nyquist-labs/projects/projects/applied-math/B-fourier-analysis-and-transforms/AM024-zero-padding-vs-resolution/README.md

# AM-024 · Zero-padding vs resolution: what interpolation does not add

> Show that zero-padding interpolates the spectrum (sharper-looking peaks, better frequency *estimates*) but cannot separate two tones closer than about 1/T — only a longer record can. The resolvability threshold is predicted and measured.

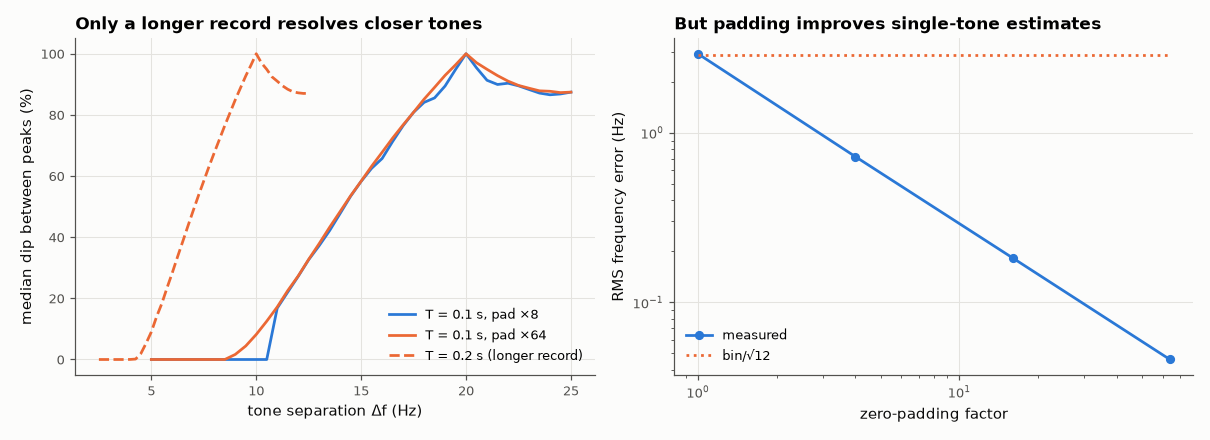
[picture p153: projects/applied-math/B-fourier-analysis-and-transforms/AM024-zero-padding-vs-resolution/figures/zeropad.png]
Zero-padding vs resolution: what interpolation does not add


*Two-tone resolvability vs separation for different padding factors and record lengths; single-tone estimation error vs padding.*

**Track:** Applied Mathematics — 218 projects in electrical engineering · **Category:** B. Fourier analysis & transforms · **Level:** Easy · **Tools:** FFT with and without zero-padding, two-tone resolution test, peak-dip criterion

**Data:** Simulated (numerical model in this repo).

## Problem

Padding an FFT with zeros makes the spectrum look smoother. Does it improve resolution?
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
