nyquist-labs/projects/projects/applied-math/B-fourier-analysis-and-transforms/AM029-time-frequency-uncertainty/README.md

# AM-029 · The time–frequency uncertainty bound, measured

> Compute the RMS duration σ_t and RMS bandwidth σ_f of many pulse shapes, show that σ_t·σ_f ≥ 1/(4π) with equality only for the Gaussian, and show that chirping or distorting a pulse moves it away from the bound.

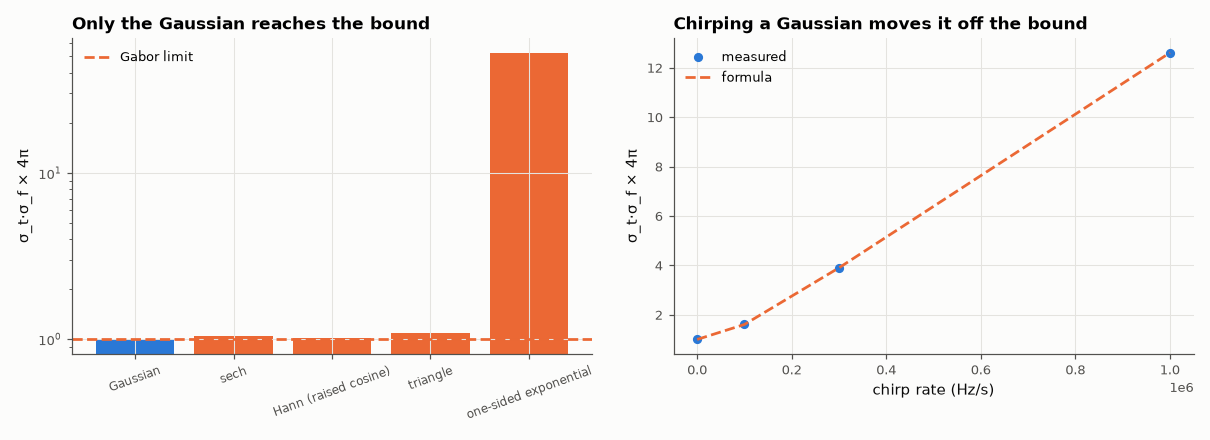
[picture p154: projects/applied-math/B-fourier-analysis-and-transforms/AM029-time-frequency-uncertainty/figures/uncertainty.png]
The time–frequency uncertainty bound, measured

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
