nyquist-labs/projects/projects/applied-math/B-fourier-analysis-and-transforms/AM037-dct-and-compression/figures/dct.png

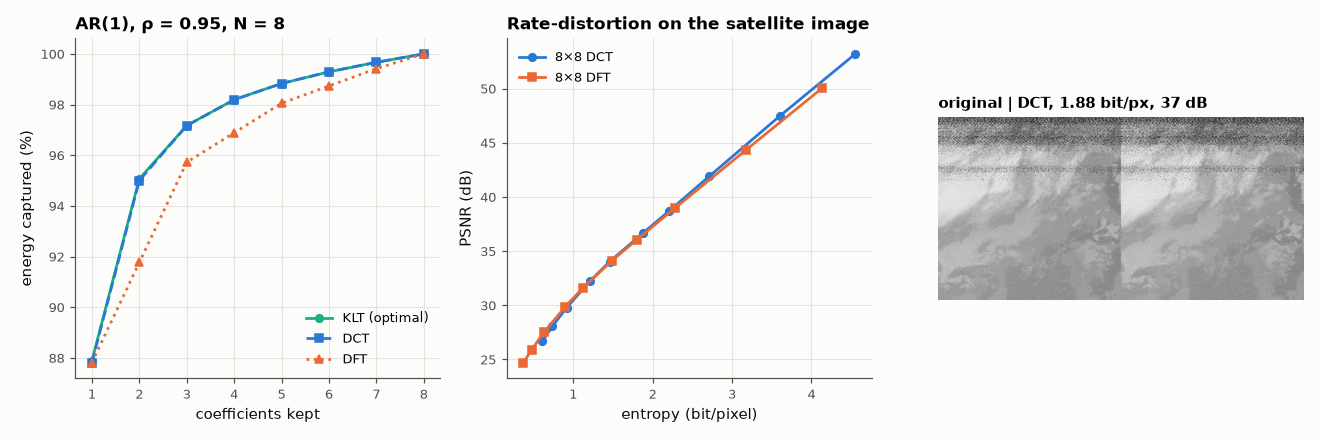
projects/applied-math/B-fourier-analysis-and-transforms/AM037-dct-and-compression/figures/dct.png
