nyquist-labs/projects/projects/applied-math/B-fourier-analysis-and-transforms/AM039-goertzel-algorithm/figures/goertzel.png

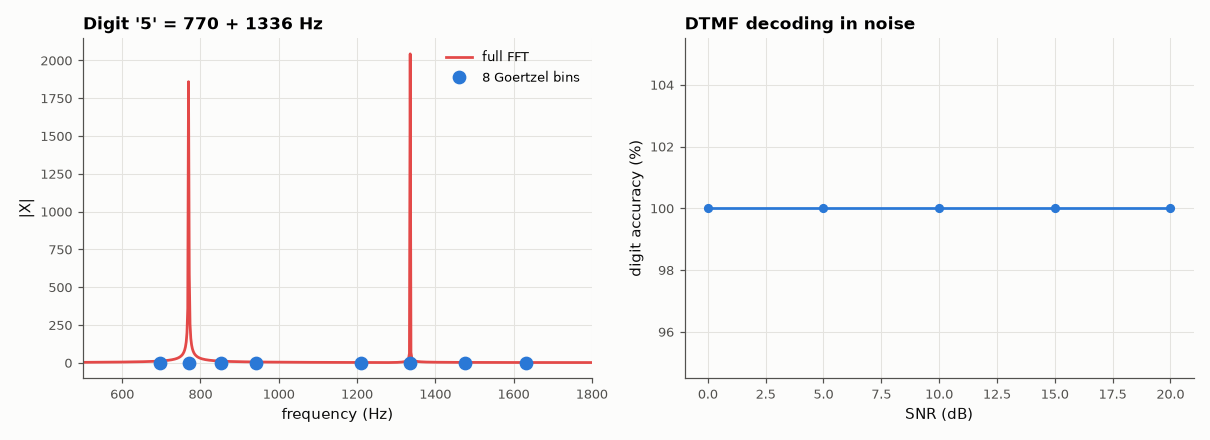
projects/applied-math/B-fourier-analysis-and-transforms/AM039-goertzel-algorithm/figures/goertzel.png
