nyquist-labs/projects/projects/applied-math/B-fourier-analysis-and-transforms/AM041-autocorrelation-and-psd/figures/wiener_khinchin.png

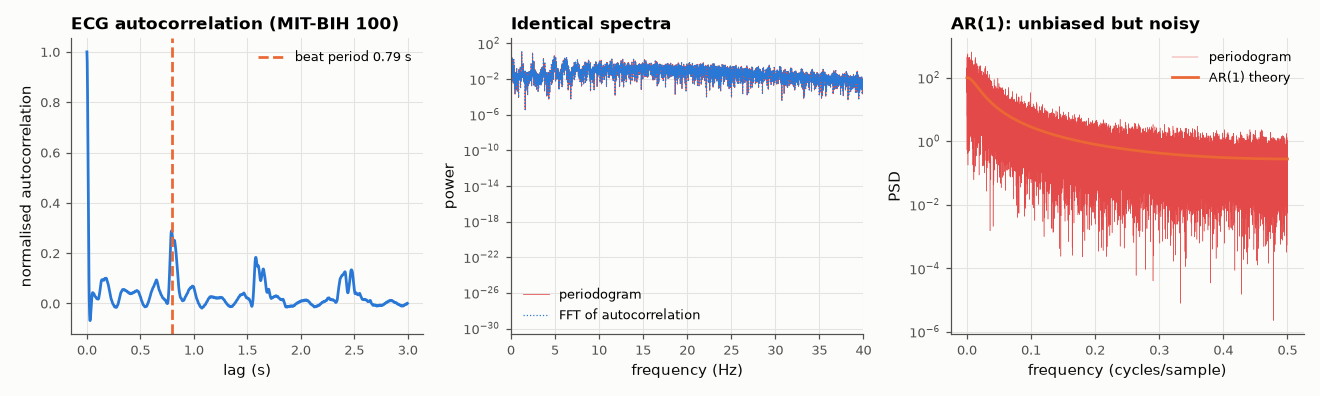
projects/applied-math/B-fourier-analysis-and-transforms/AM041-autocorrelation-and-psd/figures/wiener_khinchin.png
