nyquist-labs/projects/projects/applied-math/C-differential-equations/AM045-rlc-damping-regimes/figures/damping.png

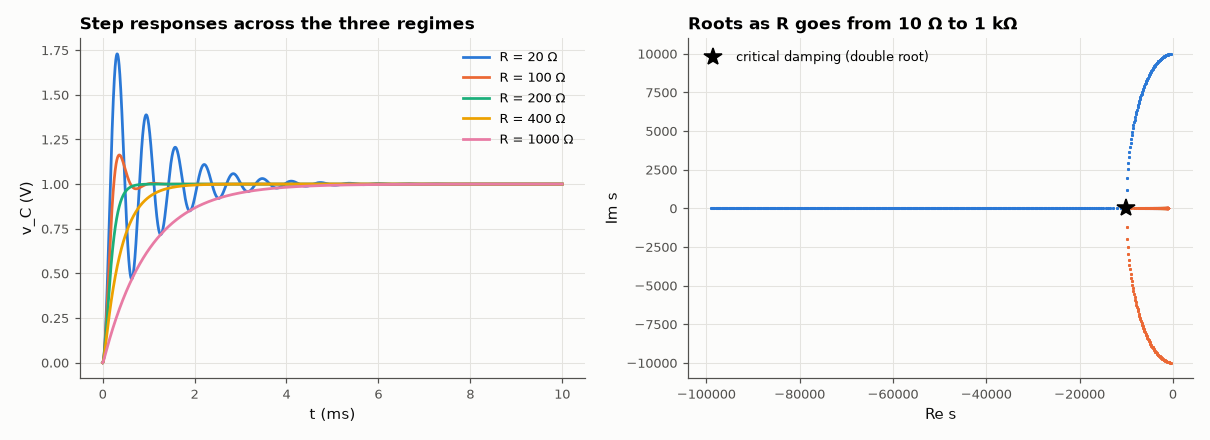
projects/applied-math/C-differential-equations/AM045-rlc-damping-regimes/figures/damping.png
