nyquist-labs/projects/projects/applied-math/C-differential-equations/AM048-stiff-odes-in-switching-circuits/figures/stiff.png

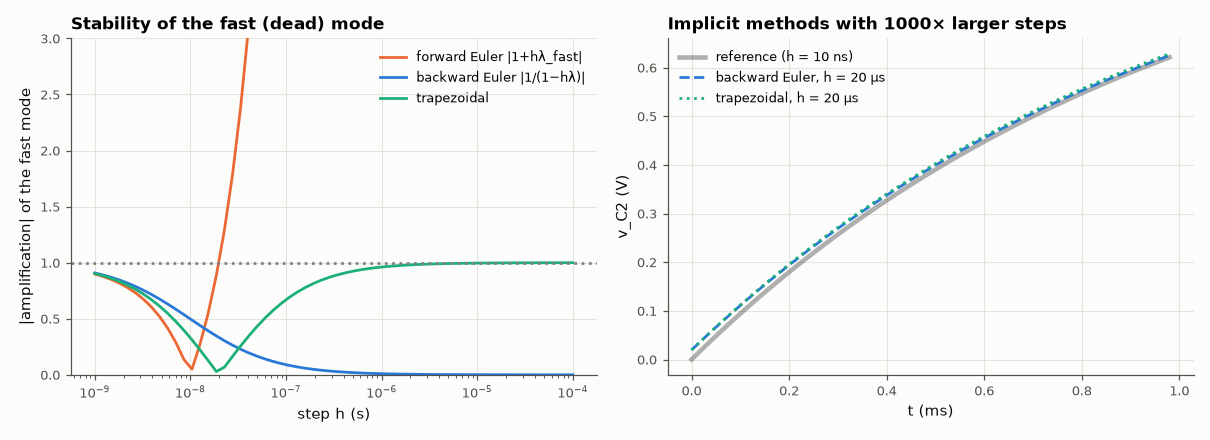
projects/applied-math/C-differential-equations/AM048-stiff-odes-in-switching-circuits/figures/stiff.png
