nyquist-labs/projects/projects/applied-math/C-differential-equations/AM051-thermal-diffusion-model/figures/heat.png

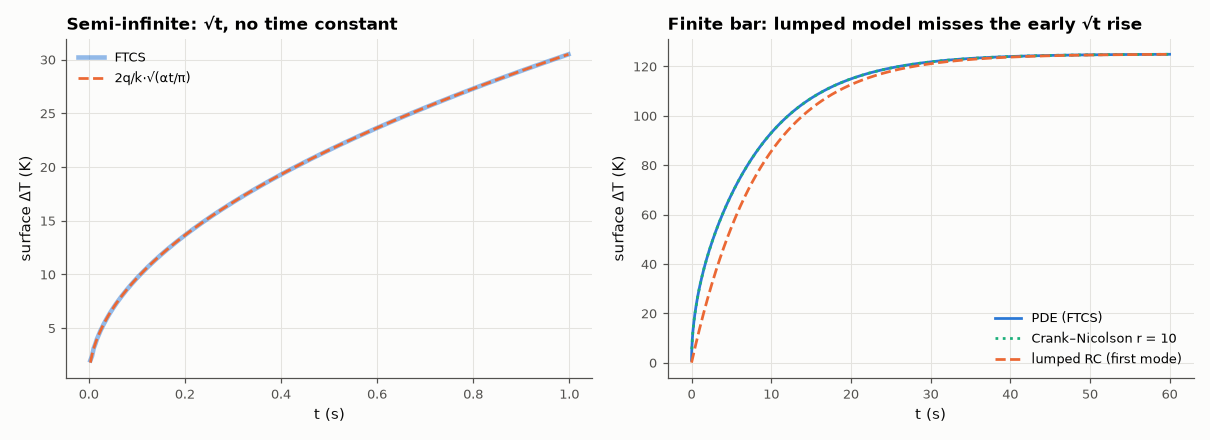
projects/applied-math/C-differential-equations/AM051-thermal-diffusion-model/figures/heat.png
