nyquist-labs/projects/projects/applied-math/C-differential-equations/AM052-1d-wave-equation/figures/wave1d.png

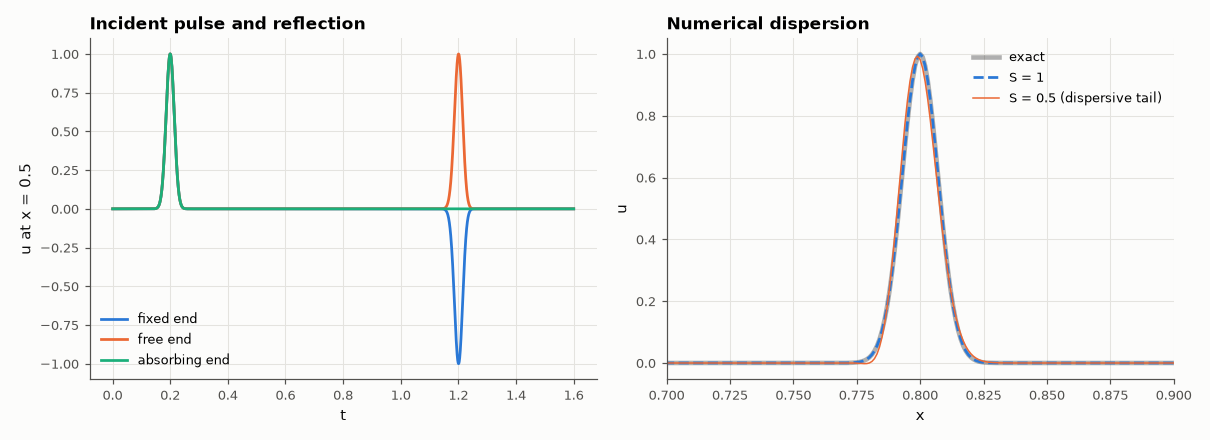
projects/applied-math/C-differential-equations/AM052-1d-wave-equation/figures/wave1d.png
