nyquist-labs/projects/projects/applied-math/C-differential-equations/AM054-van-der-pol-oscillator/figures/vanderpol.png

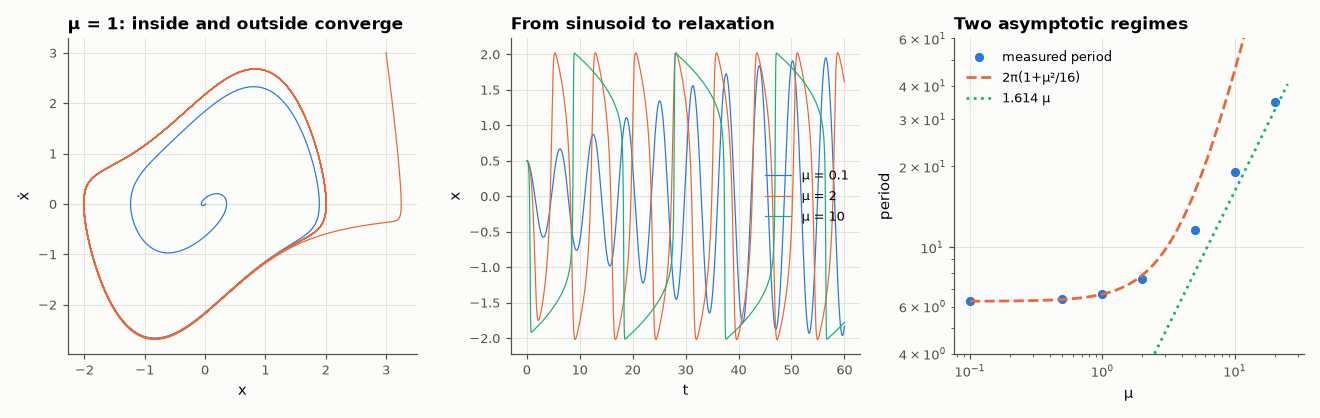
projects/applied-math/C-differential-equations/AM054-van-der-pol-oscillator/figures/vanderpol.png
