nyquist-labs/projects/projects/applied-math/C-differential-equations/AM058-limit-cycles-in-oscillators/figures/limit_cycle.png

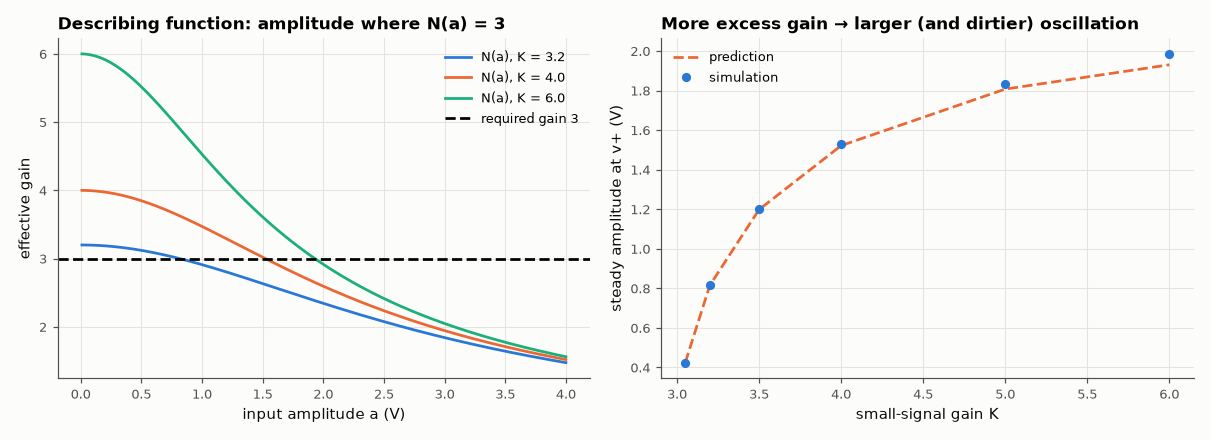
projects/applied-math/C-differential-equations/AM058-limit-cycles-in-oscillators/figures/limit_cycle.png
