nyquist-labs/projects/projects/applied-math/C-differential-equations/AM059-bifurcation-analysis/figures/bifurcation.png

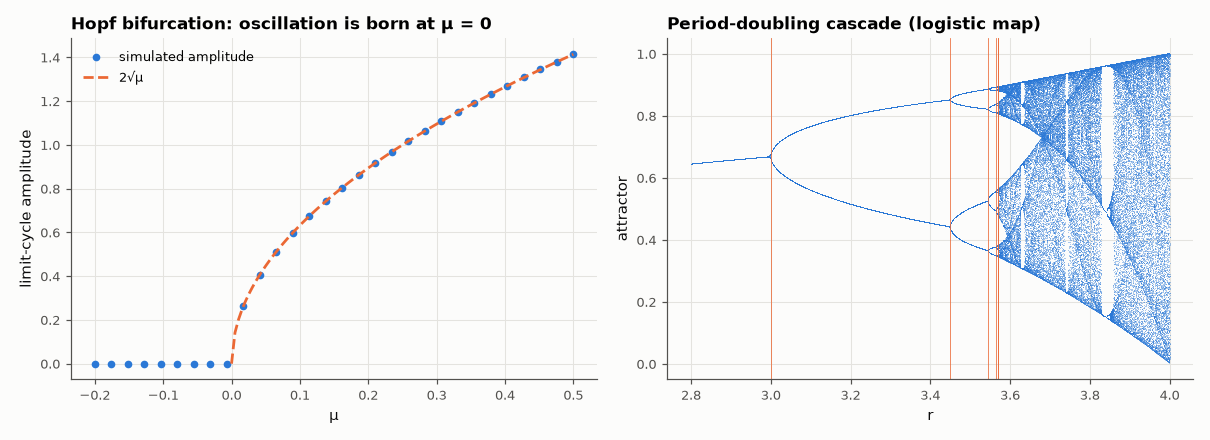
projects/applied-math/C-differential-equations/AM059-bifurcation-analysis/figures/bifurcation.png
