nyquist-labs/projects/projects/applied-math/C-differential-equations/AM060-skin-effect-diffusion/figures/skin.png

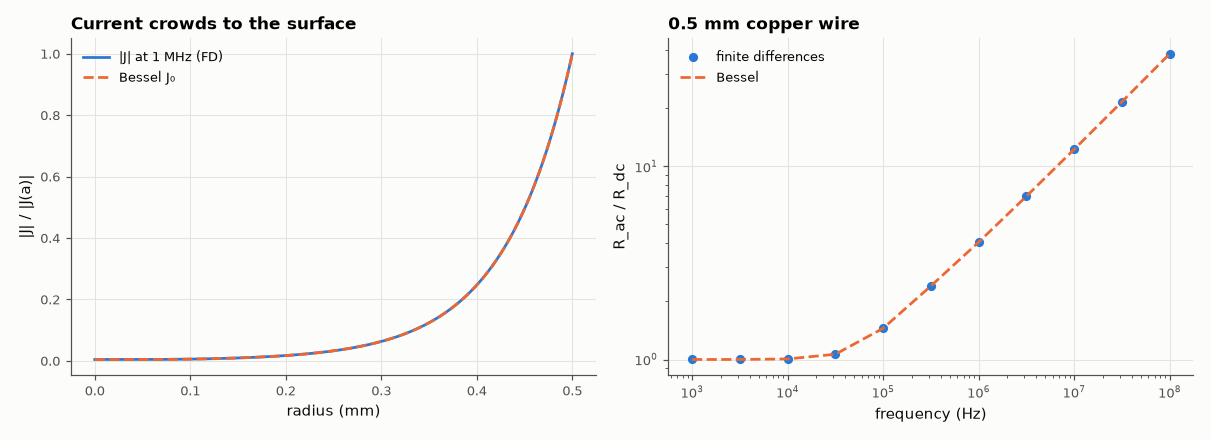
projects/applied-math/C-differential-equations/AM060-skin-effect-diffusion/figures/skin.png
