nyquist-labs/projects/projects/applied-math/D-linear-algebra/AM063-sparse-matrix-solvers/figures/sparse.png

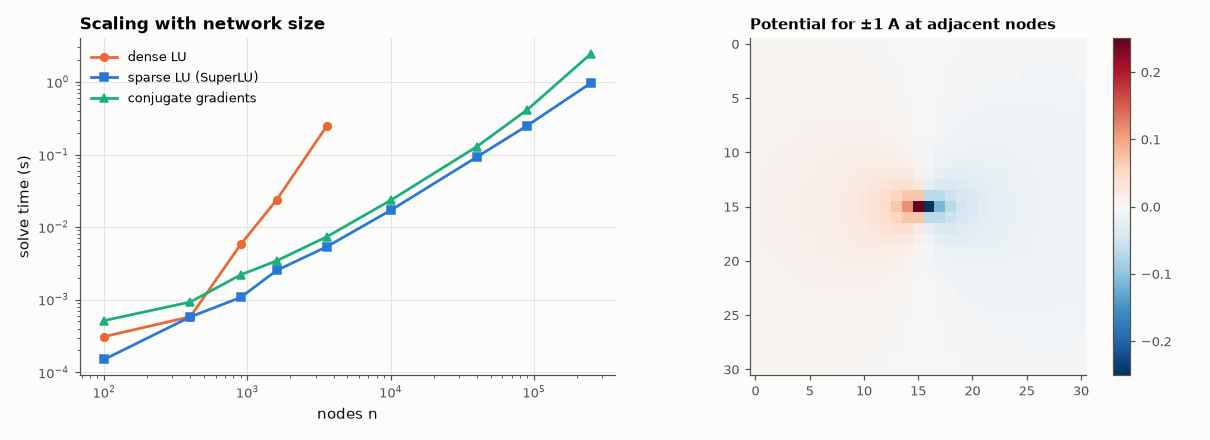
projects/applied-math/D-linear-algebra/AM063-sparse-matrix-solvers/figures/sparse.png
