nyquist-labs/projects/projects/applied-math/D-linear-algebra/AM067-controllability-and-observability/figures/controllability.png

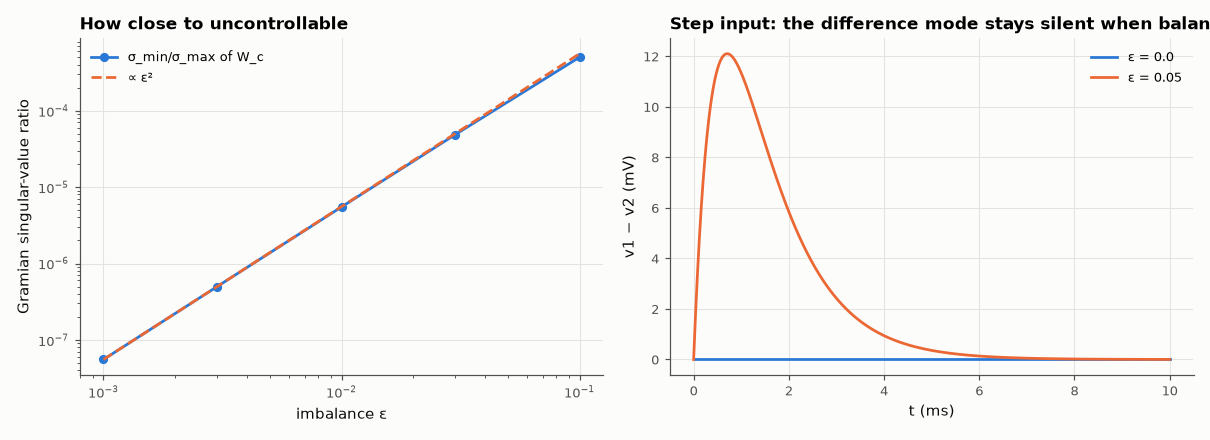
projects/applied-math/D-linear-algebra/AM067-controllability-and-observability/figures/controllability.png
