nyquist-labs/projects/projects/applied-math/D-linear-algebra/AM072-graph-laplacian-of-a-network/figures/laplacian.png

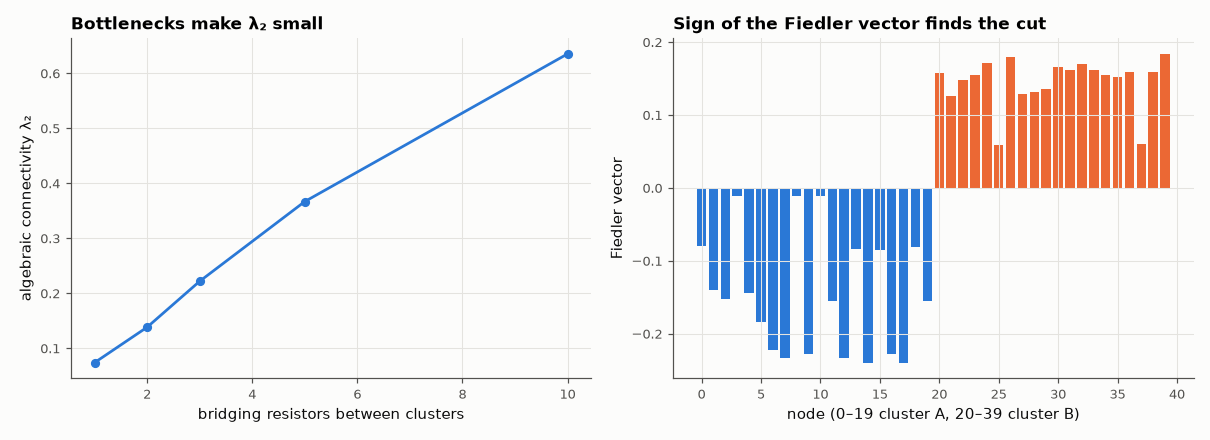
projects/applied-math/D-linear-algebra/AM072-graph-laplacian-of-a-network/figures/laplacian.png
