nyquist-labs/projects/projects/applied-math/D-linear-algebra/AM073-two-port-parameters/figures/twoport.png

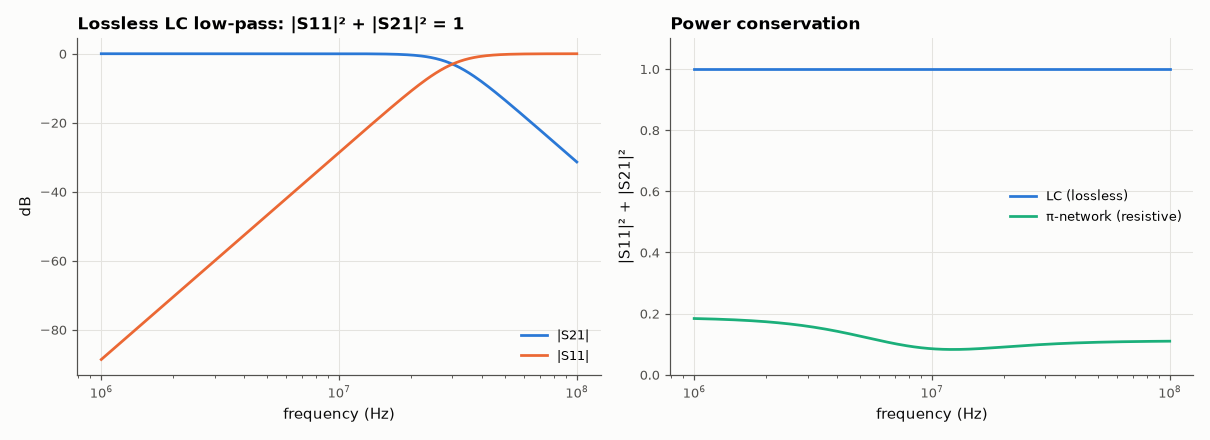
projects/applied-math/D-linear-algebra/AM073-two-port-parameters/figures/twoport.png
