nyquist-labs/projects/projects/applied-math/D-linear-algebra/AM074-cascade-abcd-matrices/figures/abcd.png

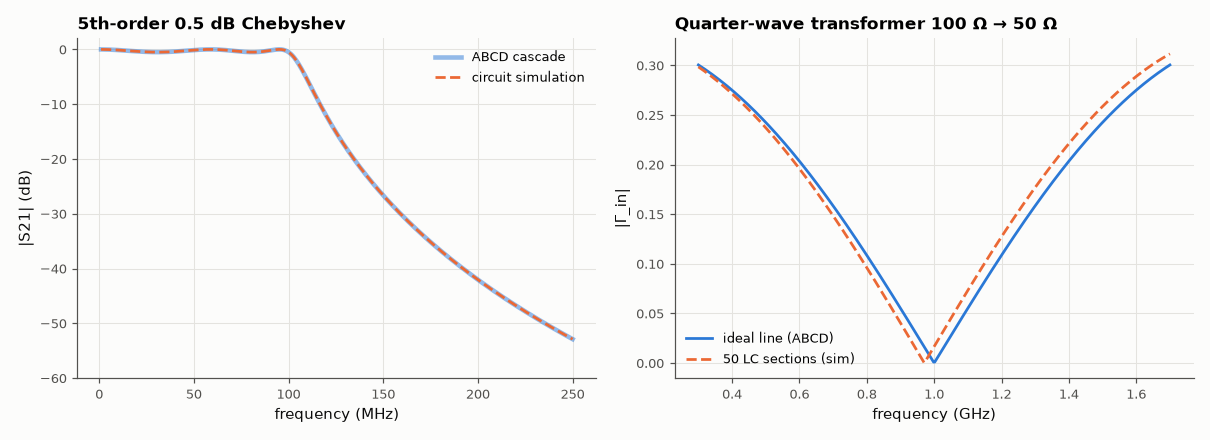
projects/applied-math/D-linear-algebra/AM074-cascade-abcd-matrices/figures/abcd.png
