nyquist-labs/projects/projects/applied-math/D-linear-algebra/AM075-mimo-channel-capacity/figures/mimo.png

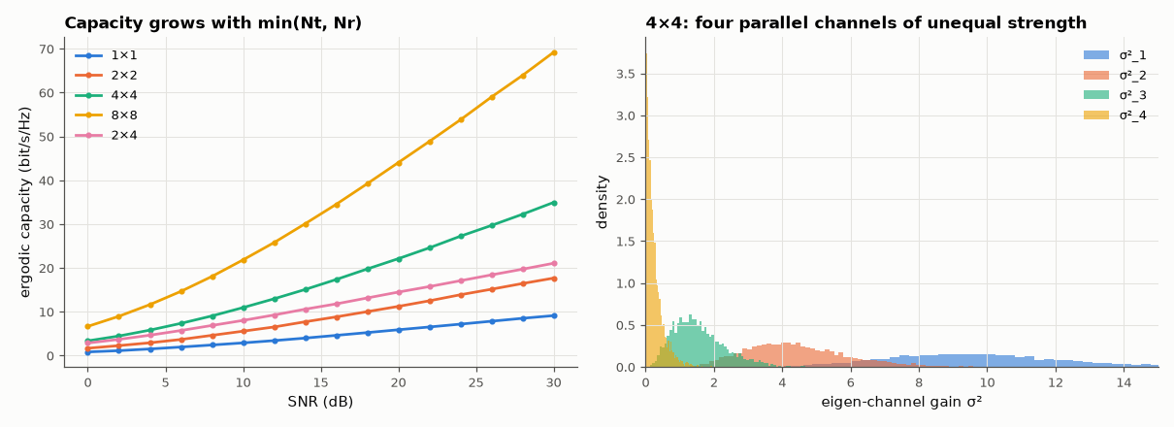
projects/applied-math/D-linear-algebra/AM075-mimo-channel-capacity/figures/mimo.png
