nyquist-labs/projects/projects/applied-math/D-linear-algebra/AM076-beamforming-as-matrix-algebra/figures/beamforming.png

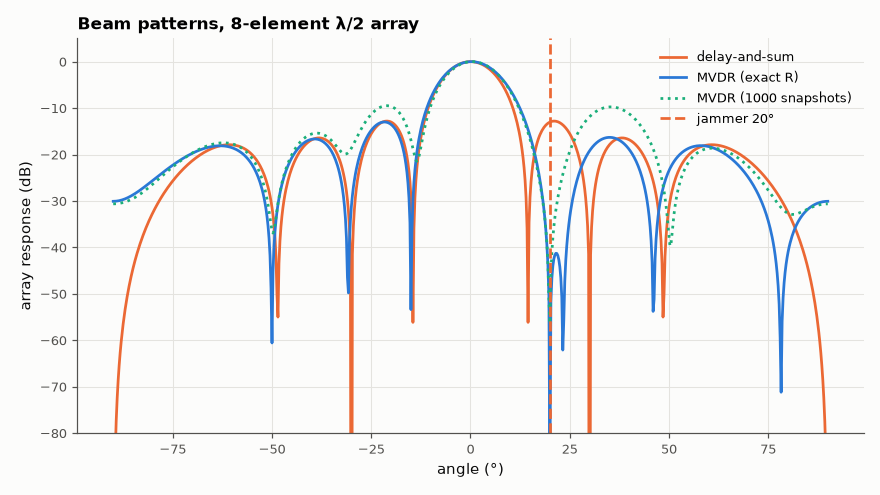
projects/applied-math/D-linear-algebra/AM076-beamforming-as-matrix-algebra/figures/beamforming.png
