nyquist-labs/projects/projects/applied-math/D-linear-algebra/AM078-condition-number-study/figures/conditioning.png

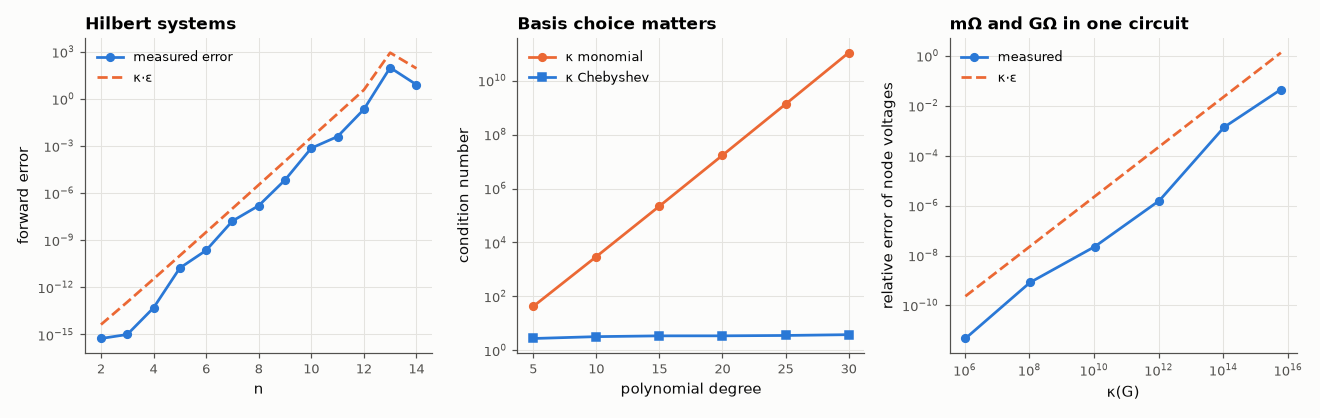
projects/applied-math/D-linear-algebra/AM078-condition-number-study/figures/conditioning.png
