nyquist-labs/projects/projects/applied-math/D-linear-algebra/AM079-krylov-model-reduction/figures/mor.png

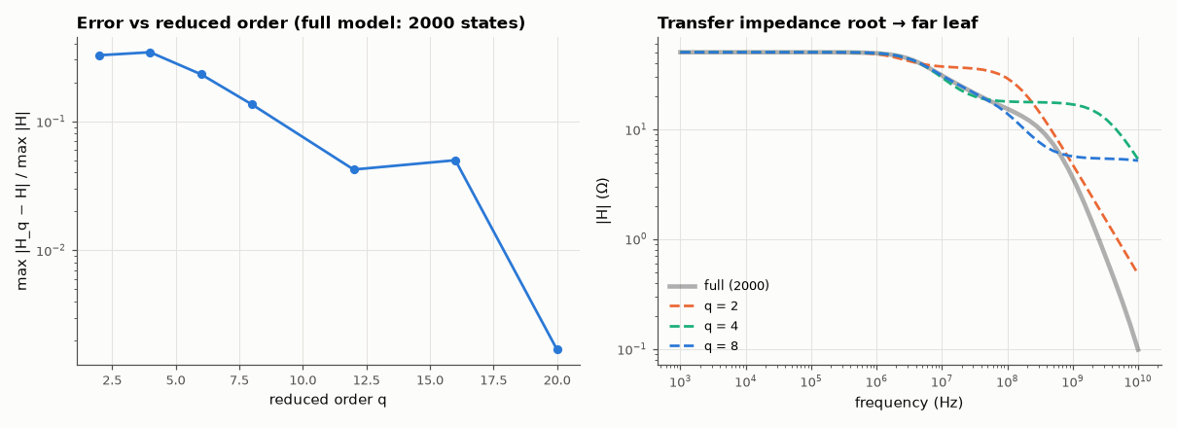
projects/applied-math/D-linear-algebra/AM079-krylov-model-reduction/figures/mor.png
