nyquist-labs/projects/projects/applied-math/E-probability-and-stochastic-processes/AM084-ber-vs-snr-simulation/figures/ber.png

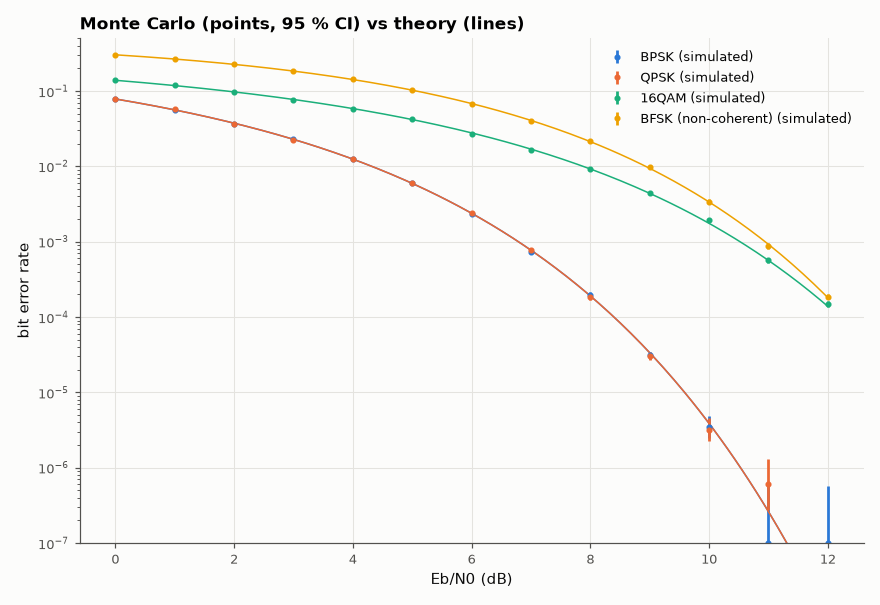
projects/applied-math/E-probability-and-stochastic-processes/AM084-ber-vs-snr-simulation/figures/ber.png
