nyquist-labs/projects/projects/applied-math/E-probability-and-stochastic-processes/AM085-q-function-derivation/figures/qfunction.png

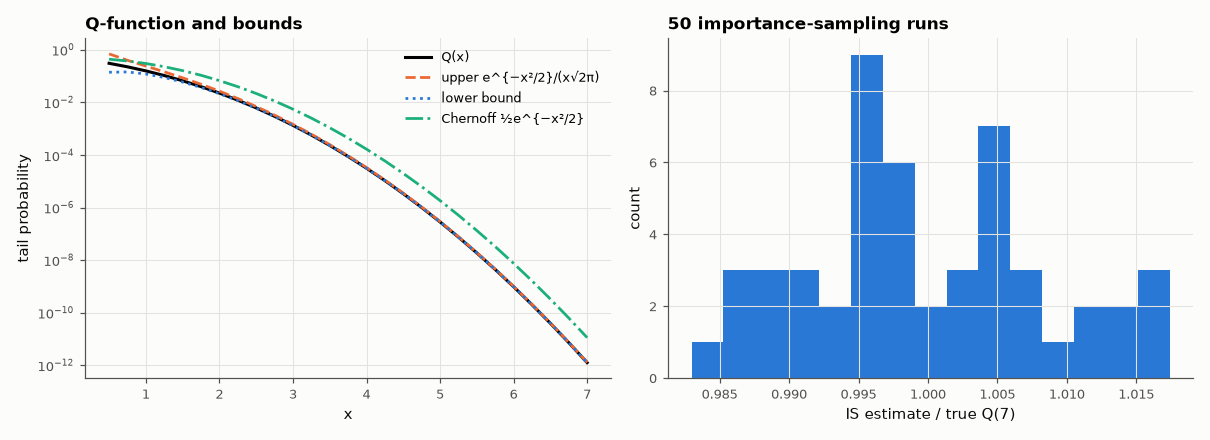
projects/applied-math/E-probability-and-stochastic-processes/AM085-q-function-derivation/figures/qfunction.png
