nyquist-labs/projects/projects/applied-math/E-probability-and-stochastic-processes/AM088-markov-chain-channel-model/figures/gilbert_elliott.png

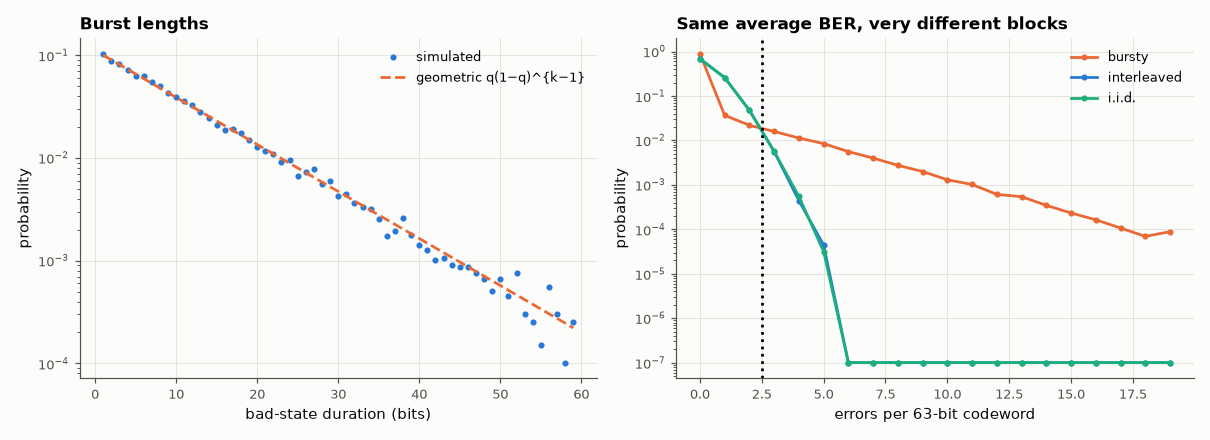
projects/applied-math/E-probability-and-stochastic-processes/AM088-markov-chain-channel-model/figures/gilbert_elliott.png
