nyquist-labs/projects/projects/applied-math/E-probability-and-stochastic-processes/AM092-map-estimation/figures/map.png

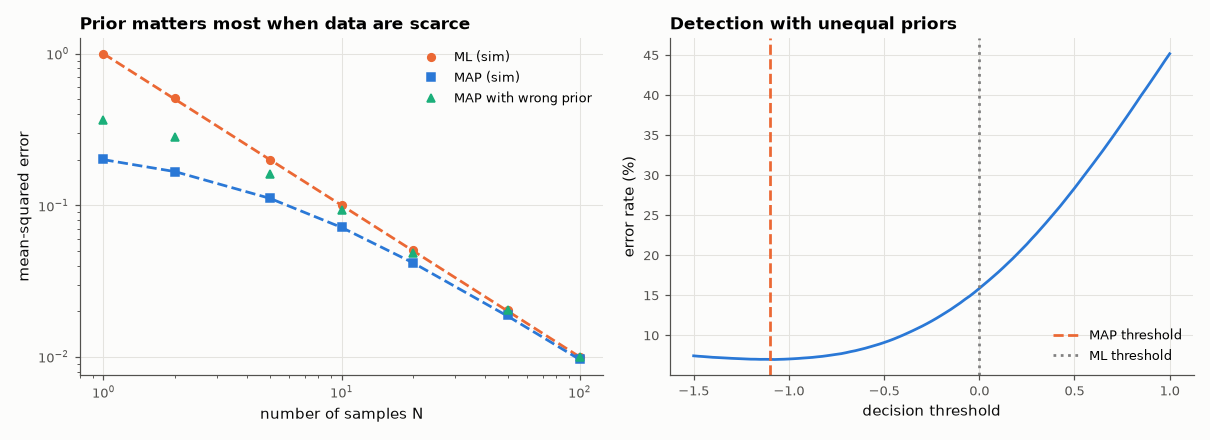
projects/applied-math/E-probability-and-stochastic-processes/AM092-map-estimation/figures/map.png
