nyquist-labs/projects/projects/applied-math/E-probability-and-stochastic-processes/AM096-wiener-filter/figures/wiener.png

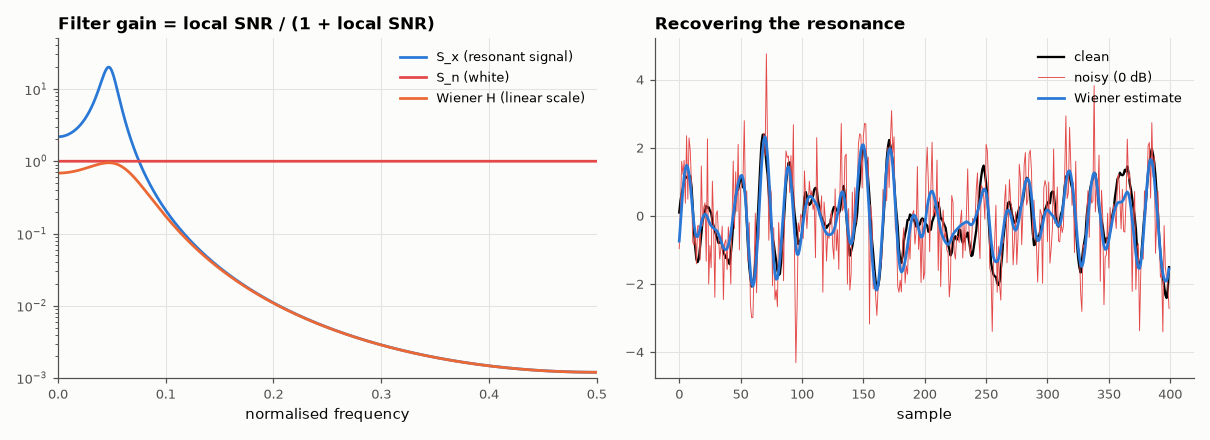
projects/applied-math/E-probability-and-stochastic-processes/AM096-wiener-filter/figures/wiener.png
