nyquist-labs/projects/projects/applied-math/E-probability-and-stochastic-processes/AM097-lms-convergence-analysis/figures/lms.png

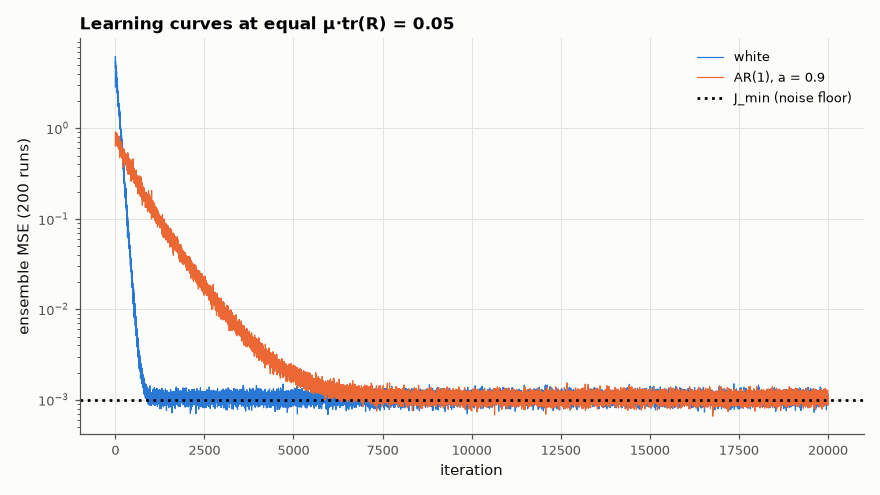
projects/applied-math/E-probability-and-stochastic-processes/AM097-lms-convergence-analysis/figures/lms.png
