nyquist-labs/projects/projects/applied-math/E-probability-and-stochastic-processes/AM098-random-walk-in-circuits/figures/random_walk.png

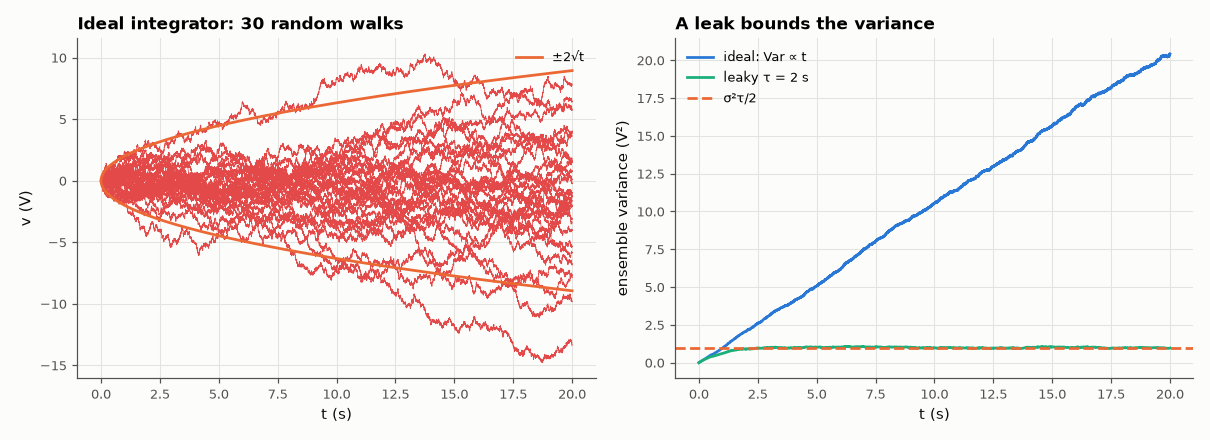
projects/applied-math/E-probability-and-stochastic-processes/AM098-random-walk-in-circuits/figures/random_walk.png
