nyquist-labs/projects/projects/applied-math/F-optimisation/AM101-impedance-matching-optimisation/figures/matching.png

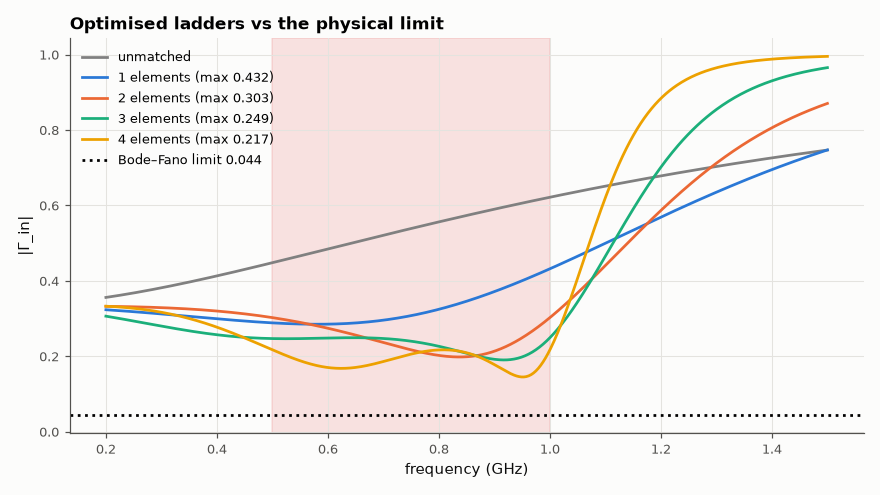
projects/applied-math/F-optimisation/AM101-impedance-matching-optimisation/figures/matching.png
