nyquist-labs/projects/projects/applied-math/F-optimisation/AM103-gradient-descent-parameter-fitting/figures/diode_fit.png

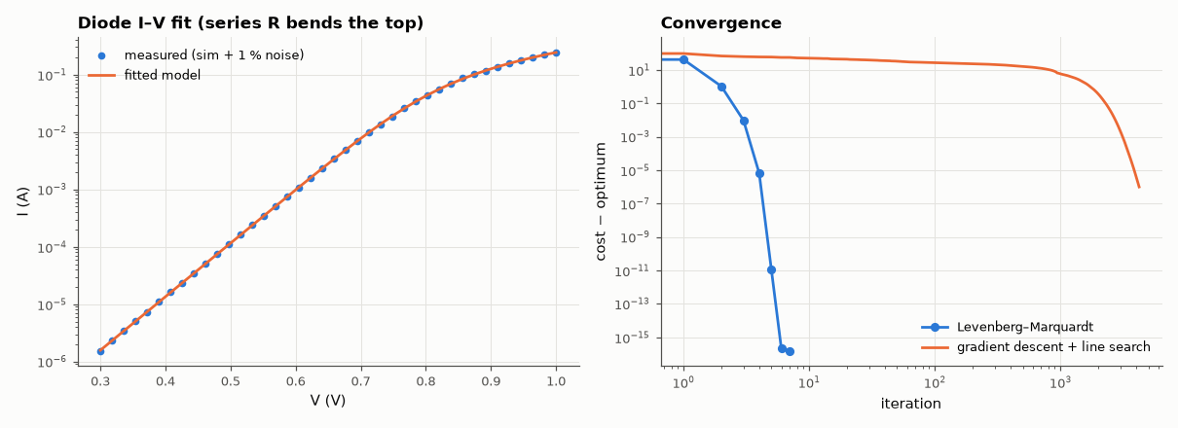
projects/applied-math/F-optimisation/AM103-gradient-descent-parameter-fitting/figures/diode_fit.png
