nyquist-labs/projects/projects/applied-math/F-optimisation/AM109-mppt-as-hill-climbing/figures/mppt.png

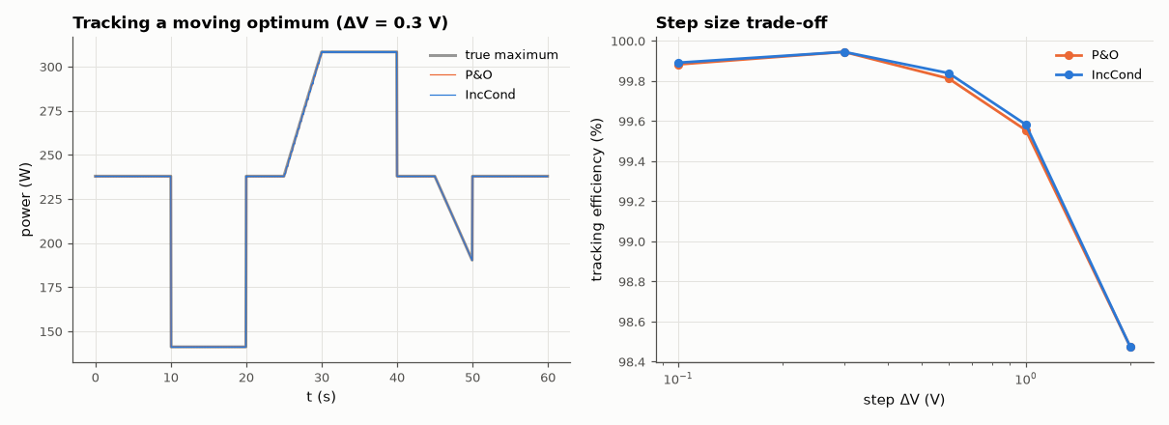
projects/applied-math/F-optimisation/AM109-mppt-as-hill-climbing/figures/mppt.png
