nyquist-labs/projects/projects/applied-math/F-optimisation/AM110-minimax-approximation/figures/minimax.png

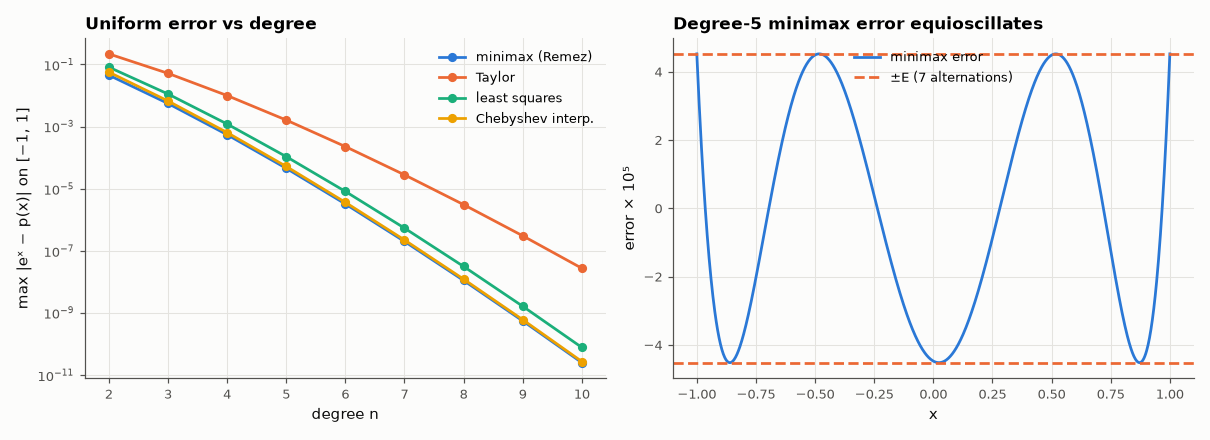
projects/applied-math/F-optimisation/AM110-minimax-approximation/figures/minimax.png
