nyquist-labs/projects/projects/applied-math/F-optimisation/AM111-least-squares-curve-fitting/figures/battery_fit.png

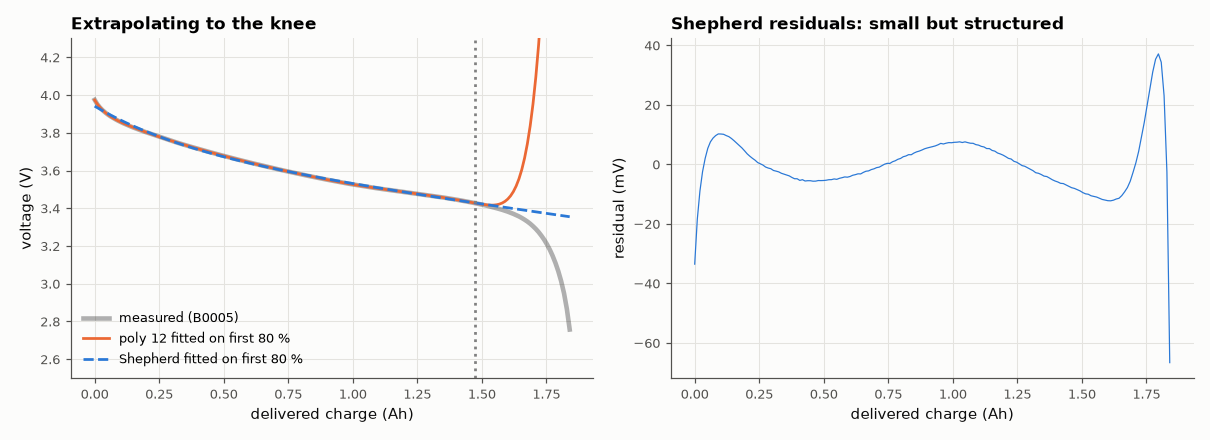
projects/applied-math/F-optimisation/AM111-least-squares-curve-fitting/figures/battery_fit.png
