nyquist-labs/projects/projects/applied-math/F-optimisation/AM114-multi-objective-trade-study/figures/pareto.png

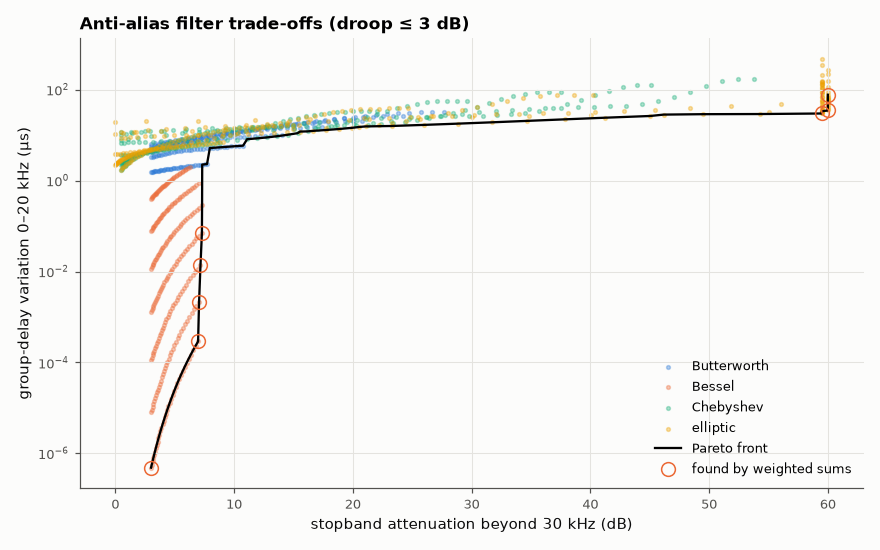
projects/applied-math/F-optimisation/AM114-multi-objective-trade-study/figures/pareto.png
