nyquist-labs/projects/projects/applied-math/G-numerical-methods/AM116-transient-integration-methods/figures/trap_vs_be.png

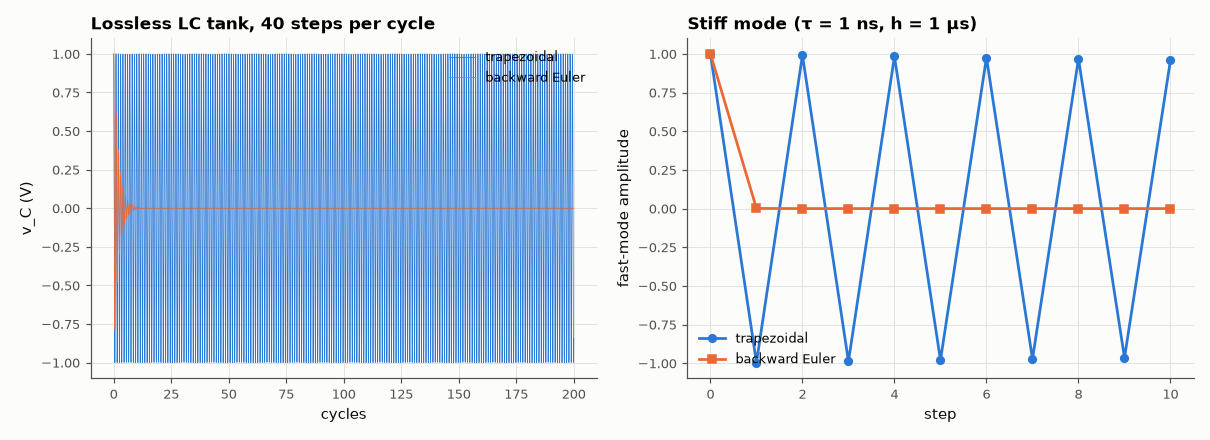
projects/applied-math/G-numerical-methods/AM116-transient-integration-methods/figures/trap_vs_be.png
