nyquist-labs/projects/projects/applied-math/G-numerical-methods/AM119-finite-element-basics/figures/fem_coax.png

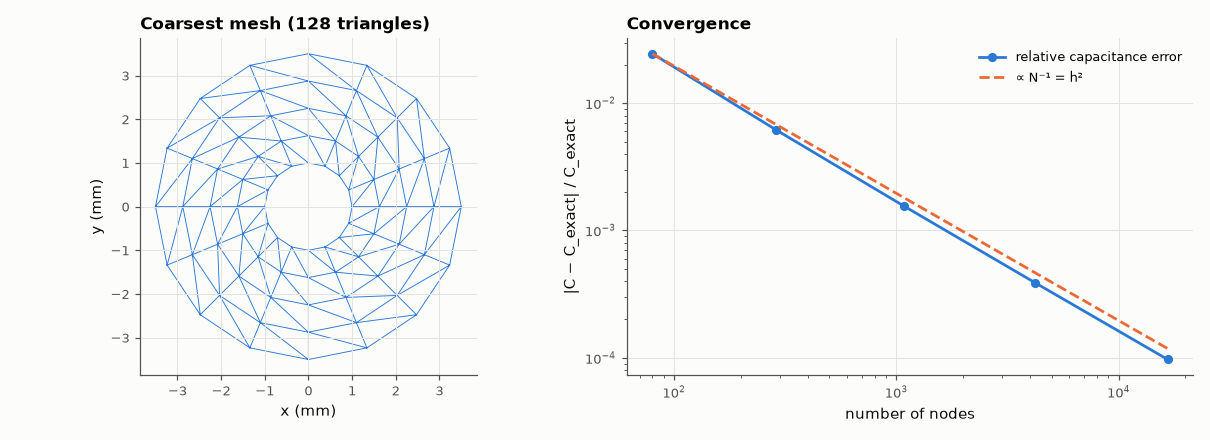
projects/applied-math/G-numerical-methods/AM119-finite-element-basics/figures/fem_coax.png
