nyquist-labs/projects/projects/applied-math/G-numerical-methods/AM120-method-of-moments/figures/mom.png

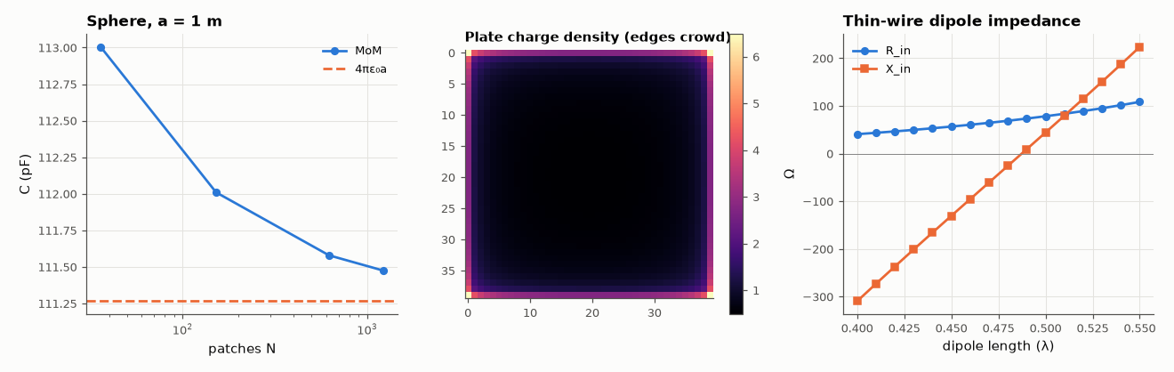
projects/applied-math/G-numerical-methods/AM120-method-of-moments/figures/mom.png
