nyquist-labs/projects/projects/applied-math/G-numerical-methods/AM121-numerical-fourier-coefficients/figures/fourier_quadrature.png

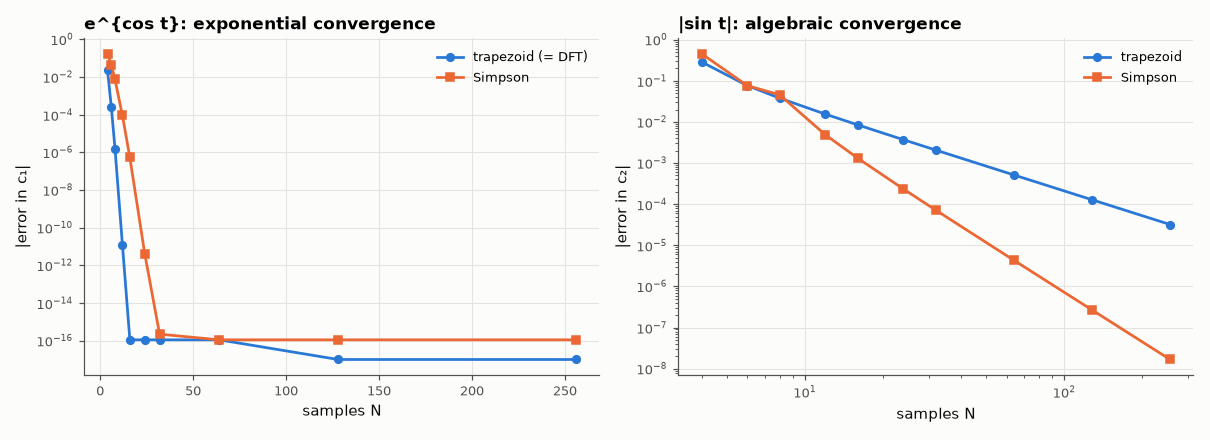
projects/applied-math/G-numerical-methods/AM121-numerical-fourier-coefficients/figures/fourier_quadrature.png
