nyquist-labs/projects/projects/applied-math/G-numerical-methods/AM124-fixed-vs-floating-point/figures/fixed_point.png

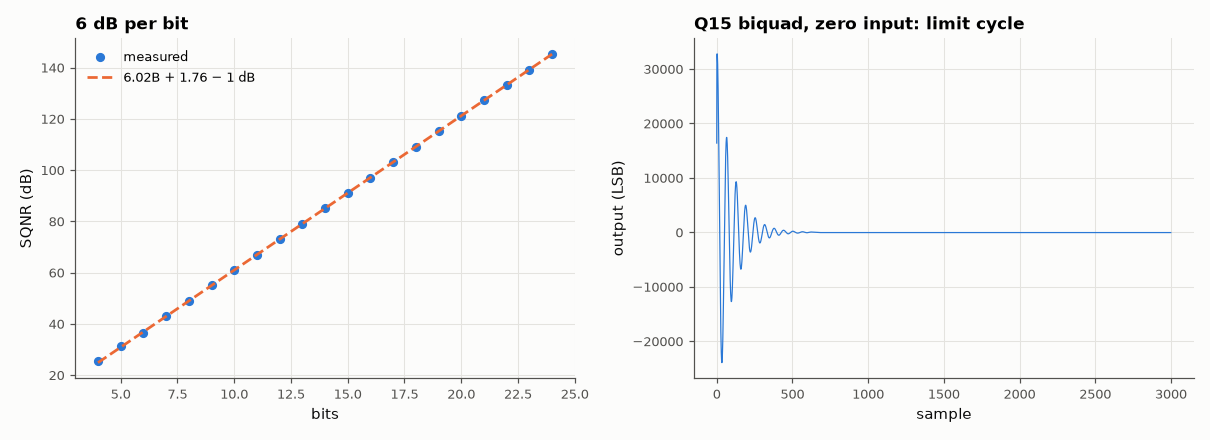
projects/applied-math/G-numerical-methods/AM124-fixed-vs-floating-point/figures/fixed_point.png
