nyquist-labs/projects/projects/applied-math/G-numerical-methods/AM125-quantisation-error-propagation/figures/cascade_noise.png

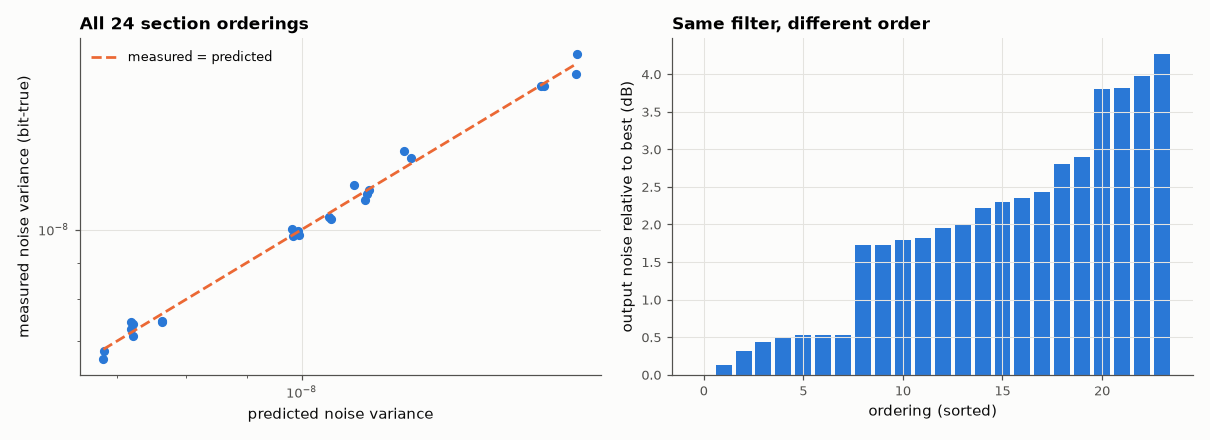
projects/applied-math/G-numerical-methods/AM125-quantisation-error-propagation/figures/cascade_noise.png
