nyquist-labs/projects/projects/applied-math/G-numerical-methods/AM126-conditioning-in-dsp/figures/conditioning_dsp.png

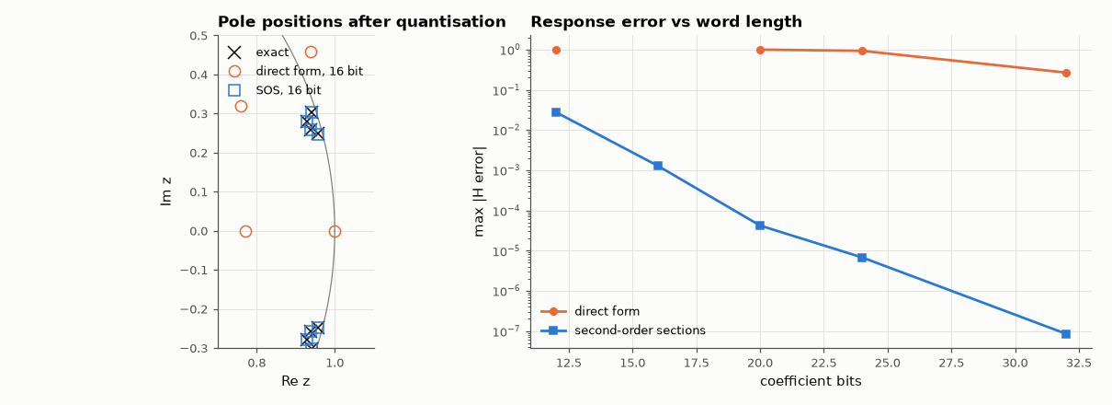
projects/applied-math/G-numerical-methods/AM126-conditioning-in-dsp/figures/conditioning_dsp.png
