nyquist-labs/projects/projects/applied-math/G-numerical-methods/AM128-numerical-differentiation/figures/numdiff.png

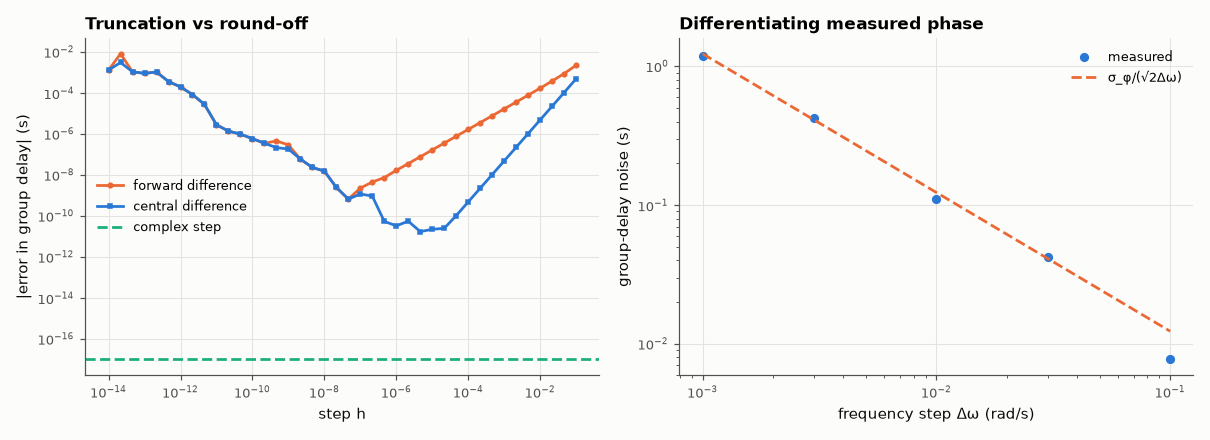
projects/applied-math/G-numerical-methods/AM128-numerical-differentiation/figures/numdiff.png
