nyquist-labs/projects/projects/applied-math/H-discrete-math-finite-fields-and-coding/AM134-quine-mccluskey-minimiser/figures/qm.png

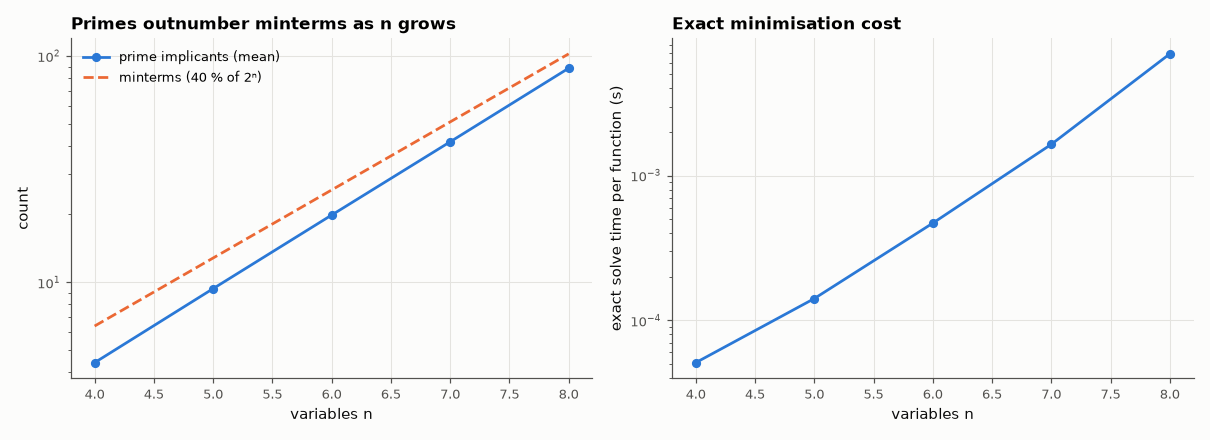
projects/applied-math/H-discrete-math-finite-fields-and-coding/AM134-quine-mccluskey-minimiser/figures/qm.png
