nyquist-labs/projects/projects/applied-math/H-discrete-math-finite-fields-and-coding/AM135-boolean-identity-checker/figures/consensus.png

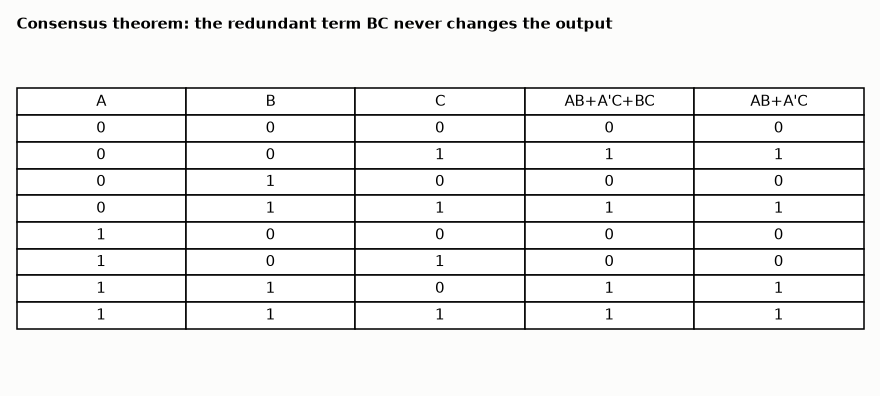
projects/applied-math/H-discrete-math-finite-fields-and-coding/AM135-boolean-identity-checker/figures/consensus.png
