nyquist-labs/projects/projects/applied-math/H-discrete-math-finite-fields-and-coding/AM136-binary-decision-diagrams/figures/bdd.png

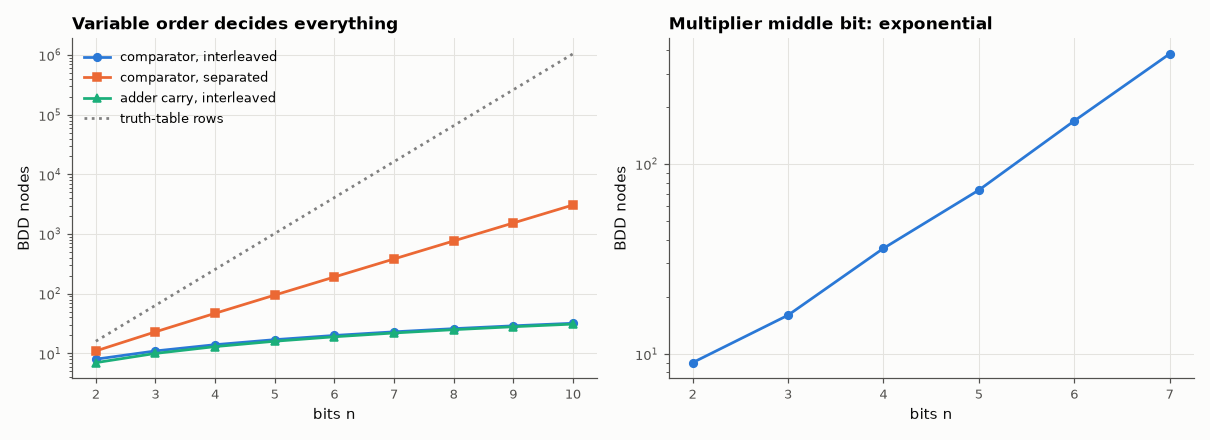
projects/applied-math/H-discrete-math-finite-fields-and-coding/AM136-binary-decision-diagrams/figures/bdd.png
