nyquist-labs/projects/projects/applied-math/H-discrete-math-finite-fields-and-coding/AM138-carry-lookahead-derivation/figures/cla.png

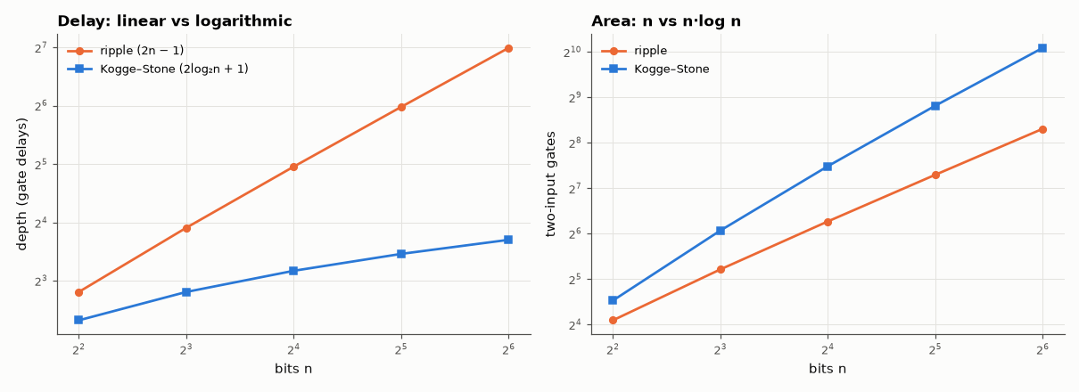
projects/applied-math/H-discrete-math-finite-fields-and-coding/AM138-carry-lookahead-derivation/figures/cla.png
