nyquist-labs/projects/projects/applied-math/H-discrete-math-finite-fields-and-coding/AM140-state-encoding-optimisation/figures/encodings.png

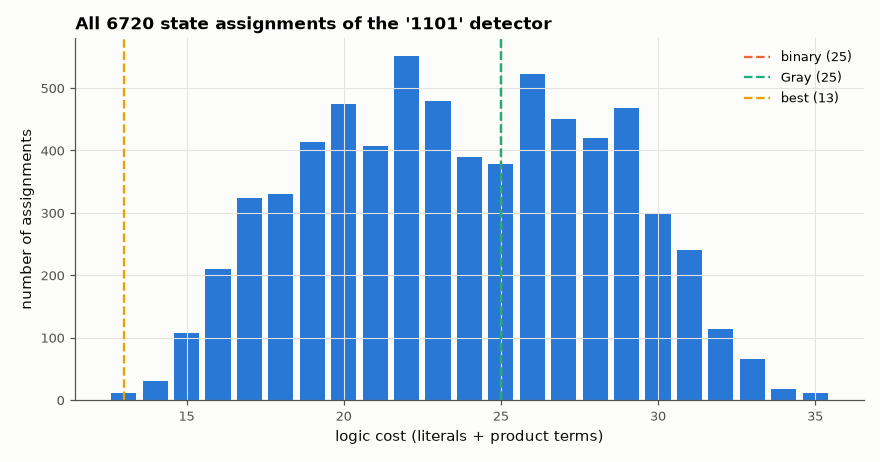
projects/applied-math/H-discrete-math-finite-fields-and-coding/AM140-state-encoding-optimisation/figures/encodings.png
