nyquist-labs/projects/projects/applied-math/H-discrete-math-finite-fields-and-coding/AM141-gray-code-generator/figures/gray.png

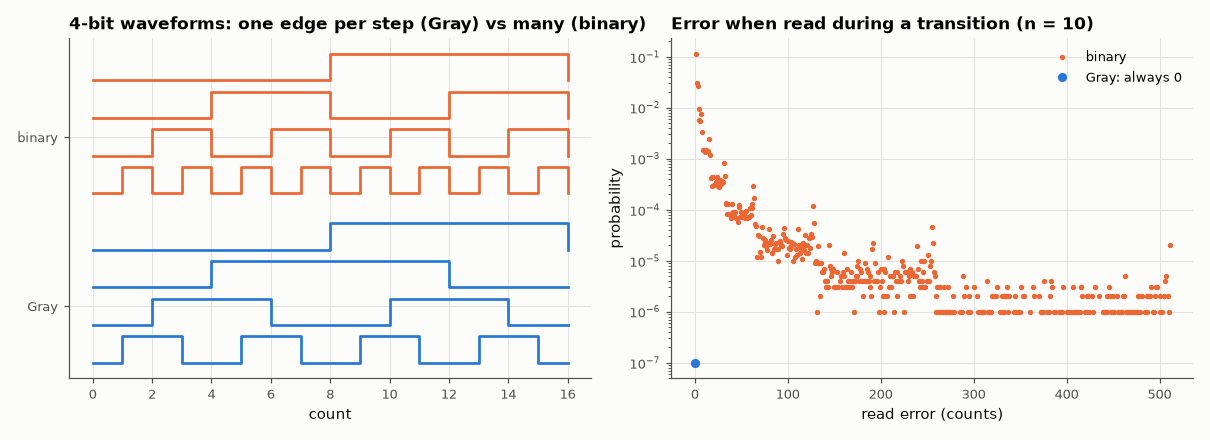
projects/applied-math/H-discrete-math-finite-fields-and-coding/AM141-gray-code-generator/figures/gray.png
