nyquist-labs/projects/projects/applied-math/H-discrete-math-finite-fields-and-coding/AM144-crc-as-polynomial-division/figures/crc.png

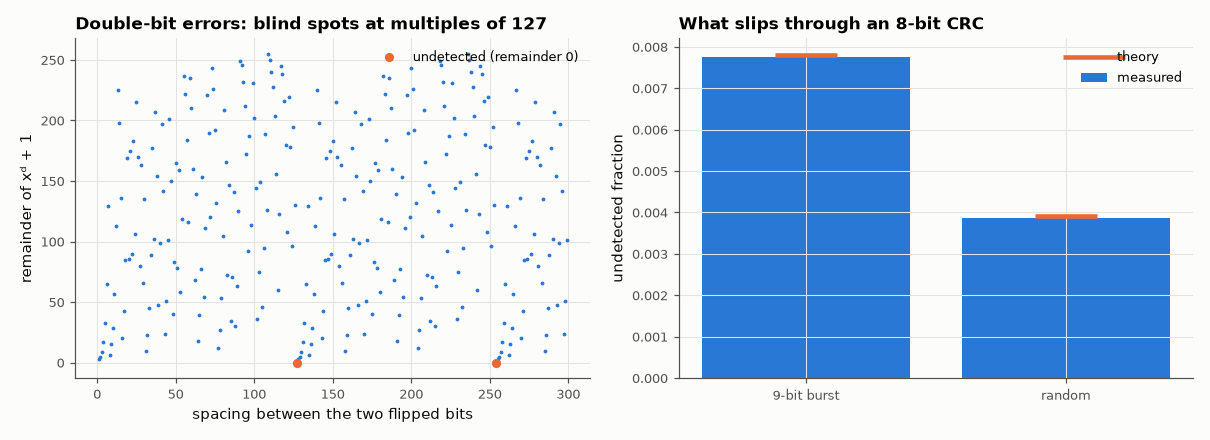
projects/applied-math/H-discrete-math-finite-fields-and-coding/AM144-crc-as-polynomial-division/figures/crc.png
