nyquist-labs/projects/projects/applied-math/H-discrete-math-finite-fields-and-coding/AM151-huffman-coding/figures/huffman.png

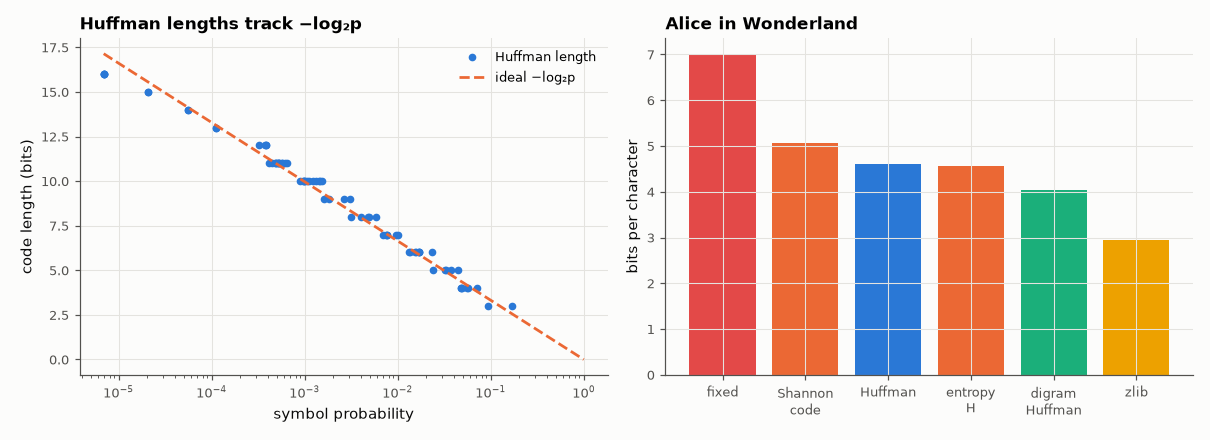
projects/applied-math/H-discrete-math-finite-fields-and-coding/AM151-huffman-coding/figures/huffman.png
