nyquist-labs/projects/projects/applied-math/J-statistics-and-learning-on-real-signals/AM174-lda-from-scratch/figures/lda.png

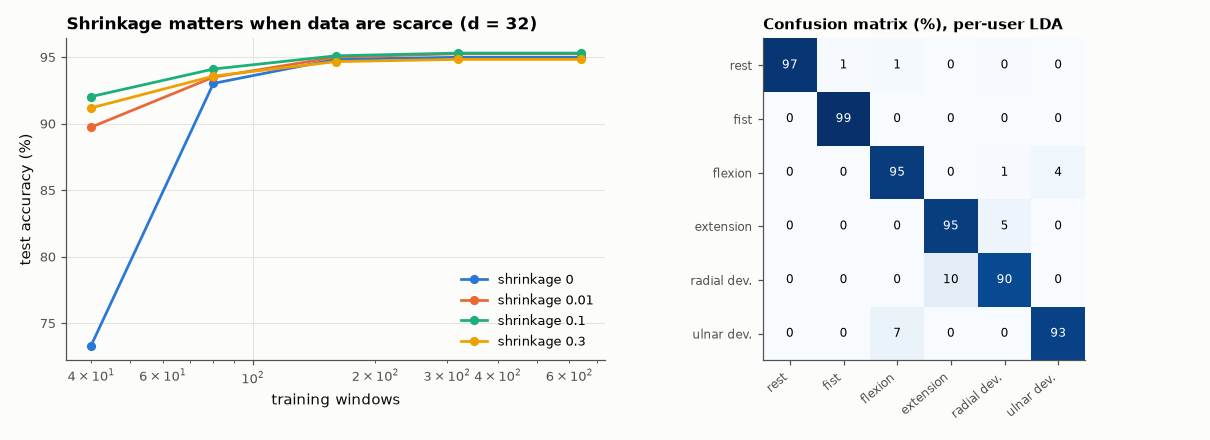
projects/applied-math/J-statistics-and-learning-on-real-signals/AM174-lda-from-scratch/figures/lda.png
