nyquist-labs/projects/projects/applied-math/J-statistics-and-learning-on-real-signals/AM180-confusion-matrices-and-class-imbalance/figures/imbalance.png

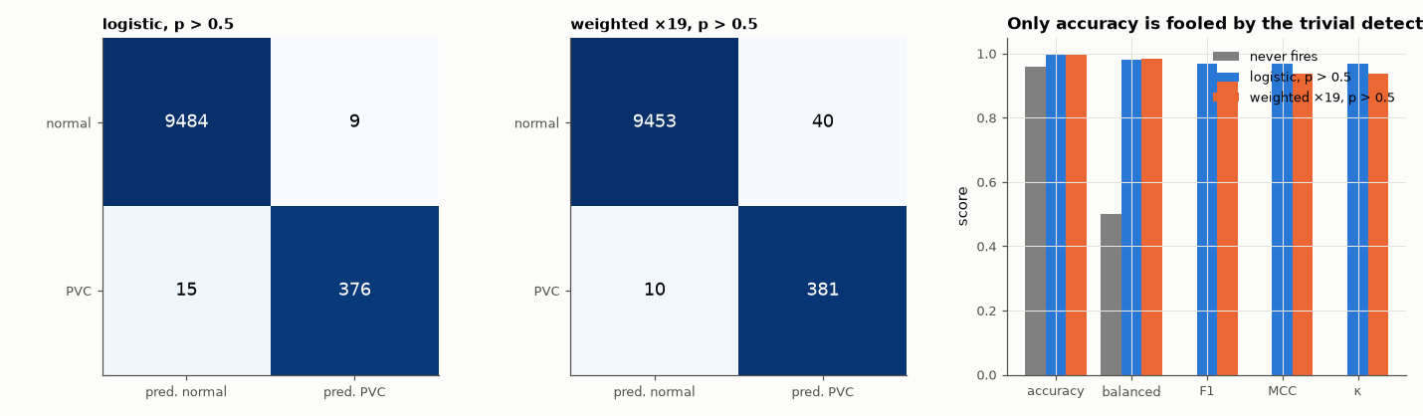
projects/applied-math/J-statistics-and-learning-on-real-signals/AM180-confusion-matrices-and-class-imbalance/figures/imbalance.png
