nyquist-labs/projects/projects/applied-math/J-statistics-and-learning-on-real-signals/AM182-clustering-real-signals/figures/clustering.png

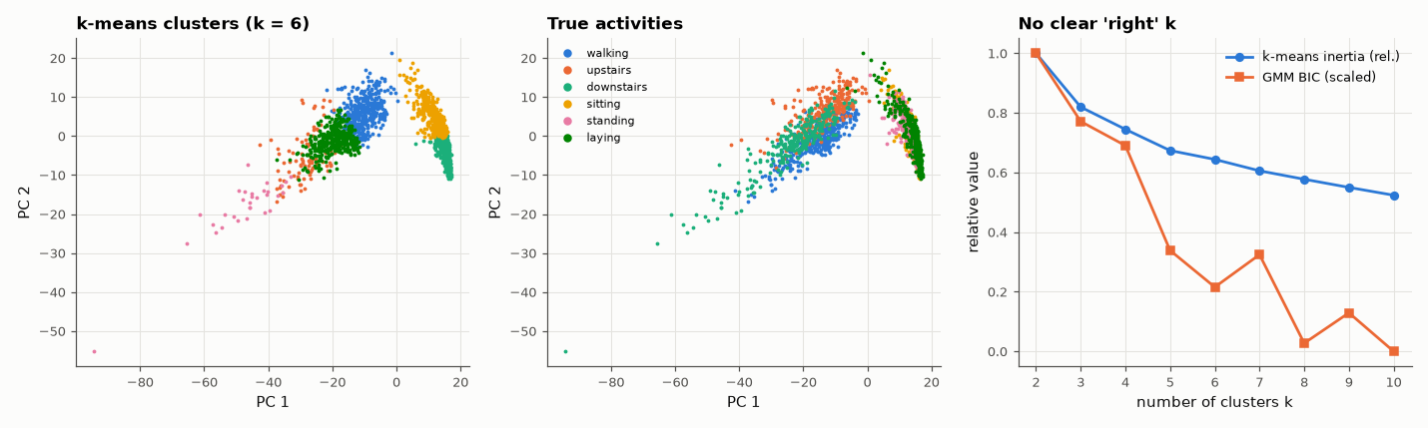
projects/applied-math/J-statistics-and-learning-on-real-signals/AM182-clustering-real-signals/figures/clustering.png
