nyquist-labs/projects/projects/applied-math/J-statistics-and-learning-on-real-signals/AM187-bootstrap-confidence-intervals/figures/bootstrap.png

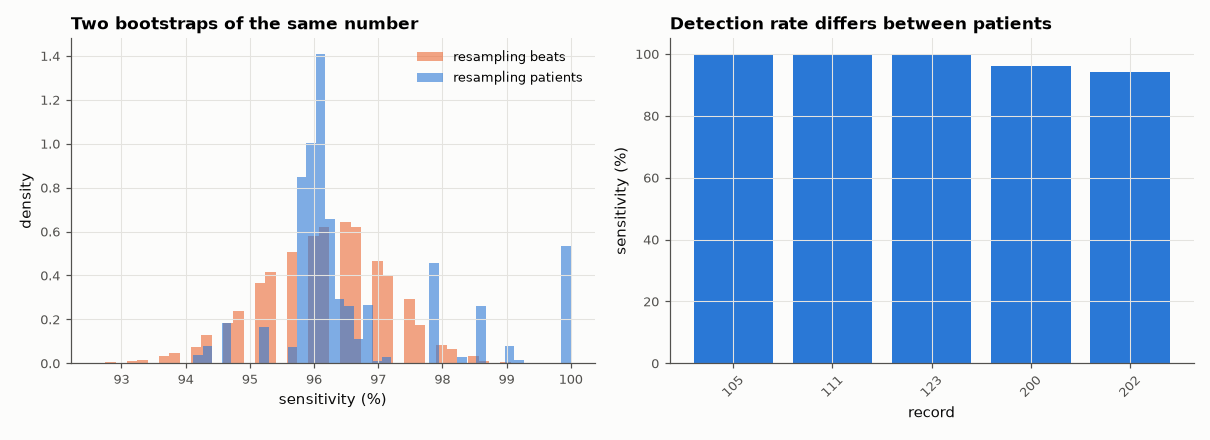
projects/applied-math/J-statistics-and-learning-on-real-signals/AM187-bootstrap-confidence-intervals/figures/bootstrap.png
