nyquist-labs/projects/projects/applied-math/J-statistics-and-learning-on-real-signals/AM188-simulated-emg-cursor-control/figures/cursor.png

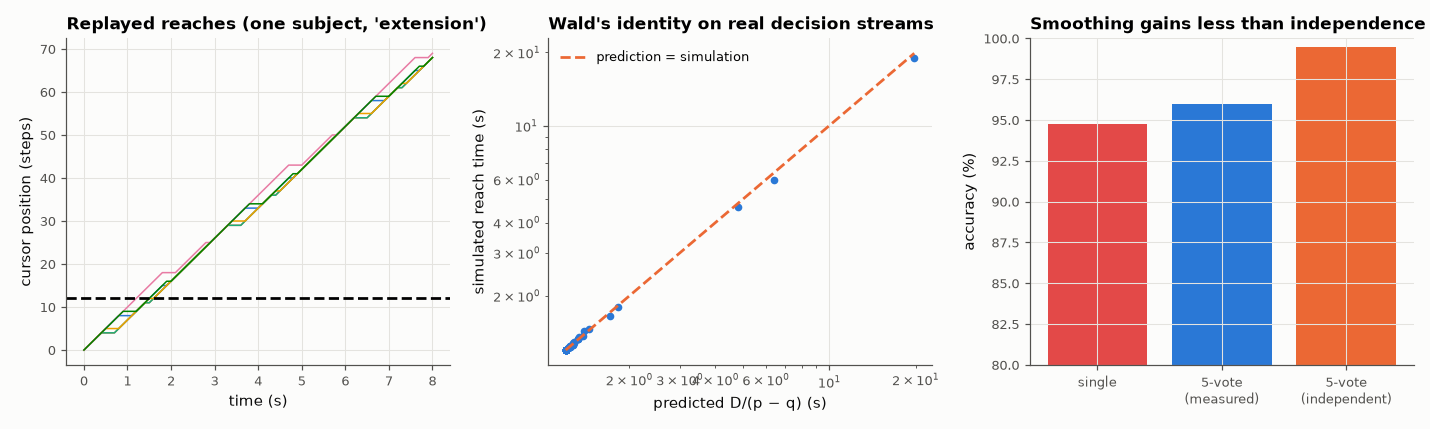
projects/applied-math/J-statistics-and-learning-on-real-signals/AM188-simulated-emg-cursor-control/figures/cursor.png
