nyquist-labs/projects/projects/applied-math/K-fields-vector-calculus-and-geometry/AM189-numerical-field-solver-gauss-law/figures/gauss.png

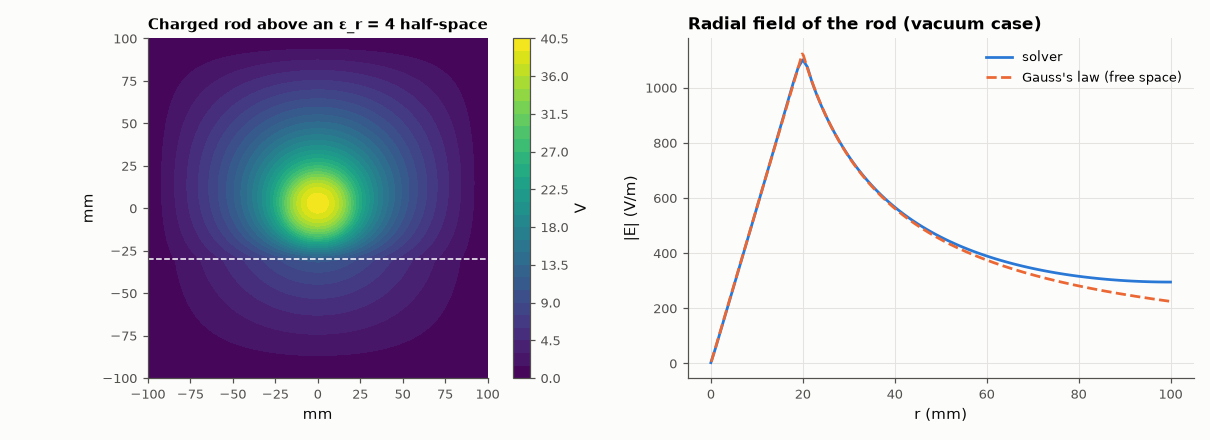
projects/applied-math/K-fields-vector-calculus-and-geometry/AM189-numerical-field-solver-gauss-law/figures/gauss.png
