nyquist-labs/projects/projects/applied-math/K-fields-vector-calculus-and-geometry/AM190-laplace-relaxation-methods/figures/relaxation.png

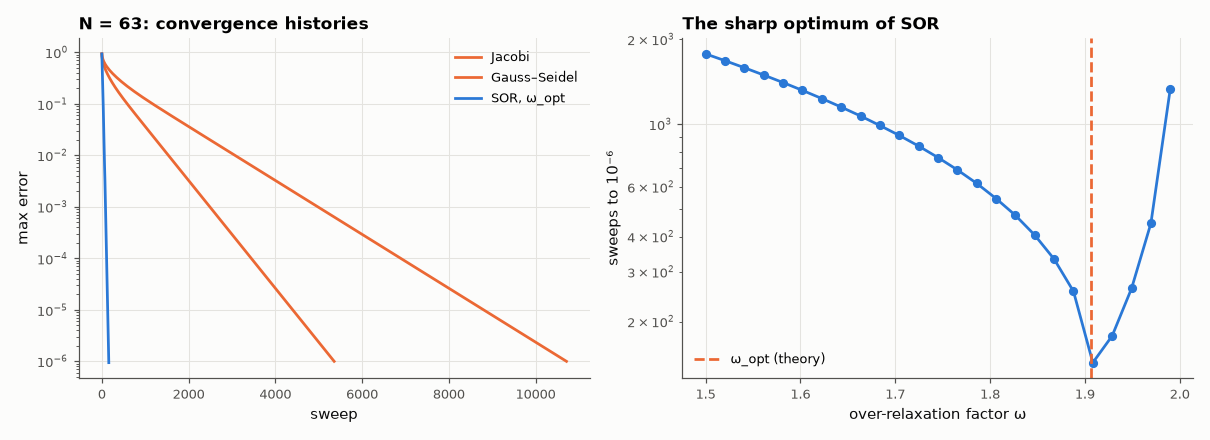
projects/applied-math/K-fields-vector-calculus-and-geometry/AM190-laplace-relaxation-methods/figures/relaxation.png
