nyquist-labs/projects/projects/applied-math/K-fields-vector-calculus-and-geometry/AM191-biot-savart-integration/figures/biot_savart.png

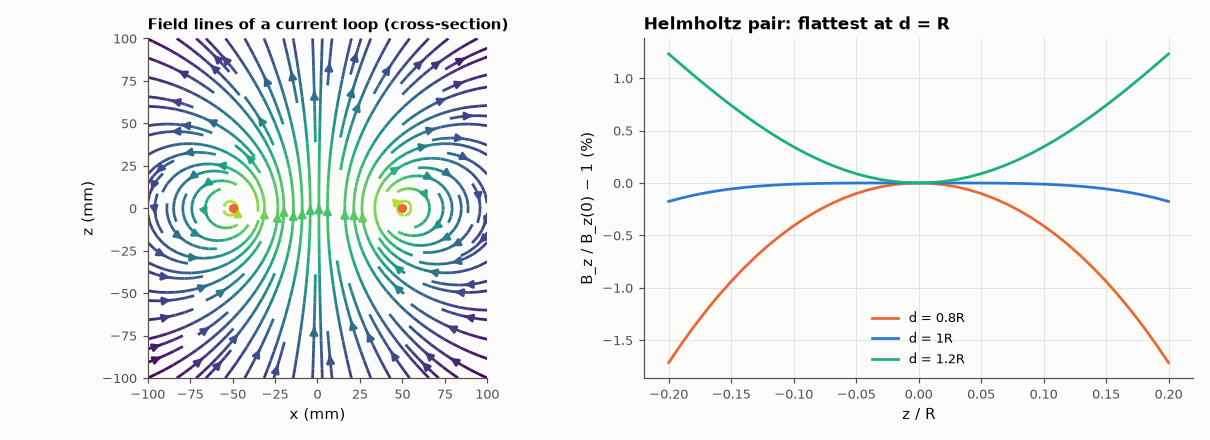
projects/applied-math/K-fields-vector-calculus-and-geometry/AM191-biot-savart-integration/figures/biot_savart.png
