nyquist-labs/projects/projects/applied-math/K-fields-vector-calculus-and-geometry/AM192-vector-calculus-visualiser/figures/vector_fields.png

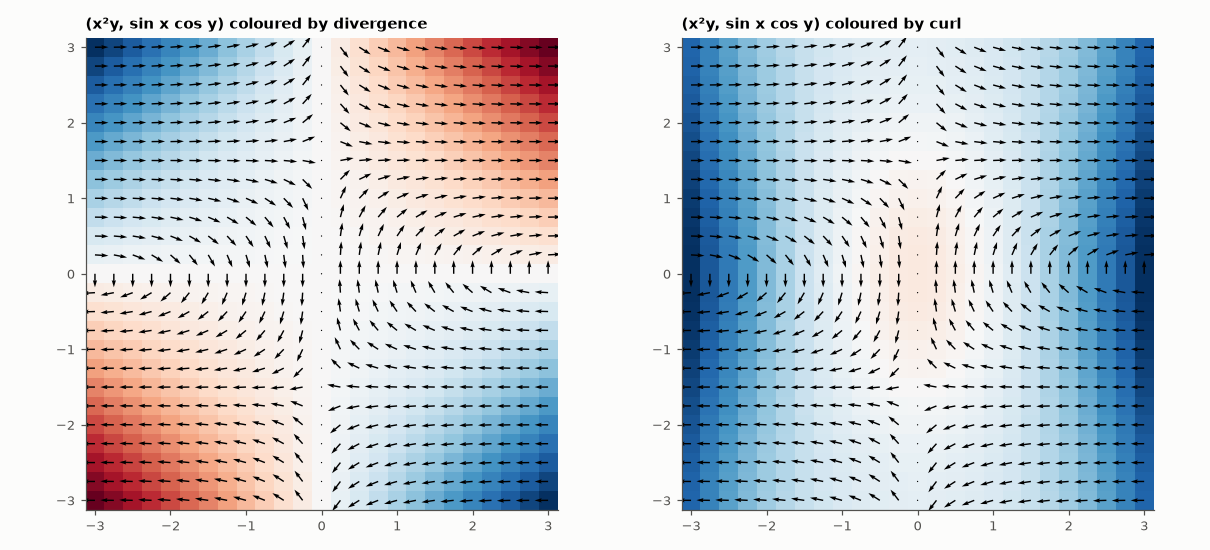
projects/applied-math/K-fields-vector-calculus-and-geometry/AM192-vector-calculus-visualiser/figures/vector_fields.png
