nyquist-labs/projects/projects/applied-math/K-fields-vector-calculus-and-geometry/AM193-maxwell-equations-demo/figures/maxwell2d.png

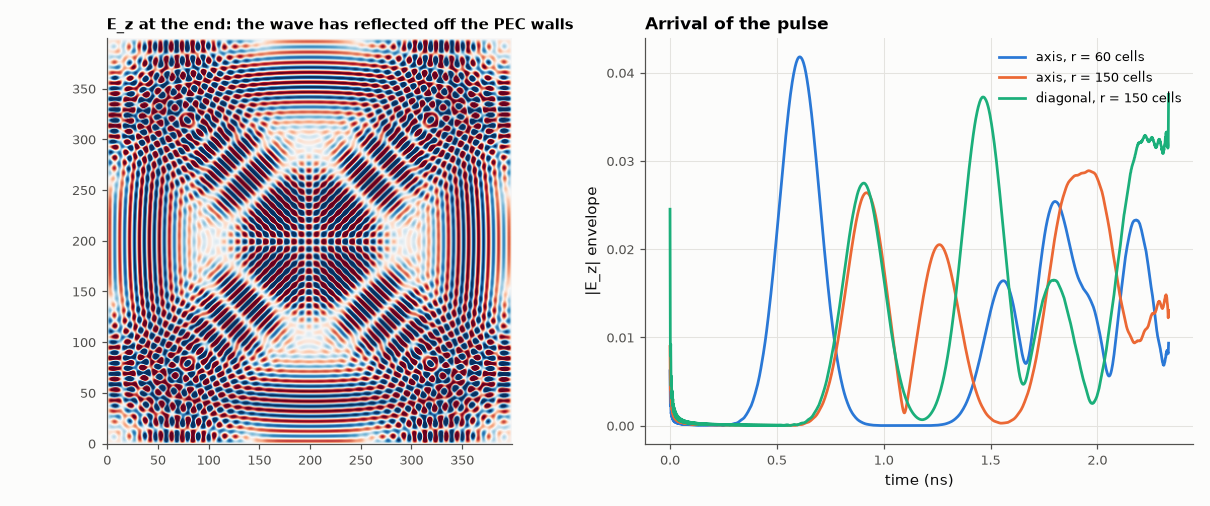
projects/applied-math/K-fields-vector-calculus-and-geometry/AM193-maxwell-equations-demo/figures/maxwell2d.png
