nyquist-labs/projects/projects/applied-math/K-fields-vector-calculus-and-geometry/AM194-poynting-vector-energy-flow/figures/poynting.png

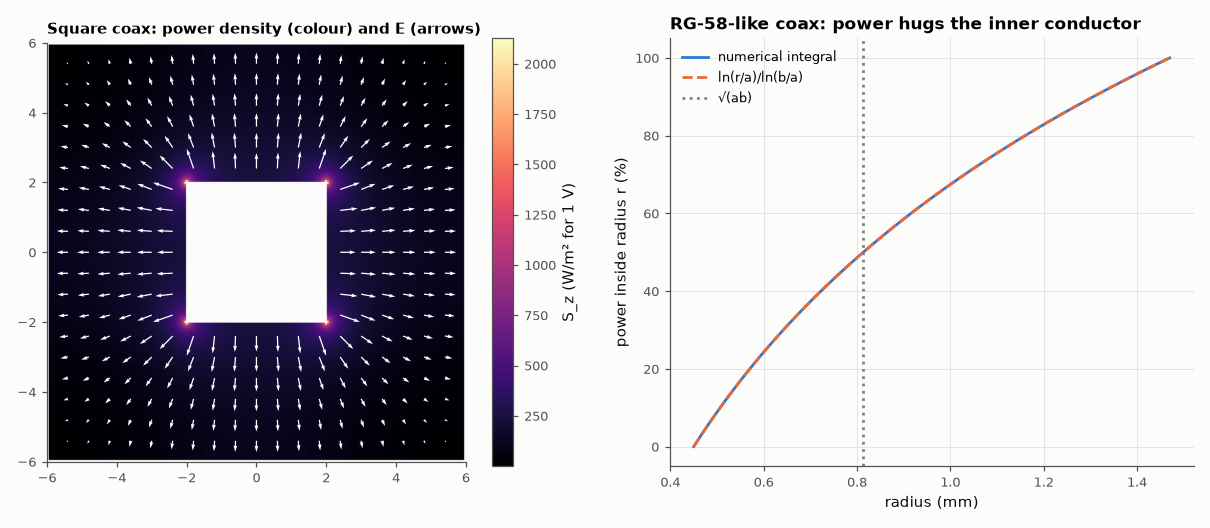
projects/applied-math/K-fields-vector-calculus-and-geometry/AM194-poynting-vector-energy-flow/figures/poynting.png
