nyquist-labs/projects/projects/applied-math/K-fields-vector-calculus-and-geometry/AM197-array-factor-and-pattern-multiplication/figures/arrays.png

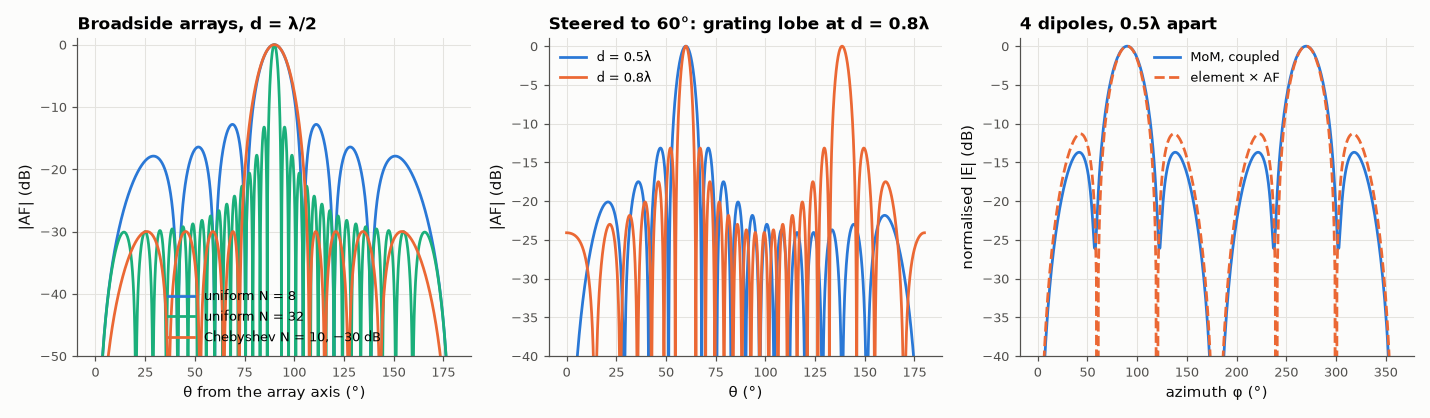
projects/applied-math/K-fields-vector-calculus-and-geometry/AM197-array-factor-and-pattern-multiplication/figures/arrays.png
