nyquist-labs/projects/projects/applied-math/K-fields-vector-calculus-and-geometry/AM199-greens-functions/figures/greens.png

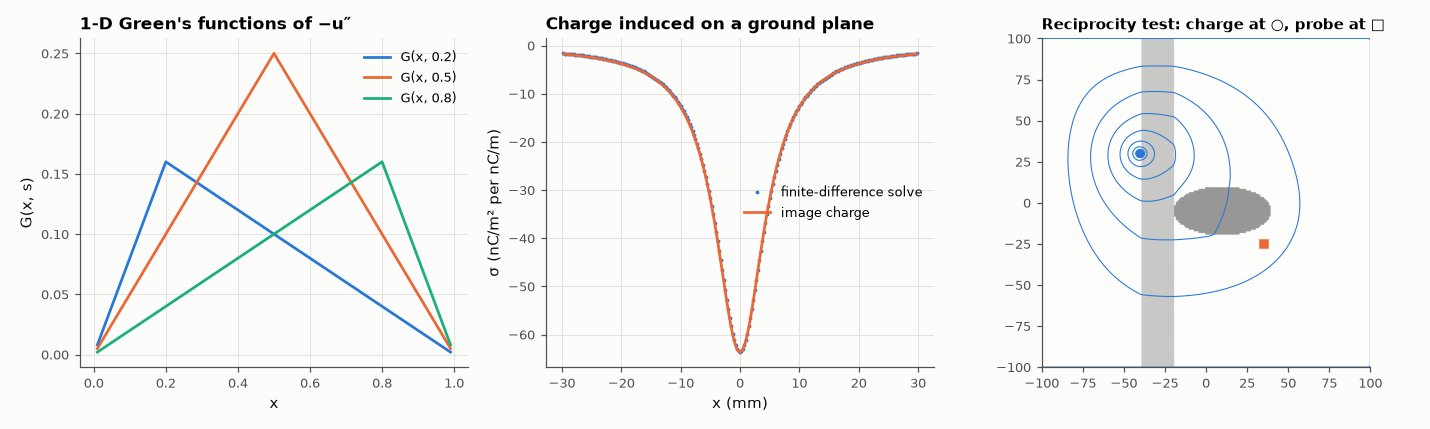
projects/applied-math/K-fields-vector-calculus-and-geometry/AM199-greens-functions/figures/greens.png
