nyquist-labs/projects/projects/applied-math/K-fields-vector-calculus-and-geometry/AM201-skin-depth-derivation/figures/skin_depth.png

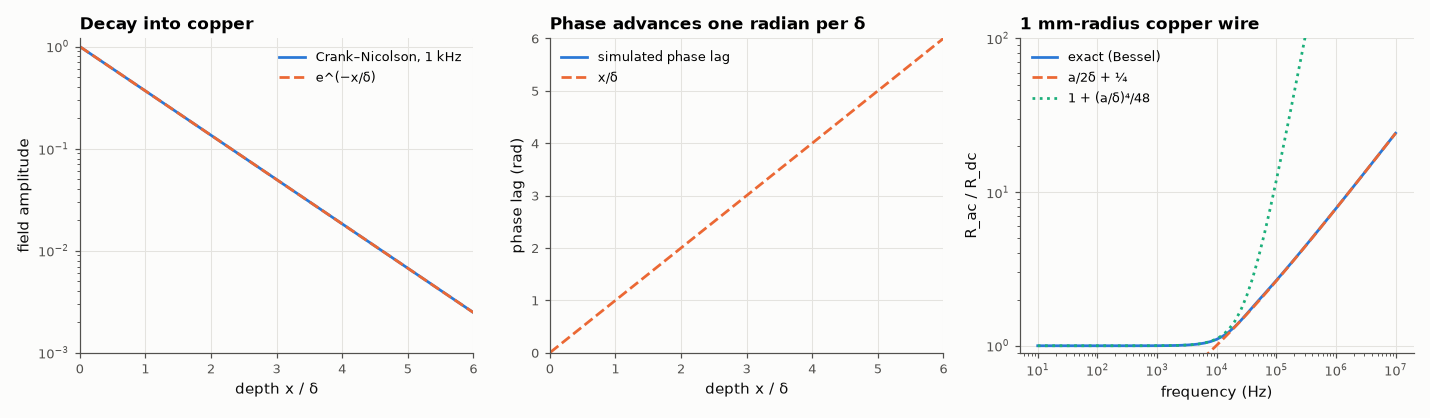
projects/applied-math/K-fields-vector-calculus-and-geometry/AM201-skin-depth-derivation/figures/skin_depth.png
