nyquist-labs/projects/projects/applied-math/K-fields-vector-calculus-and-geometry/AM202-distributed-vs-lumped-models/figures/lumped.png

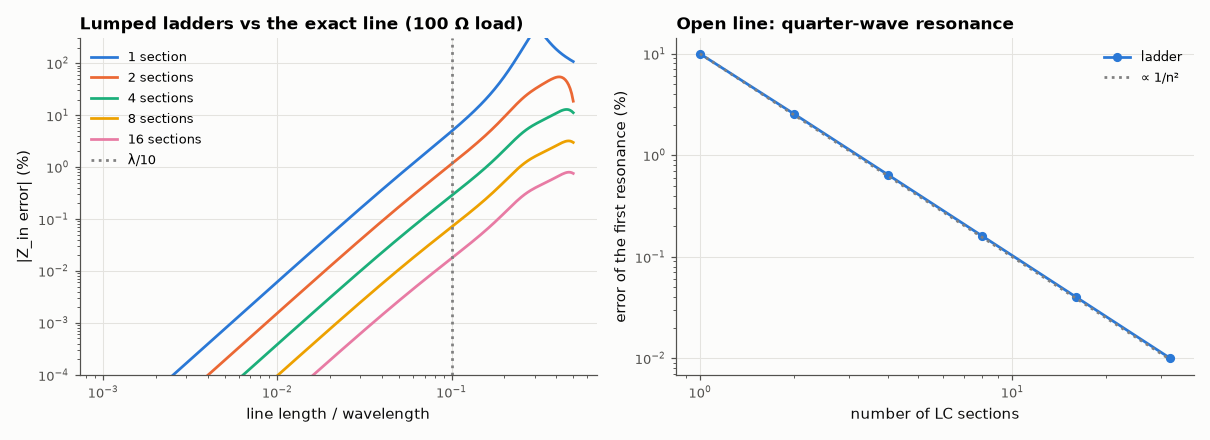
projects/applied-math/K-fields-vector-calculus-and-geometry/AM202-distributed-vs-lumped-models/figures/lumped.png
