nyquist-labs/projects/projects/applied-math/K-fields-vector-calculus-and-geometry/AM203-coordinate-transformations/figures/coordinates.png

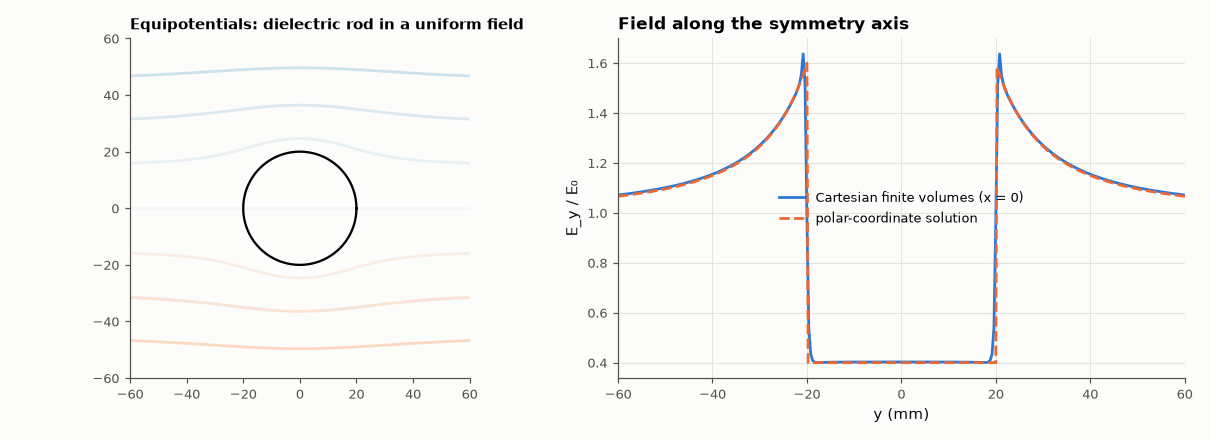
projects/applied-math/K-fields-vector-calculus-and-geometry/AM203-coordinate-transformations/figures/coordinates.png
