nyquist-labs/projects/projects/signal-lab/C-digital-logic-and-hdl/SL038-full-adder/figures/timing.png

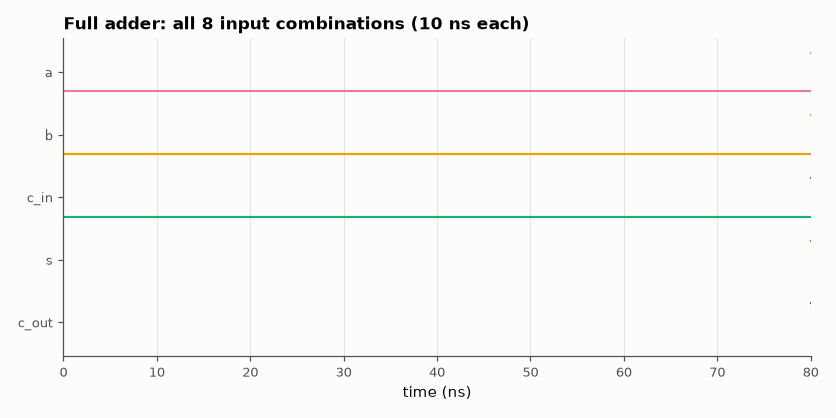
projects/signal-lab/C-digital-logic-and-hdl/SL038-full-adder/figures/timing.png
