nyquist-labs/projects/projects/signal-lab/C-digital-logic-and-hdl/SL041-8bit-alu/figures/synthesis.png

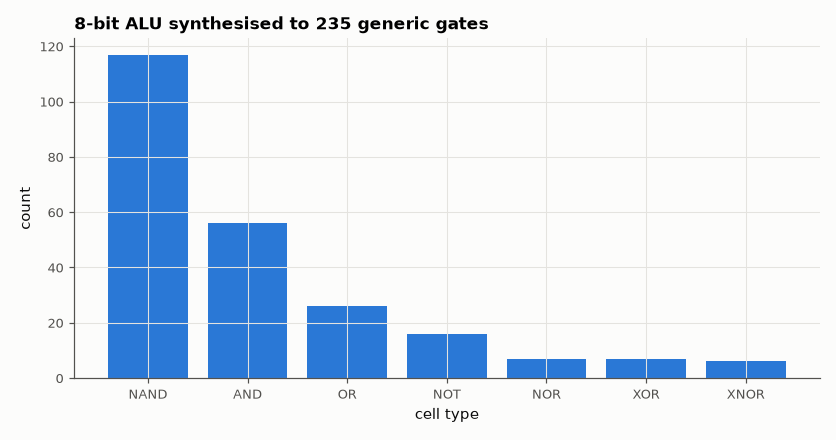
projects/signal-lab/C-digital-logic-and-hdl/SL041-8bit-alu/figures/synthesis.png
