nyquist-labs/projects/projects/signal-lab/C-digital-logic-and-hdl/SL043-traffic-light-fsm/figures/timing.png

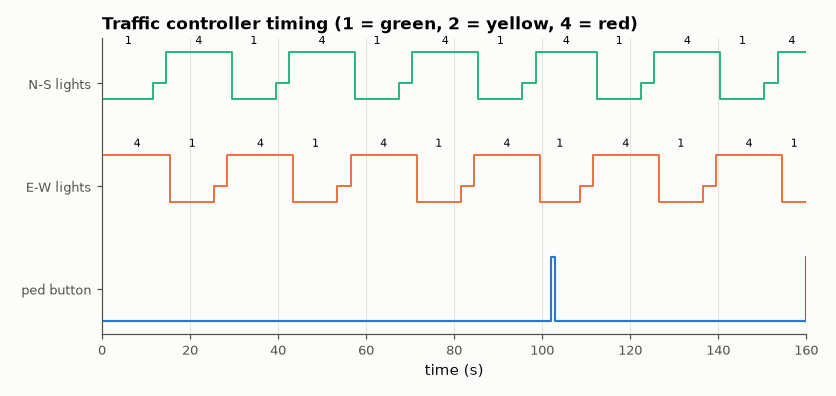
projects/signal-lab/C-digital-logic-and-hdl/SL043-traffic-light-fsm/figures/timing.png
