nyquist-labs/projects/projects/signal-lab/C-digital-logic-and-hdl/SL045-uart-transmitter/figures/frames.png

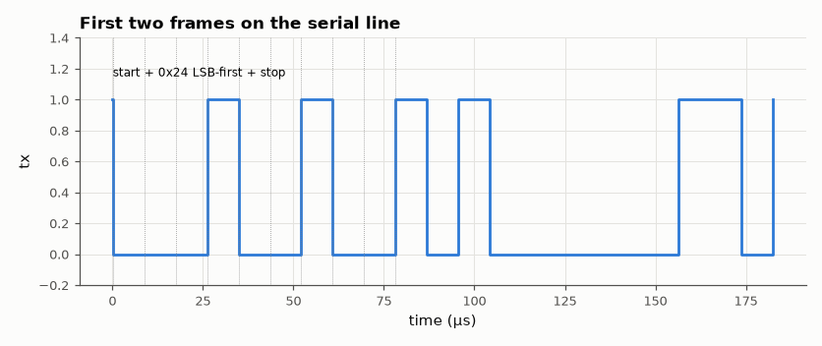
projects/signal-lab/C-digital-logic-and-hdl/SL045-uart-transmitter/figures/frames.png
