nyquist-labs/projects/projects/signal-lab/C-digital-logic-and-hdl/SL046-uart-receiver/figures/tolerance.png

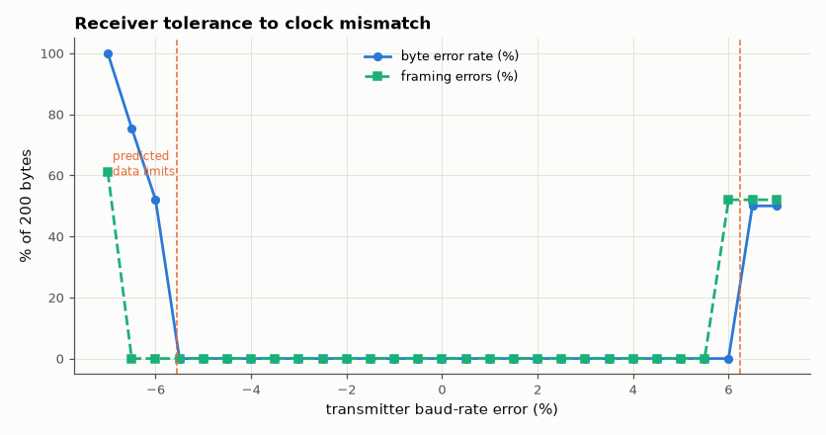
projects/signal-lab/C-digital-logic-and-hdl/SL046-uart-receiver/figures/tolerance.png
