nyquist-labs/projects/projects/signal-lab/C-digital-logic-and-hdl/SL047-spi-master/figures/timing.png

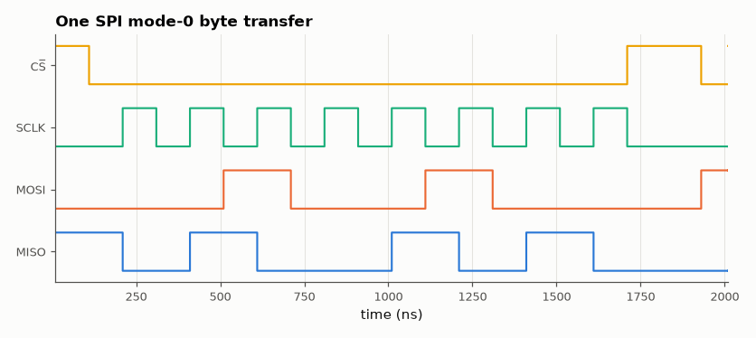
projects/signal-lab/C-digital-logic-and-hdl/SL047-spi-master/figures/timing.png
