nyquist-labs/projects/projects/signal-lab/C-digital-logic-and-hdl/SL050-switch-debouncer/figures/timing.png

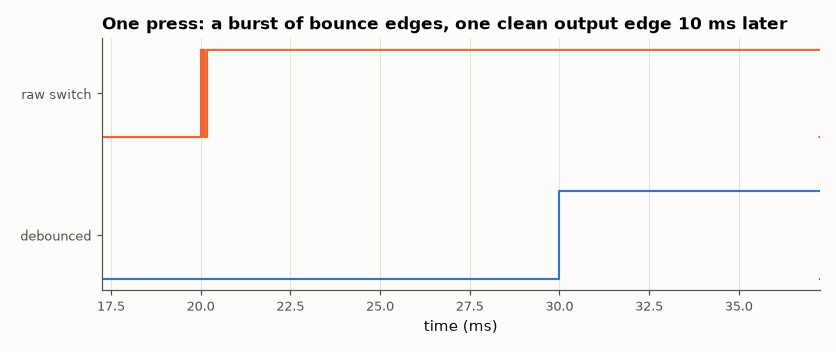
projects/signal-lab/C-digital-logic-and-hdl/SL050-switch-debouncer/figures/timing.png
