nyquist-labs/projects/projects/signal-lab/C-digital-logic-and-hdl/SL051-seven-segment-driver/figures/decoder.png

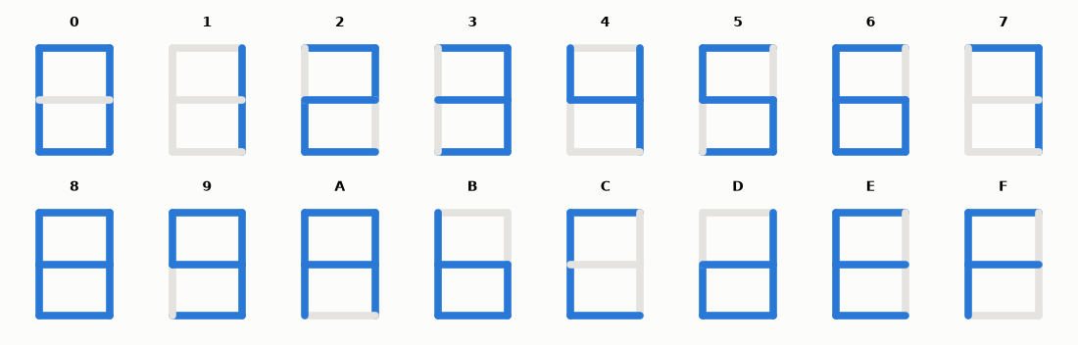
projects/signal-lab/C-digital-logic-and-hdl/SL051-seven-segment-driver/figures/decoder.png
