nyquist-labs/projects/projects/signal-lab/C-digital-logic-and-hdl/SL054-async-fifo-cdc/figures/gray_vs_binary.png

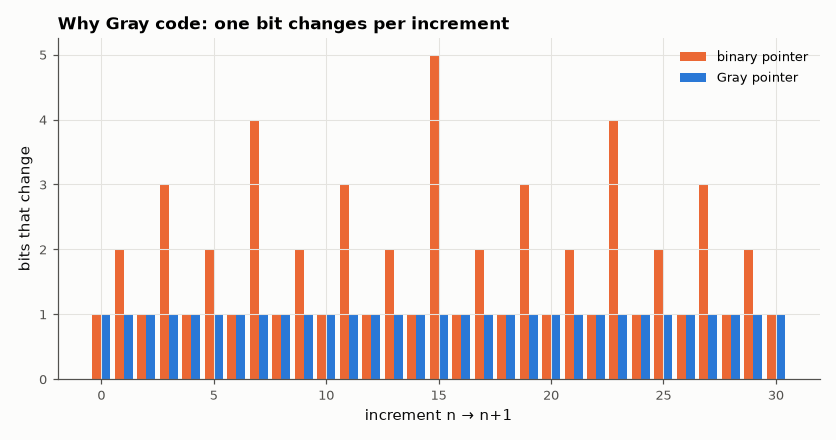
projects/signal-lab/C-digital-logic-and-hdl/SL054-async-fifo-cdc/figures/gray_vs_binary.png
