nyquist-labs/projects/projects/signal-lab/C-digital-logic-and-hdl/SL055-single-cycle-risc-cpu/figures/cycles.png

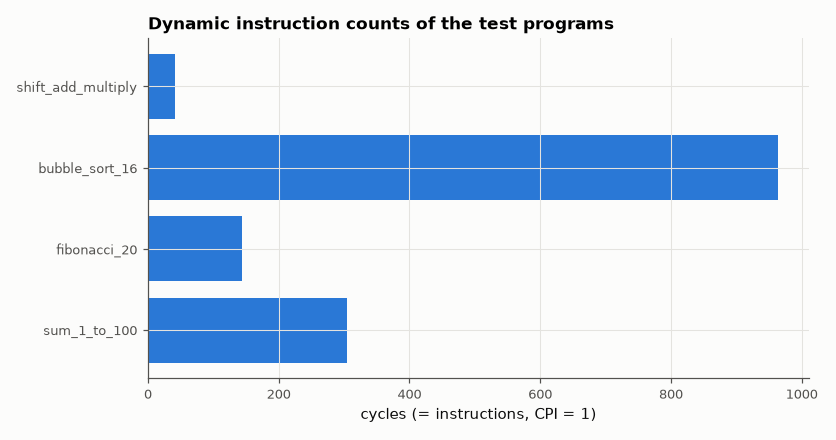
projects/signal-lab/C-digital-logic-and-hdl/SL055-single-cycle-risc-cpu/figures/cycles.png
