nyquist-labs/projects/projects/signal-lab/D-digital-signal-processing/SL061-window-function-comparison/figures/weak_tone.png

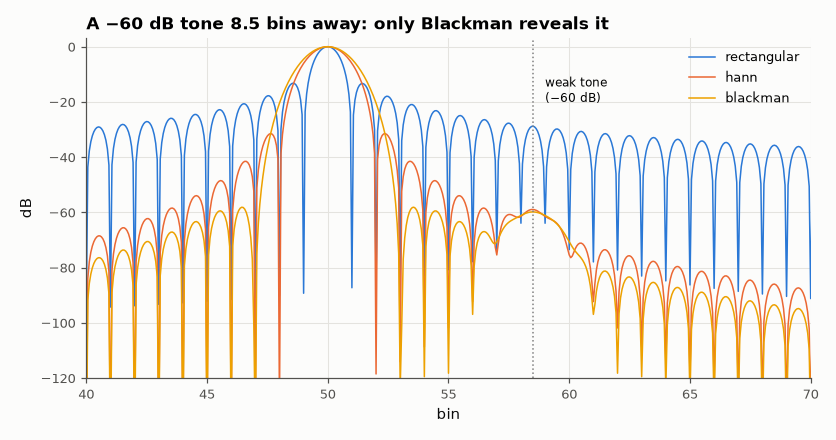
projects/signal-lab/D-digital-signal-processing/SL061-window-function-comparison/figures/weak_tone.png
