nyquist-labs/projects/projects/signal-lab/D-digital-signal-processing/SL065-audio-equaliser/figures/eq_response.png

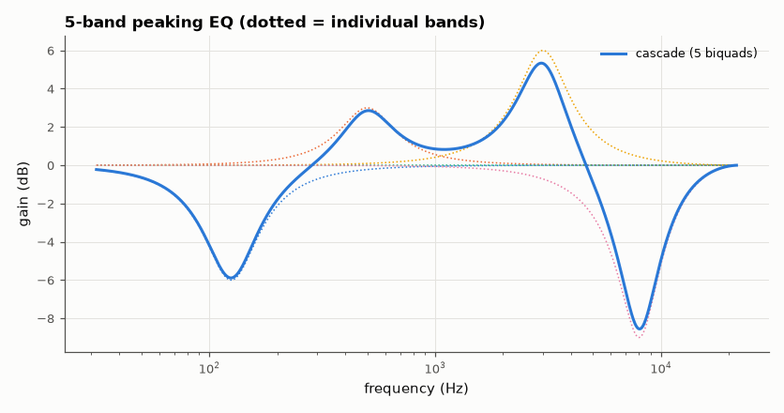
projects/signal-lab/D-digital-signal-processing/SL065-audio-equaliser/figures/eq_response.png
