nyquist-labs/projects/projects/signal-lab/D-digital-signal-processing/SL065-audio-equaliser/figures/speech_spectra.png

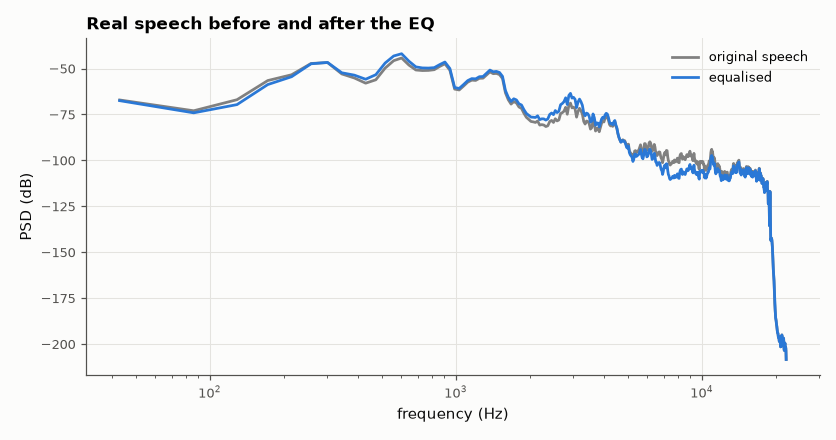
projects/signal-lab/D-digital-signal-processing/SL065-audio-equaliser/figures/speech_spectra.png
