nyquist-labs/projects/projects/signal-lab/D-digital-signal-processing/SL066-audio-noise-removal/figures/snr_gain.png

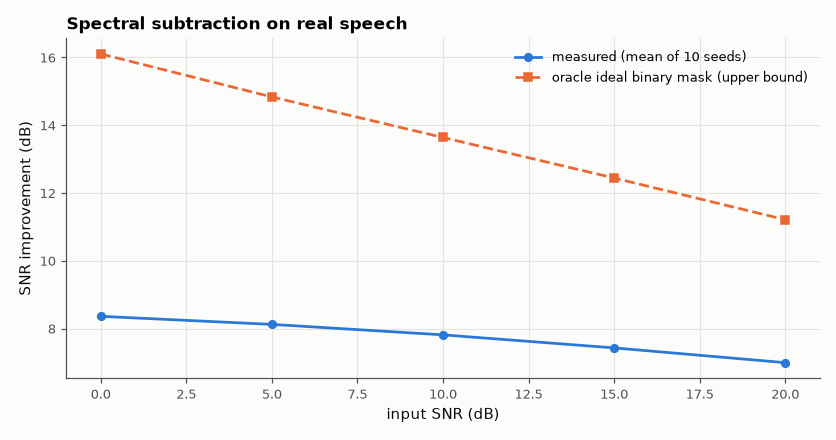
projects/signal-lab/D-digital-signal-processing/SL066-audio-noise-removal/figures/snr_gain.png
