nyquist-labs/projects/projects/signal-lab/D-digital-signal-processing/SL068-pitch-detection/figures/pitch.png

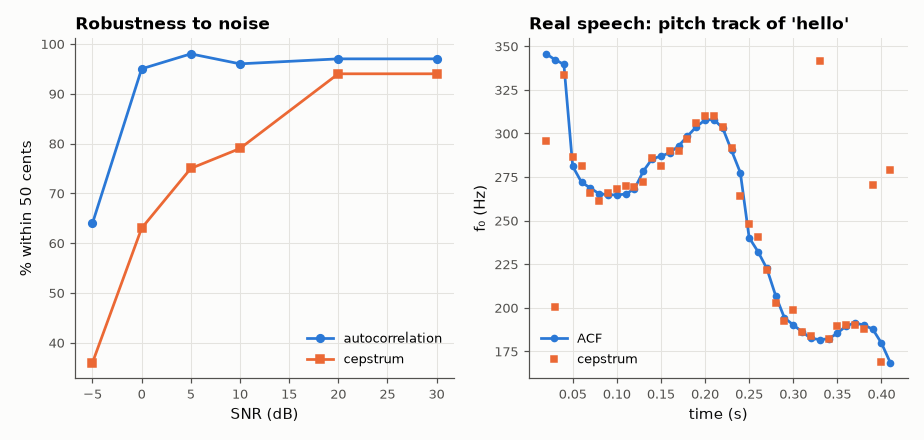
projects/signal-lab/D-digital-signal-processing/SL068-pitch-detection/figures/pitch.png
