nyquist-labs/projects/projects/signal-lab/D-digital-signal-processing/SL069-guitar-tuner/figures/accuracy.png

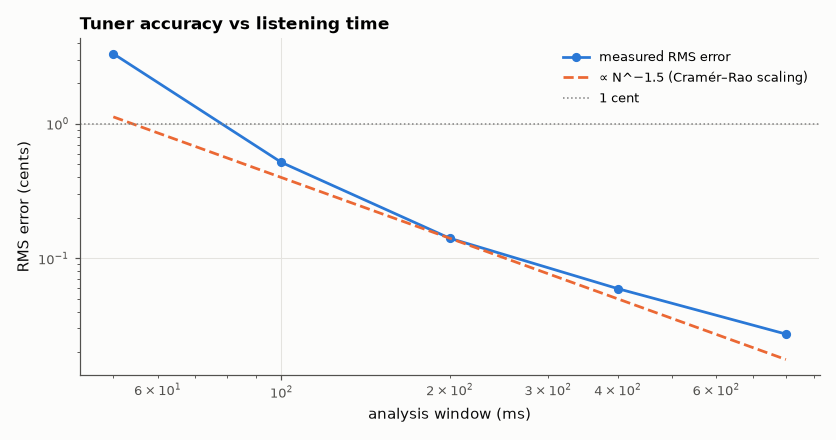
projects/signal-lab/D-digital-signal-processing/SL069-guitar-tuner/figures/accuracy.png
