nyquist-labs/projects/projects/signal-lab/D-digital-signal-processing/SL070-dtmf-decoder/figures/error_rate.png

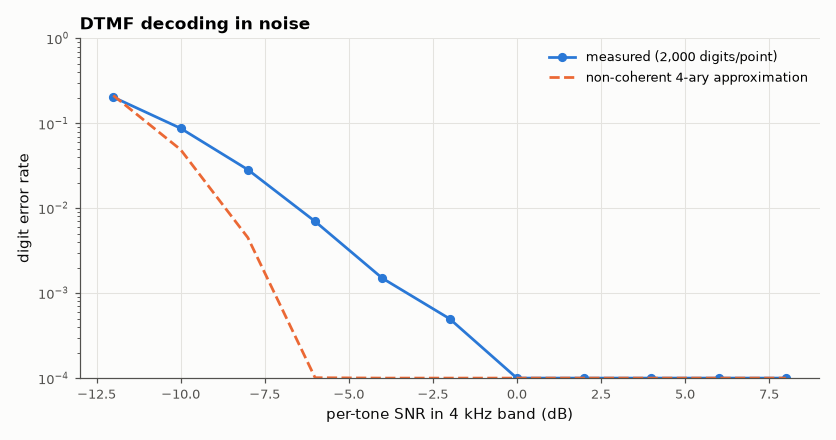
projects/signal-lab/D-digital-signal-processing/SL070-dtmf-decoder/figures/error_rate.png
