nyquist-labs/projects/projects/signal-lab/D-digital-signal-processing/SL071-morse-code-decoder/figures/cer_vs_snr.png

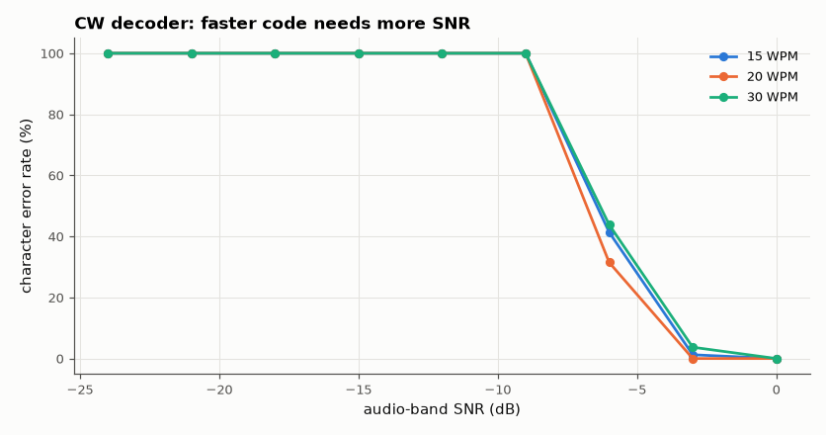
projects/signal-lab/D-digital-signal-processing/SL071-morse-code-decoder/figures/cer_vs_snr.png
