nyquist-labs/projects/projects/signal-lab/D-digital-signal-processing/SL072-echo-and-reverb/figures/speech_reverb.png

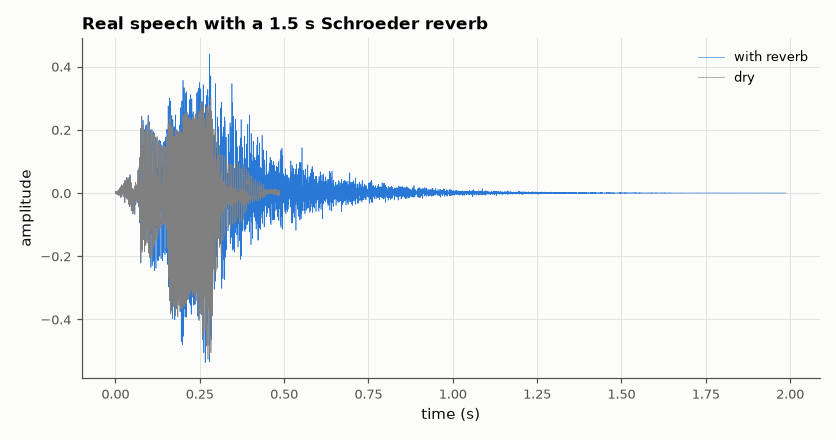
projects/signal-lab/D-digital-signal-processing/SL072-echo-and-reverb/figures/speech_reverb.png
