nyquist-labs/projects/projects/signal-lab/D-digital-signal-processing/SL074-aliasing-demonstrator/figures/aliasing.png

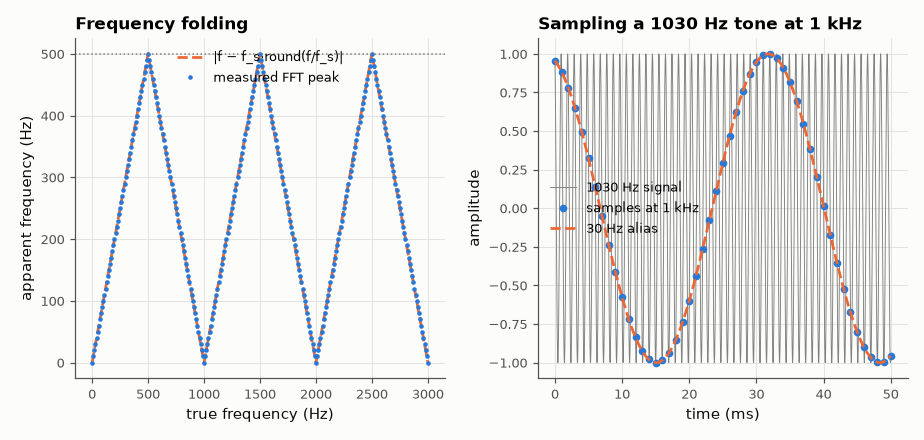
projects/signal-lab/D-digital-signal-processing/SL074-aliasing-demonstrator/figures/aliasing.png
