nyquist-labs/projects/projects/signal-lab/D-digital-signal-processing/SL075-quantisation-noise-study/figures/error_spectrum.png

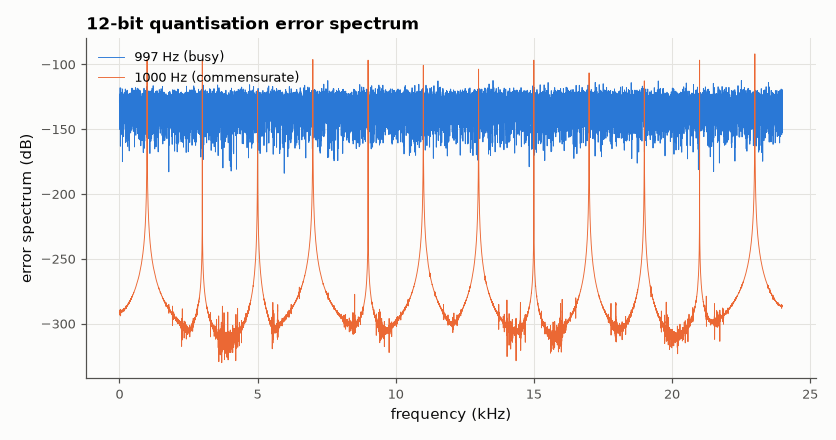
projects/signal-lab/D-digital-signal-processing/SL075-quantisation-noise-study/figures/error_spectrum.png
