nyquist-labs/projects/projects/signal-lab/D-digital-signal-processing/SL075-quantisation-noise-study/figures/snr_bits.png

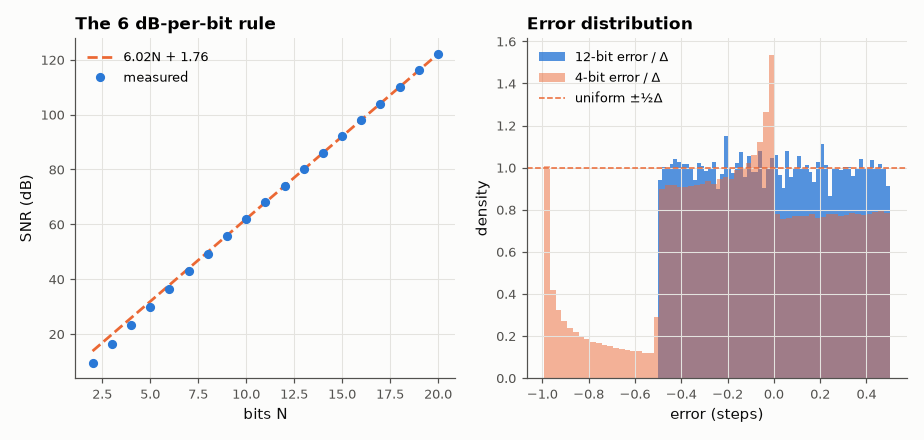
projects/signal-lab/D-digital-signal-processing/SL075-quantisation-noise-study/figures/snr_bits.png
