nyquist-labs/projects/projects/signal-lab/D-digital-signal-processing/SL076-dithering-demo/figures/spectra.png

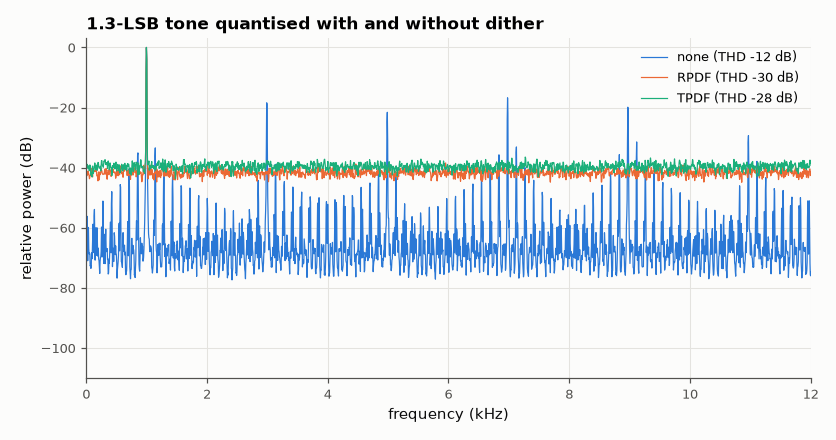
projects/signal-lab/D-digital-signal-processing/SL076-dithering-demo/figures/spectra.png
