nyquist-labs/projects/projects/signal-lab/D-digital-signal-processing/SL076-dithering-demo/figures/time_domain.png

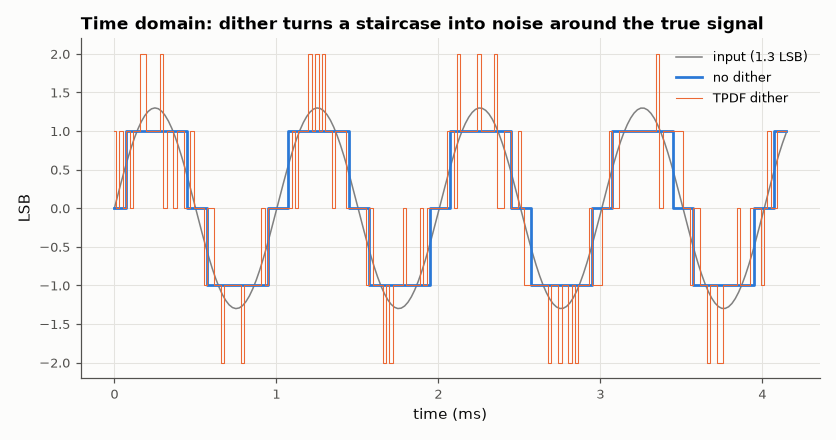
projects/signal-lab/D-digital-signal-processing/SL076-dithering-demo/figures/time_domain.png
