nyquist-labs/projects/projects/signal-lab/D-digital-signal-processing/SL081-beamforming-simulation/figures/patterns.png

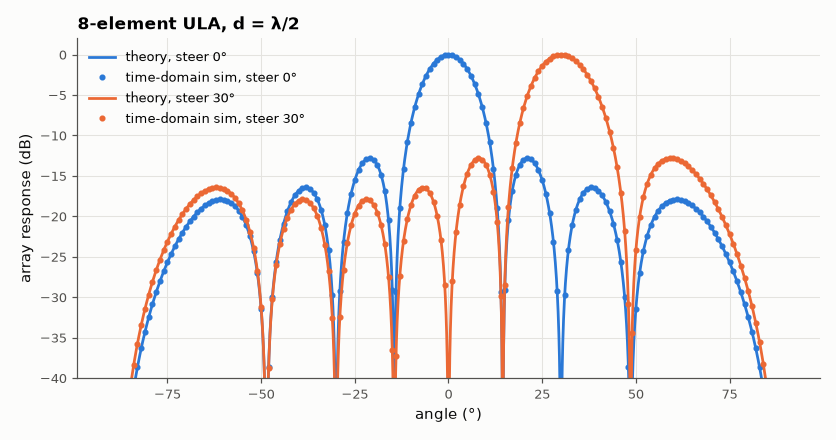
projects/signal-lab/D-digital-signal-processing/SL081-beamforming-simulation/figures/patterns.png
