nyquist-labs/projects/projects/signal-lab/D-digital-signal-processing/SL082-compressive-sensing/figures/compressive_sensing.png

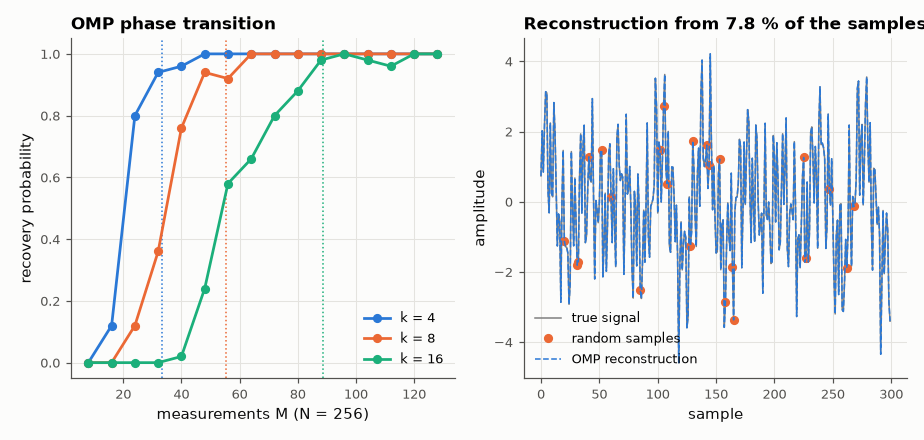
projects/signal-lab/D-digital-signal-processing/SL082-compressive-sensing/figures/compressive_sensing.png
