nyquist-labs/projects/projects/signal-lab/E-rf-radio-and-satellites/SL086-noaa-apt-image-decode/figures/sync_and_wedges.png

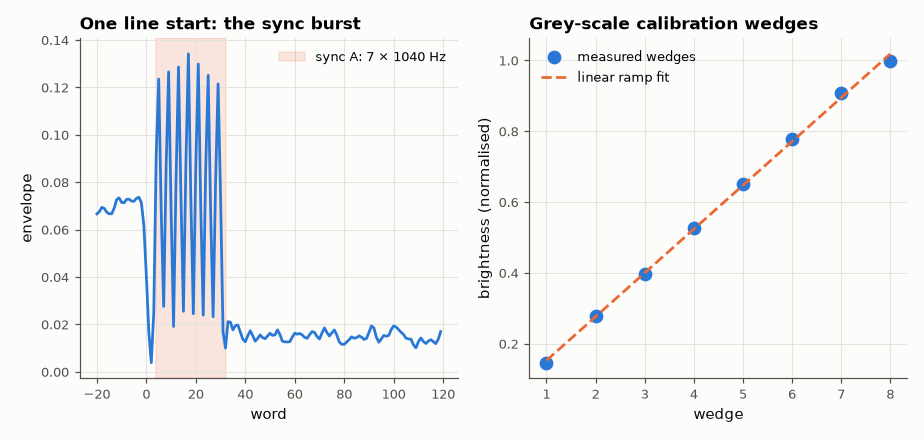
projects/signal-lab/E-rf-radio-and-satellites/SL086-noaa-apt-image-decode/figures/sync_and_wedges.png
