nyquist-labs/projects/projects/signal-lab/E-rf-radio-and-satellites/SL088-adsb-decode-from-iq/figures/messages.png

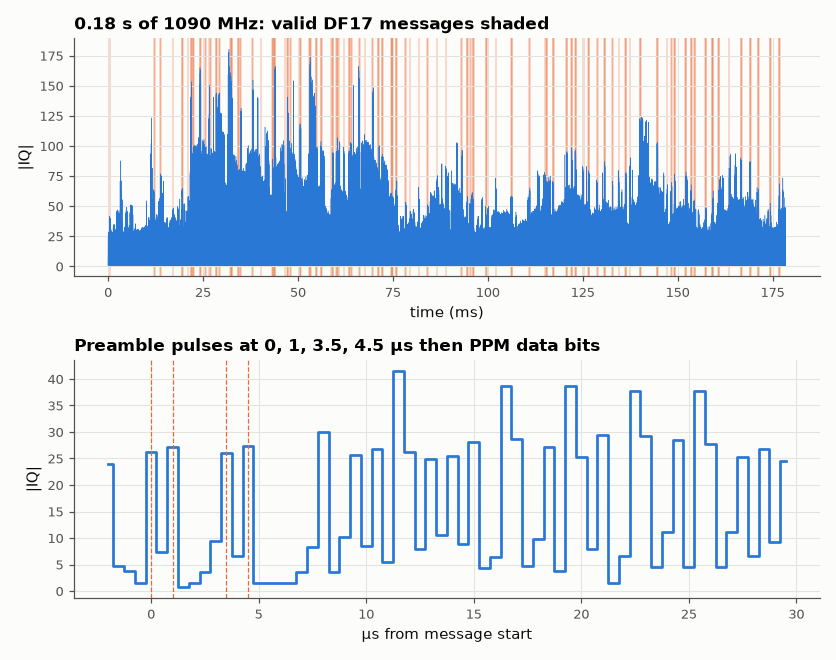
projects/signal-lab/E-rf-radio-and-satellites/SL088-adsb-decode-from-iq/figures/messages.png
