nyquist-labs/projects/projects/signal-lab/E-rf-radio-and-satellites/SL089-webSDR-propagation-study/figures/propagation.png

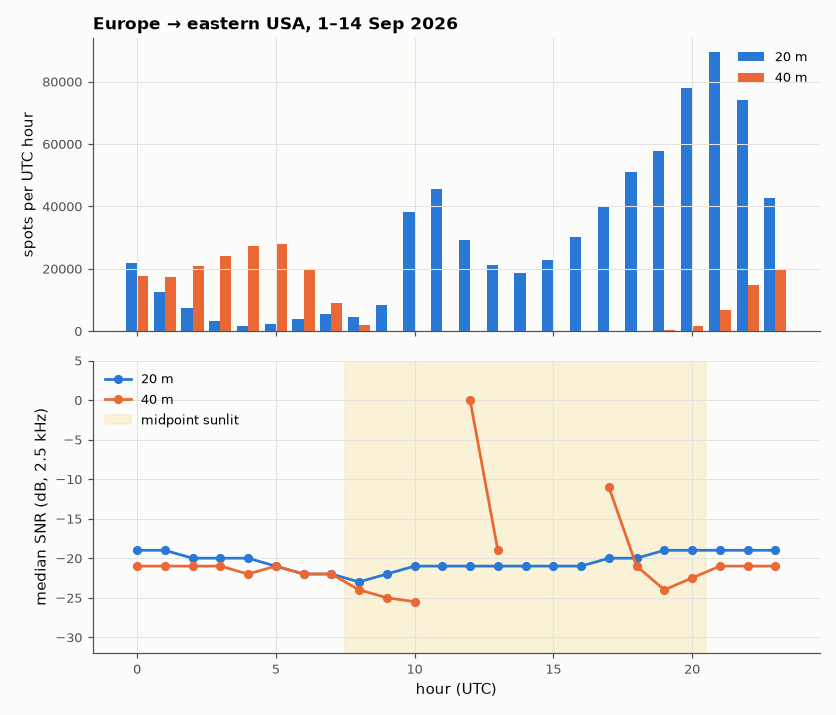
projects/signal-lab/E-rf-radio-and-satellites/SL089-webSDR-propagation-study/figures/propagation.png
