nyquist-labs/projects/projects/signal-lab/E-rf-radio-and-satellites/SL091-fm-demodulation-from-iq/figures/fm_snr.png

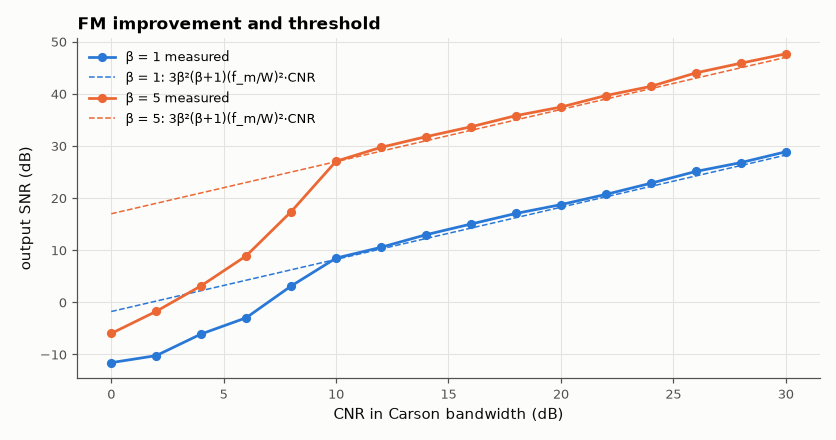
projects/signal-lab/E-rf-radio-and-satellites/SL091-fm-demodulation-from-iq/figures/fm_snr.png
