nyquist-labs/projects/projects/signal-lab/E-rf-radio-and-satellites/SL092-ssb-demodulation/figures/ssb.png

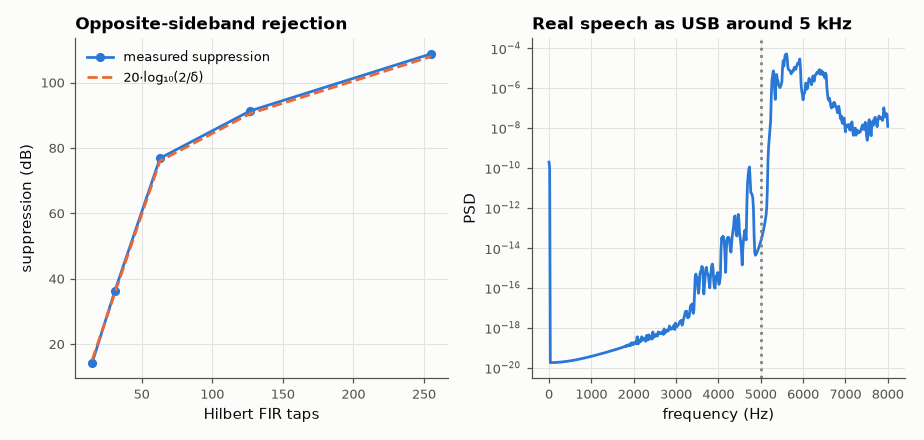
projects/signal-lab/E-rf-radio-and-satellites/SL092-ssb-demodulation/figures/ssb.png
