nyquist-labs/projects/projects/signal-lab/E-rf-radio-and-satellites/SL093-rtty-fsk-decoder/figures/ber.png

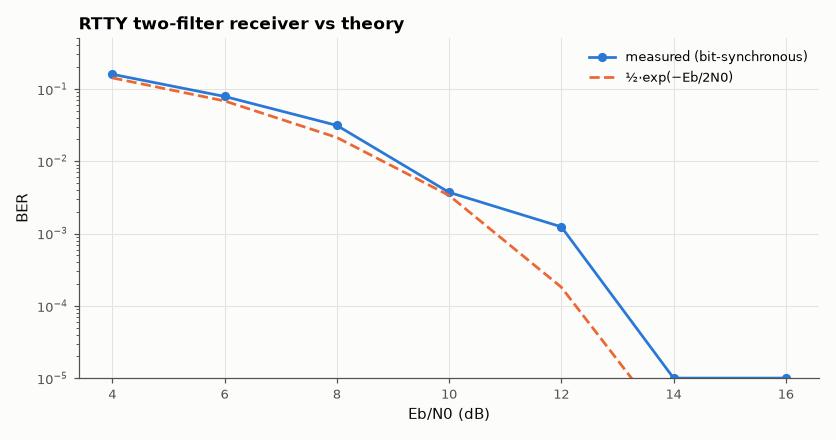
projects/signal-lab/E-rf-radio-and-satellites/SL093-rtty-fsk-decoder/figures/ber.png
