nyquist-labs/projects/projects/signal-lab/E-rf-radio-and-satellites/SL094-wspr-spot-analysis/figures/distance_by_band.png

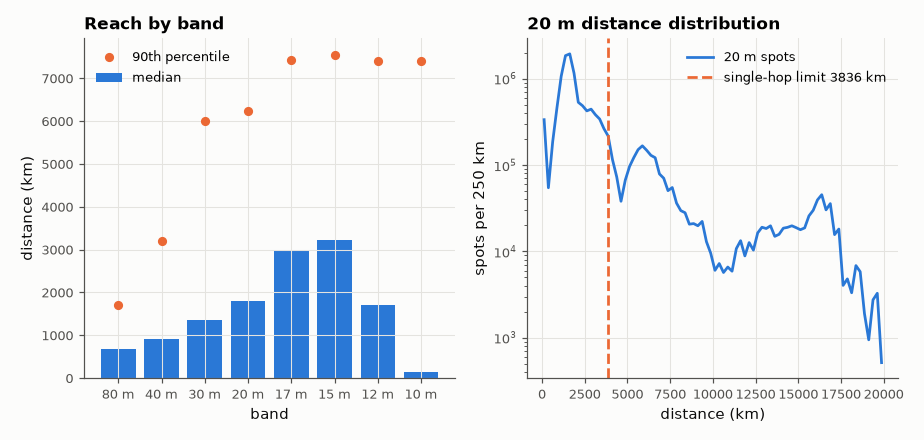
projects/signal-lab/E-rf-radio-and-satellites/SL094-wspr-spot-analysis/figures/distance_by_band.png
