nyquist-labs/projects/projects/signal-lab/E-rf-radio-and-satellites/SL098-link-budget-calculator/figures/budget_vs_pass.png

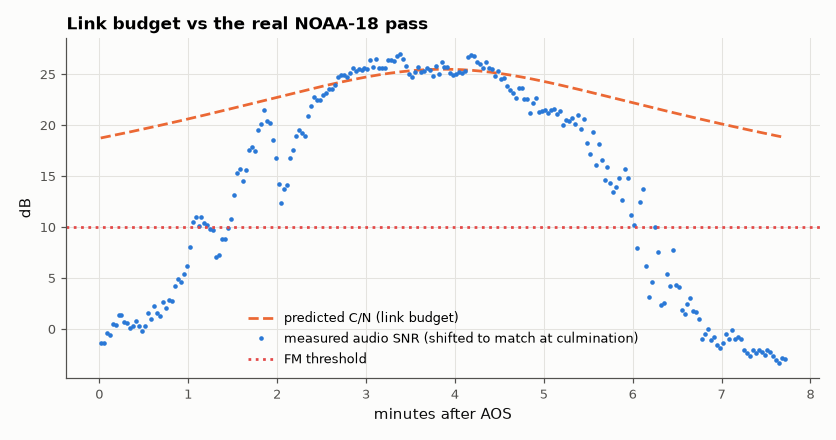
projects/signal-lab/E-rf-radio-and-satellites/SL098-link-budget-calculator/figures/budget_vs_pass.png
