nyquist-labs/projects/projects/signal-lab/E-rf-radio-and-satellites/SL099-antenna-pattern-simulator/figures/dipole.png

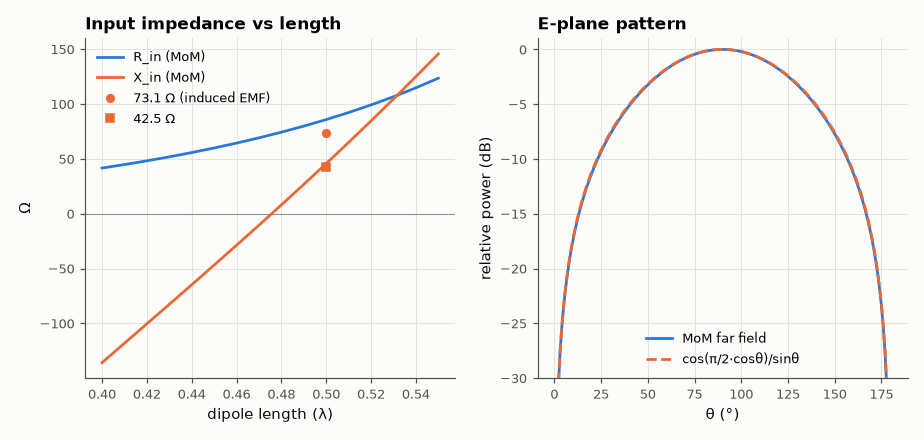
projects/signal-lab/E-rf-radio-and-satellites/SL099-antenna-pattern-simulator/figures/dipole.png
