nyquist-labs/projects/projects/signal-lab/E-rf-radio-and-satellites/SL104-noise-figure-cascade/figures/cascade.png

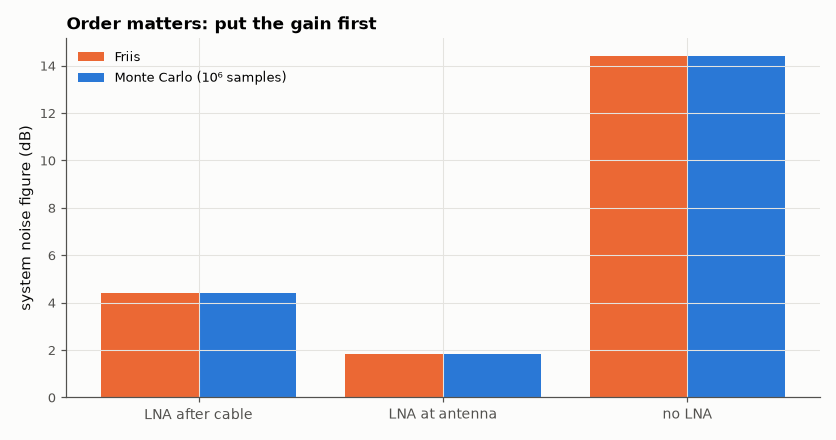
projects/signal-lab/E-rf-radio-and-satellites/SL104-noise-figure-cascade/figures/cascade.png
