nyquist-labs/projects/projects/signal-lab/F-communication-systems/SL108-bpsk-ber-curve/figures/ber.png

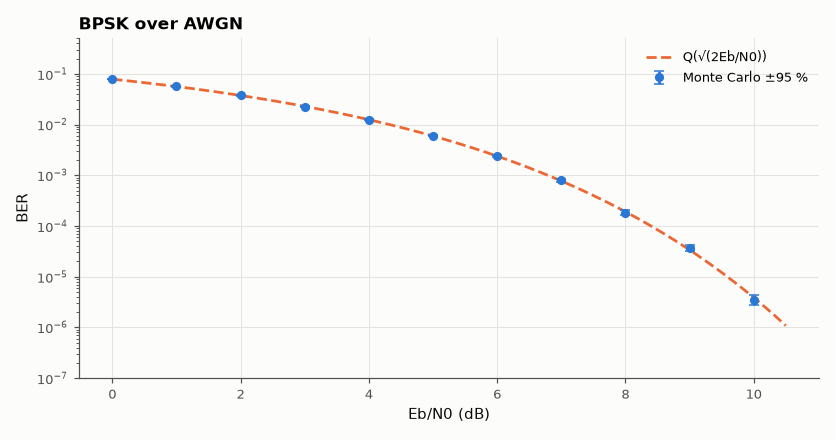
projects/signal-lab/F-communication-systems/SL108-bpsk-ber-curve/figures/ber.png
