nyquist-labs/projects/projects/signal-lab/F-communication-systems/SL109-qpsk-system/figures/qpsk.png

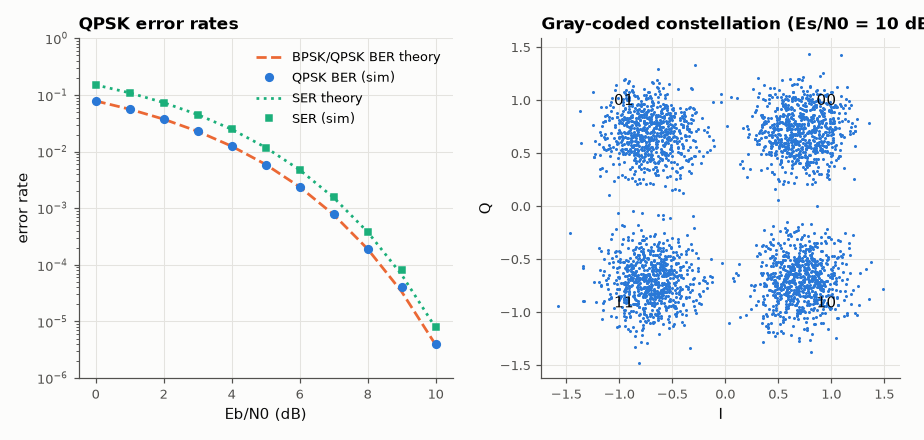
projects/signal-lab/F-communication-systems/SL109-qpsk-system/figures/qpsk.png
