nyquist-labs/projects/projects/signal-lab/F-communication-systems/SL114-reed-solomon-codes/figures/rs.png

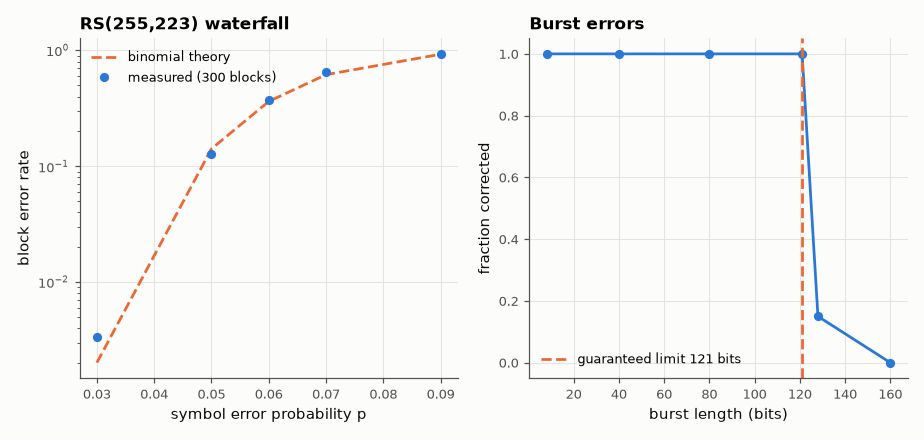
projects/signal-lab/F-communication-systems/SL114-reed-solomon-codes/figures/rs.png
