nyquist-labs/projects/projects/signal-lab/F-communication-systems/SL117-channel-models/figures/fading.png

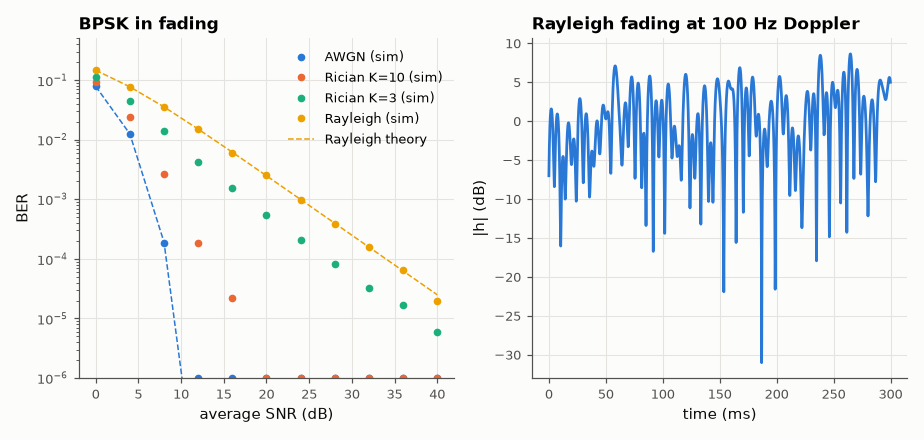
projects/signal-lab/F-communication-systems/SL117-channel-models/figures/fading.png
