nyquist-labs/projects/projects/signal-lab/F-communication-systems/SL121-synchronisation-recovery/figures/costas.png

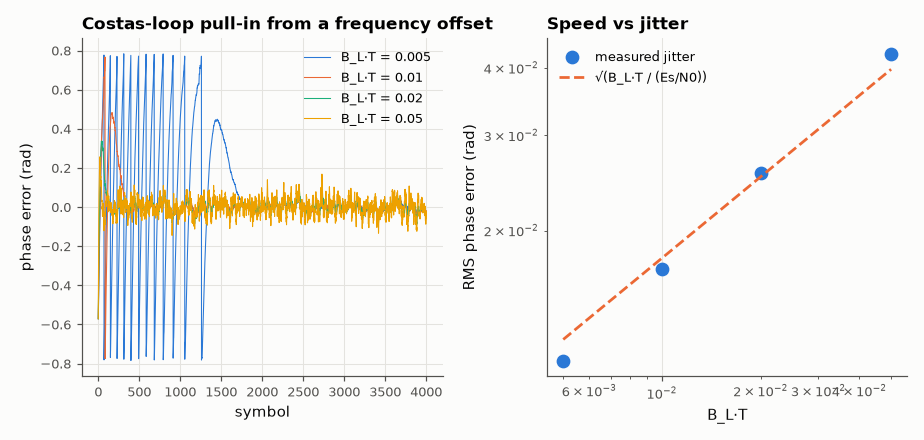
projects/signal-lab/F-communication-systems/SL121-synchronisation-recovery/figures/costas.png
