nyquist-labs/projects/projects/signal-lab/G-electromagnetics-and-device-physics/SL123-2d-fdtd-scattering/figures/slit.png

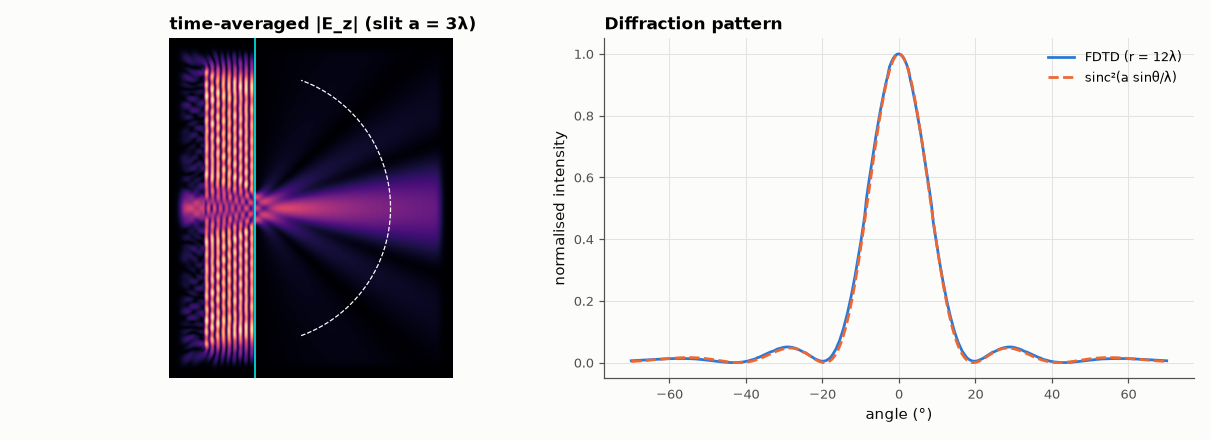
projects/signal-lab/G-electromagnetics-and-device-physics/SL123-2d-fdtd-scattering/figures/slit.png
