nyquist-labs/projects/projects/signal-lab/G-electromagnetics-and-device-physics/SL126-coaxial-cable-field-plot/figures/coax.png

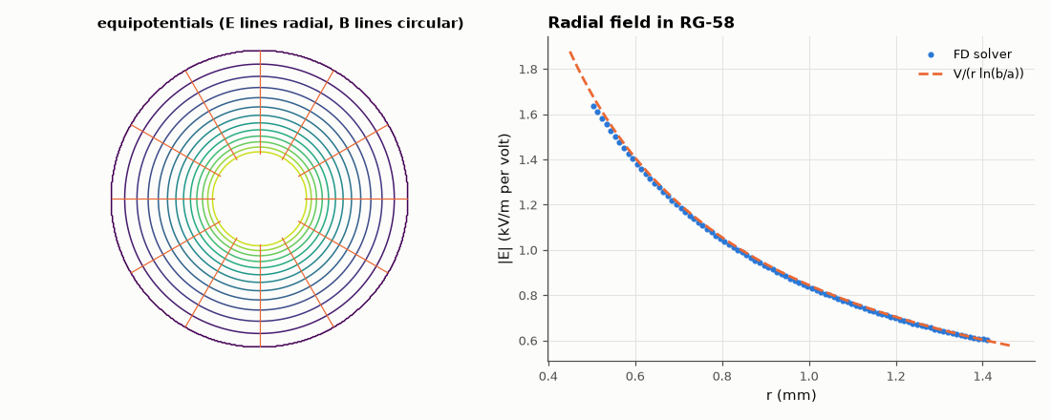
projects/signal-lab/G-electromagnetics-and-device-physics/SL126-coaxial-cable-field-plot/figures/coax.png
