nyquist-labs/projects/projects/signal-lab/G-electromagnetics-and-device-physics/SL128-biot-savart-coil-fields/figures/helmholtz.png

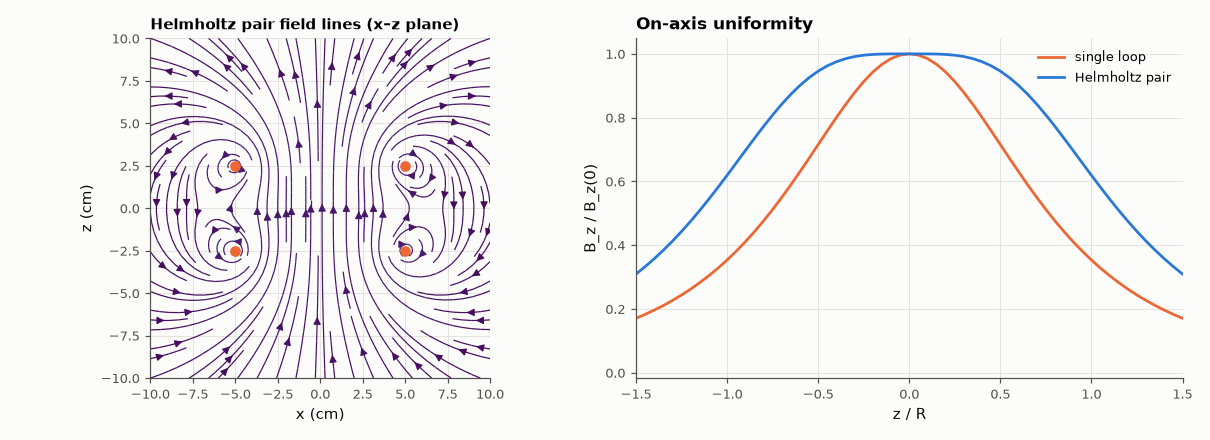
projects/signal-lab/G-electromagnetics-and-device-physics/SL128-biot-savart-coil-fields/figures/helmholtz.png
