nyquist-labs/projects/projects/signal-lab/G-electromagnetics-and-device-physics/SL131-transformer-coupling-model/figures/coupling.png

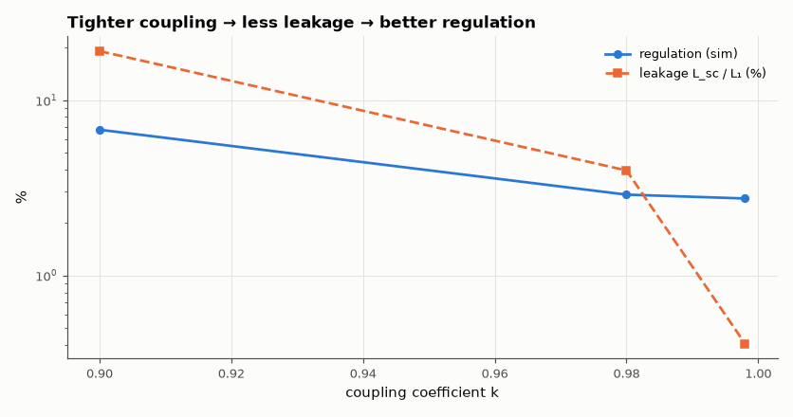
projects/signal-lab/G-electromagnetics-and-device-physics/SL131-transformer-coupling-model/figures/coupling.png
