nyquist-labs/projects/projects/signal-lab/H-embedded-systems/SL137-pwm-led-fade/figures/breathing.png

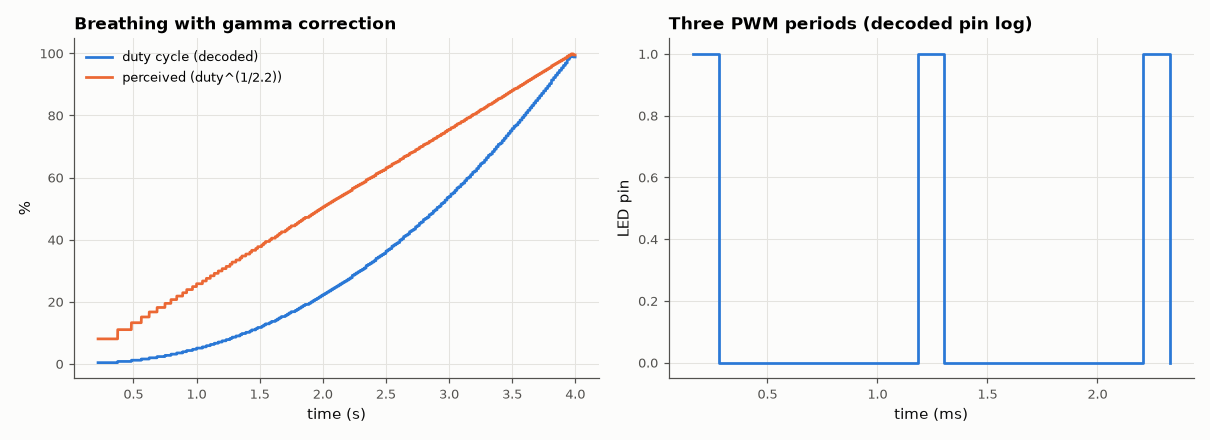
projects/signal-lab/H-embedded-systems/SL137-pwm-led-fade/figures/breathing.png
