nyquist-labs/projects/projects/signal-lab/H-embedded-systems/SL138-i2c-sensor-reader/figures/i2c.png

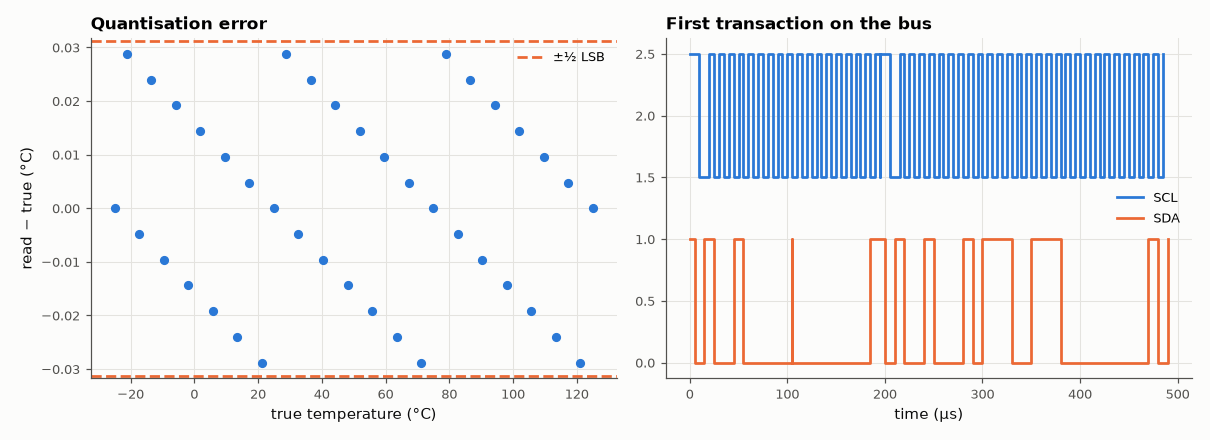
projects/signal-lab/H-embedded-systems/SL138-i2c-sensor-reader/figures/i2c.png
