nyquist-labs/projects/projects/signal-lab/H-embedded-systems/SL142-rotary-encoder-decoder/figures/encoder.png

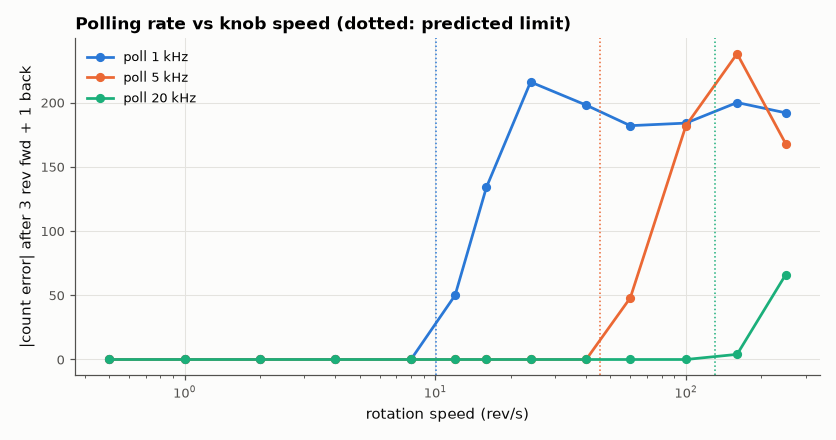
projects/signal-lab/H-embedded-systems/SL142-rotary-encoder-decoder/figures/encoder.png
