nyquist-labs/projects/projects/signal-lab/H-embedded-systems/SL143-matrix-keypad-scanner/figures/keypad.png

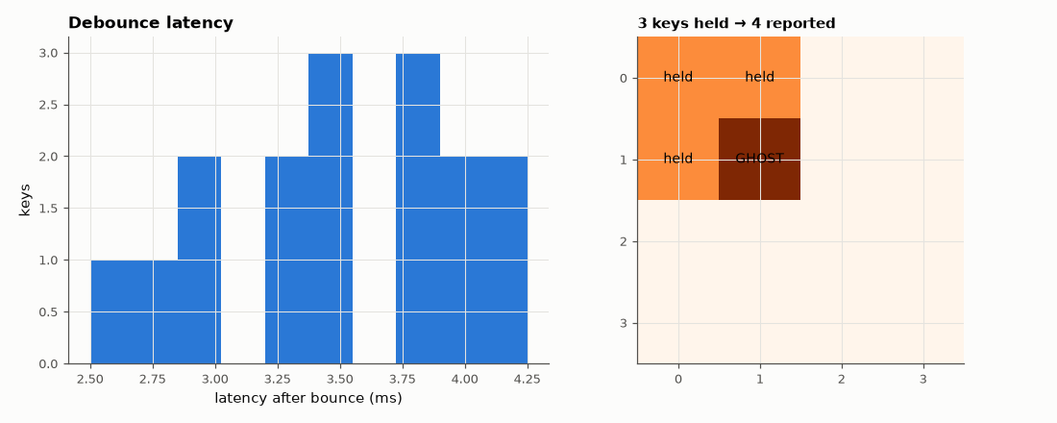
projects/signal-lab/H-embedded-systems/SL143-matrix-keypad-scanner/figures/keypad.png
