nyquist-labs/projects/projects/signal-lab/H-embedded-systems/SL144-data-logger/figures/lifetime.png

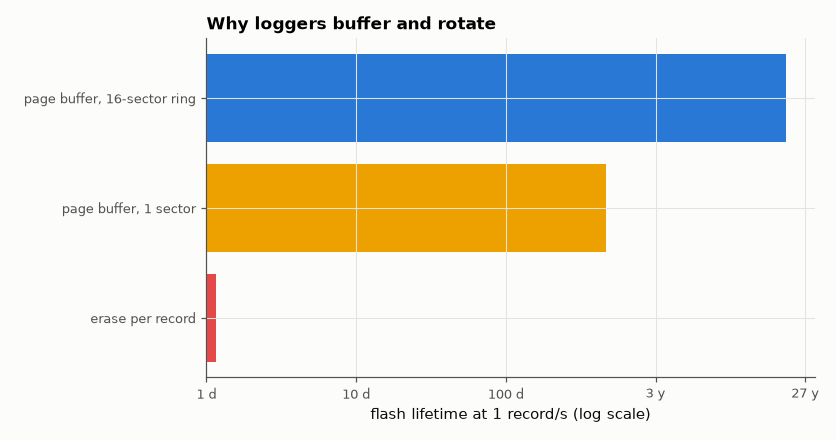
projects/signal-lab/H-embedded-systems/SL144-data-logger/figures/lifetime.png
