nyquist-labs/projects/projects/signal-lab/H-embedded-systems/SL146-bit-banged-spi/figures/softspi.png

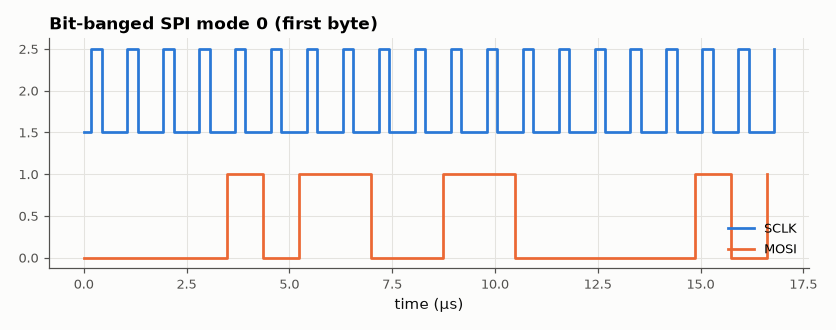
projects/signal-lab/H-embedded-systems/SL146-bit-banged-spi/figures/softspi.png
