nyquist-labs/projects/projects/signal-lab/H-embedded-systems/SL148-dac-waveform-generator/figures/dds.png

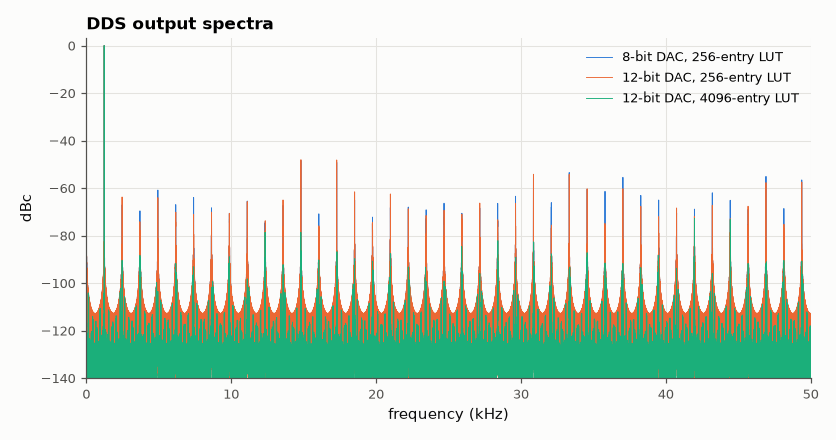
projects/signal-lab/H-embedded-systems/SL148-dac-waveform-generator/figures/dds.png
