nyquist-labs/projects/projects/signal-lab/H-embedded-systems/SL150-mqtt-publisher/figures/mqtt.png

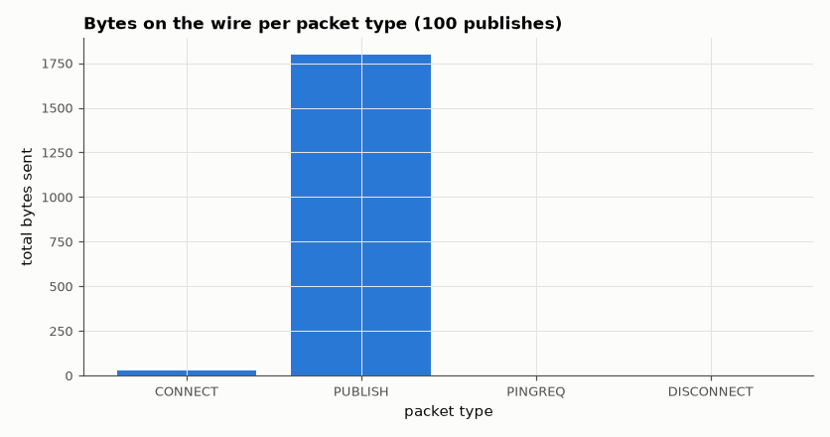
projects/signal-lab/H-embedded-systems/SL150-mqtt-publisher/figures/mqtt.png
