nyquist-labs/projects/projects/signal-lab/H-embedded-systems/SL151-esp32-web-server/figures/latency.png

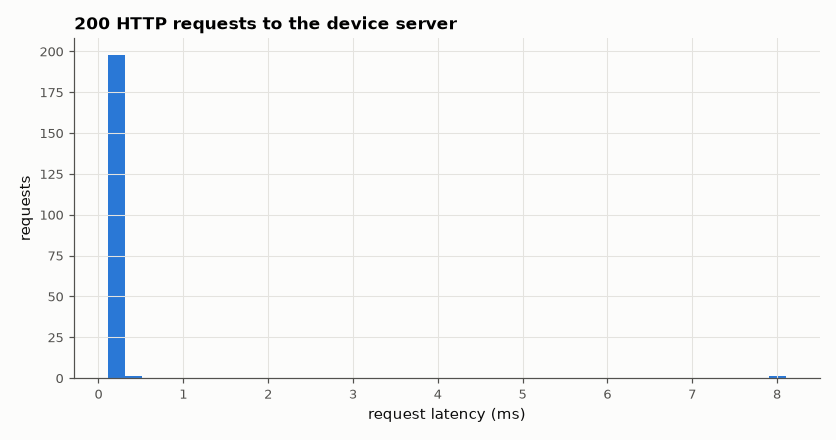
projects/signal-lab/H-embedded-systems/SL151-esp32-web-server/figures/latency.png
