nyquist-labs/projects/projects/signal-lab/H-embedded-systems/SL153-can-bus-simulation/figures/can.png

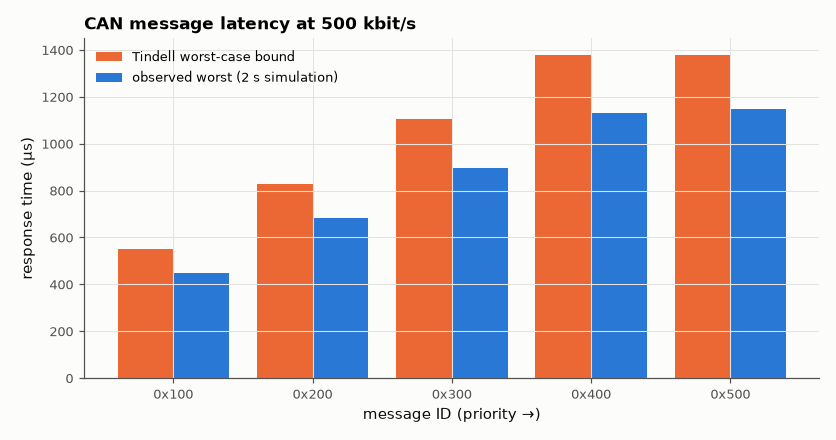
projects/signal-lab/H-embedded-systems/SL153-can-bus-simulation/figures/can.png
