nyquist-labs/projects/projects/signal-lab/H-embedded-systems/SL154-low-power-state-machine/figures/budget.png

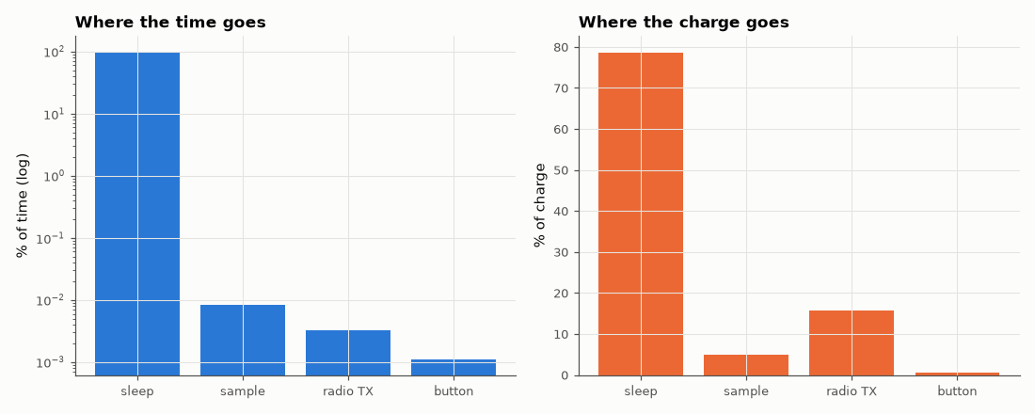
projects/signal-lab/H-embedded-systems/SL154-low-power-state-machine/figures/budget.png
