nyquist-labs/projects/projects/signal-lab/H-embedded-systems/SL155-custom-wokwi-chip/figures/dac.png

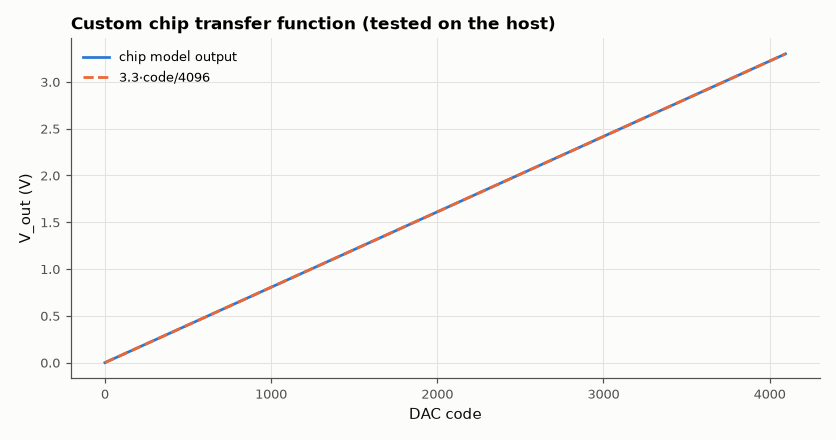
projects/signal-lab/H-embedded-systems/SL155-custom-wokwi-chip/figures/dac.png
