nyquist-labs/projects/projects/signal-lab/I-control-systems/SL163-bode-nyquist-analysis-tool/figures/margins.png

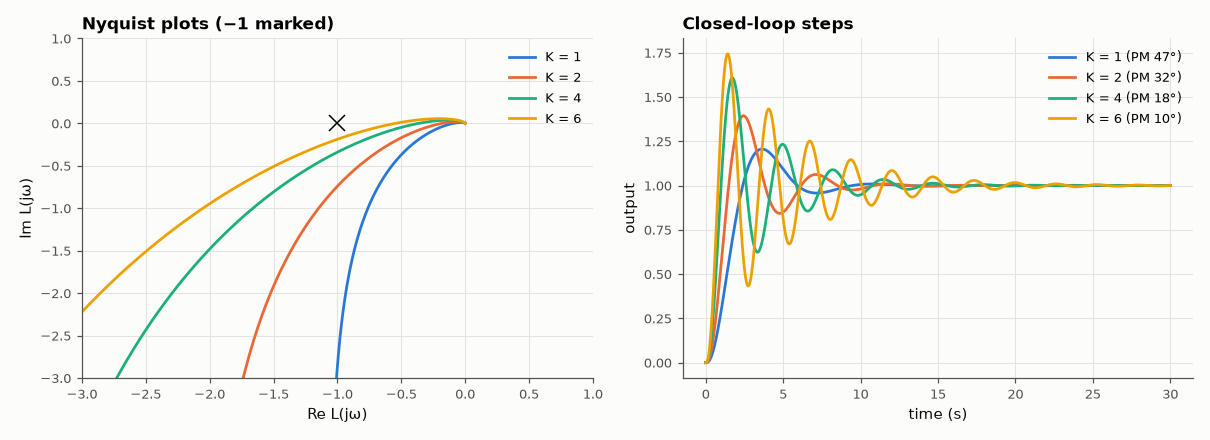
projects/signal-lab/I-control-systems/SL163-bode-nyquist-analysis-tool/figures/margins.png
