nyquist-labs/projects/projects/signal-lab/I-control-systems/SL165-state-space-controller/figures/two_mass.png

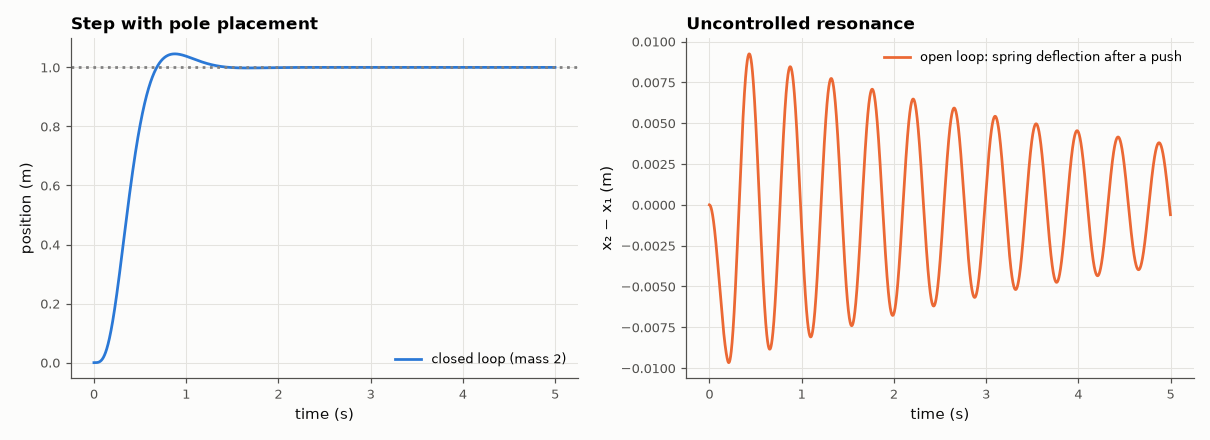
projects/signal-lab/I-control-systems/SL165-state-space-controller/figures/two_mass.png
