nyquist-labs/projects/projects/signal-lab/J-biosignals-and-hci/SL173-heart-rate-variability/figures/hrv.png

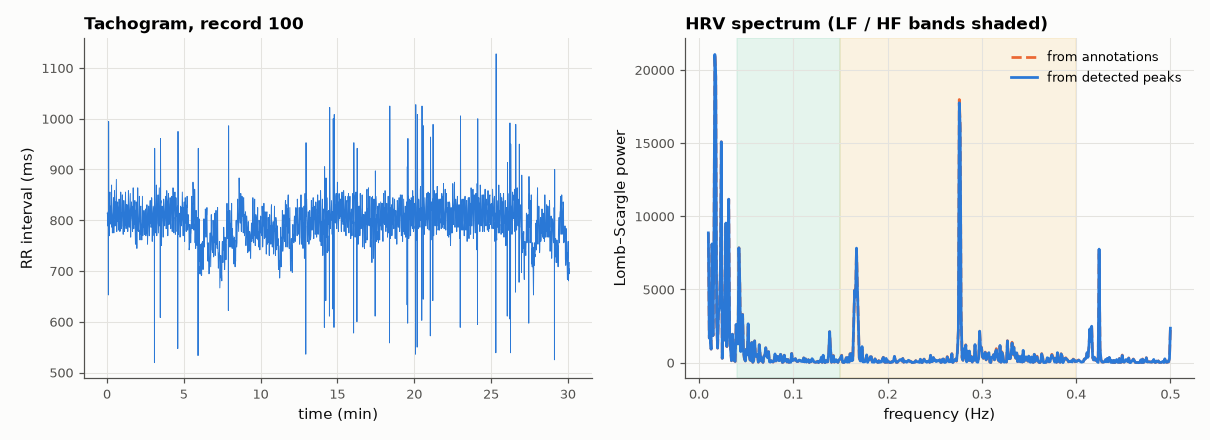
projects/signal-lab/J-biosignals-and-hci/SL173-heart-rate-variability/figures/hrv.png
