nyquist-labs/projects/projects/signal-lab/J-biosignals-and-hci/SL175-ecg-denoising/figures/denoise.png

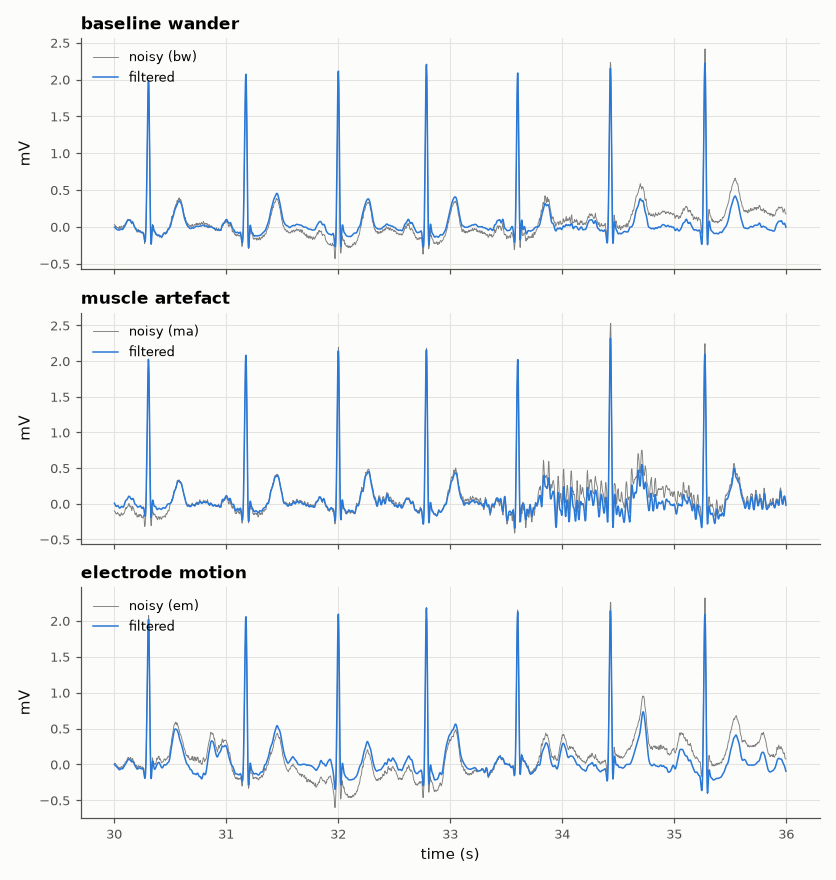
projects/signal-lab/J-biosignals-and-hci/SL175-ecg-denoising/figures/denoise.png
