nyquist-labs/projects/projects/signal-lab/J-biosignals-and-hci/SL176-emg-envelope-extraction/figures/emg_envelope.png

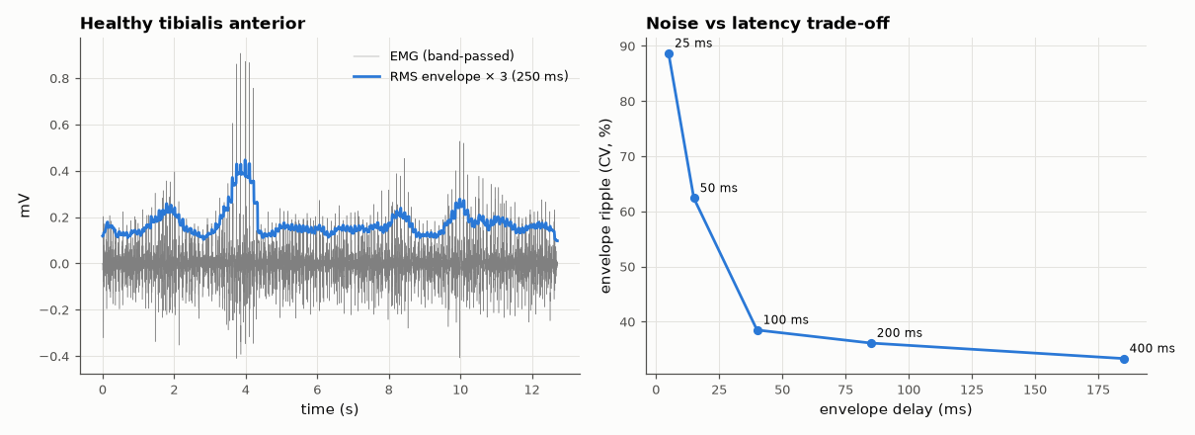
projects/signal-lab/J-biosignals-and-hci/SL176-emg-envelope-extraction/figures/emg_envelope.png
