nyquist-labs/projects/projects/signal-lab/J-biosignals-and-hci/SL179-eeg-alpha-wave-detection/figures/alpha.png

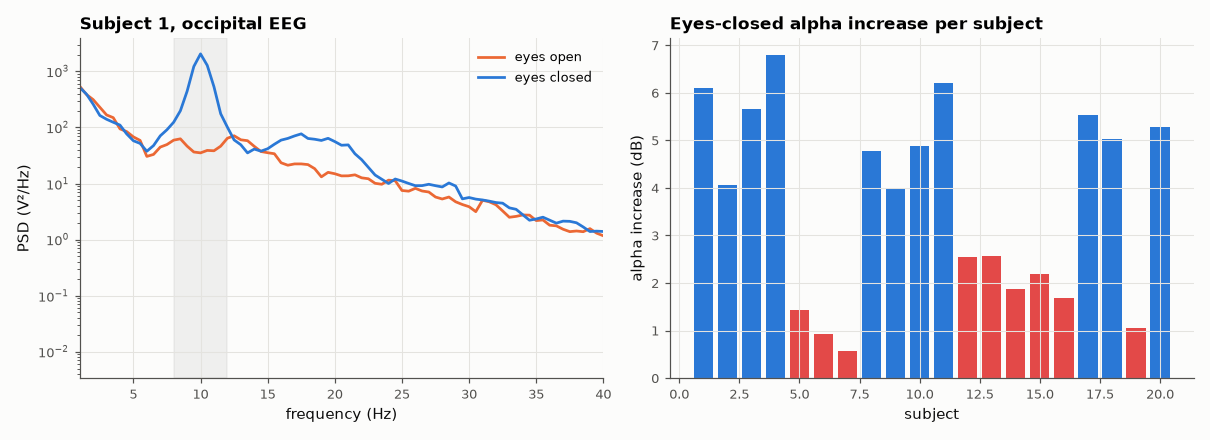
projects/signal-lab/J-biosignals-and-hci/SL179-eeg-alpha-wave-detection/figures/alpha.png
