nyquist-labs/projects/projects/signal-lab/J-biosignals-and-hci/SL181-motor-imagery-bci/figures/bci.png

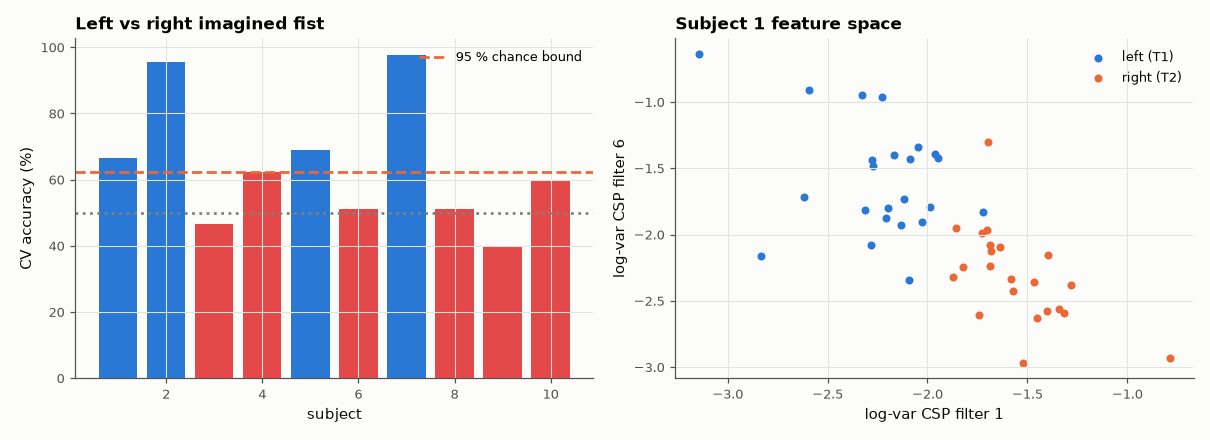
projects/signal-lab/J-biosignals-and-hci/SL181-motor-imagery-bci/figures/bci.png
