nyquist-labs/projects/projects/signal-lab/J-biosignals-and-hci/SL182-ppg-heart-rate-extraction/figures/ppg_ecg.png

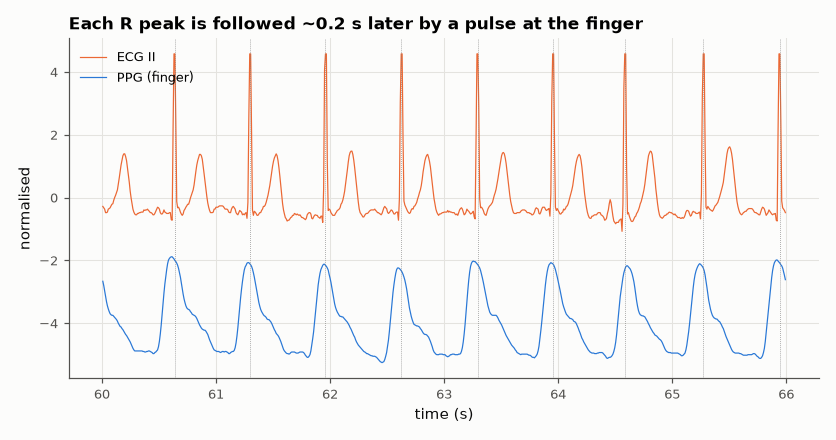
projects/signal-lab/J-biosignals-and-hci/SL182-ppg-heart-rate-extraction/figures/ppg_ecg.png
