nyquist-labs/projects/projects/signal-lab/J-biosignals-and-hci/SL183-respiration-from-ecg/figures/edr.png

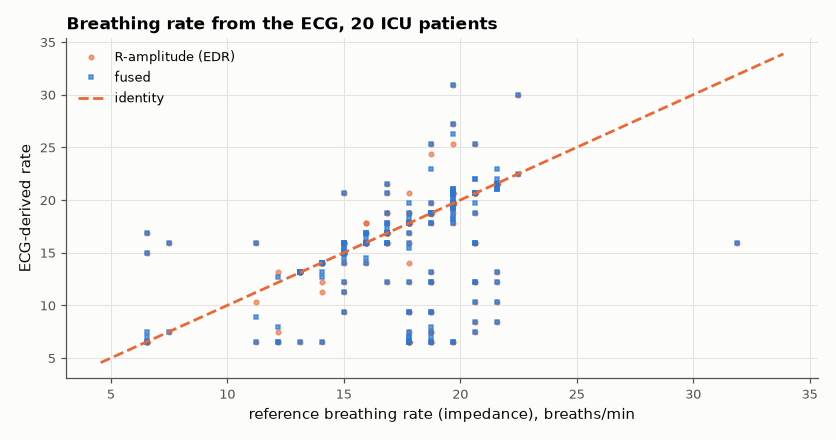
projects/signal-lab/J-biosignals-and-hci/SL183-respiration-from-ecg/figures/edr.png
