nyquist-labs/projects/projects/signal-lab/J-biosignals-and-hci/SL185-seizure-detection/figures/smoothed_detector.png

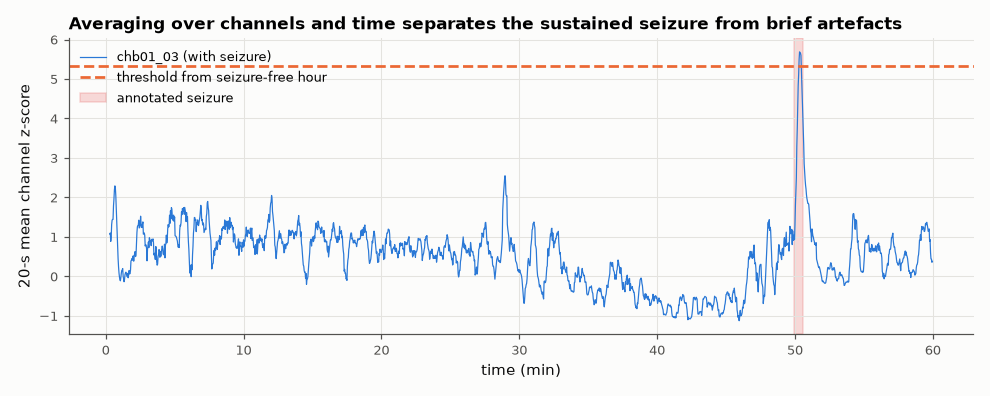
projects/signal-lab/J-biosignals-and-hci/SL185-seizure-detection/figures/smoothed_detector.png
