nyquist-labs/projects/projects/signal-lab/J-biosignals-and-hci/SL186-eog-eye-movement-analysis/figures/eog.png

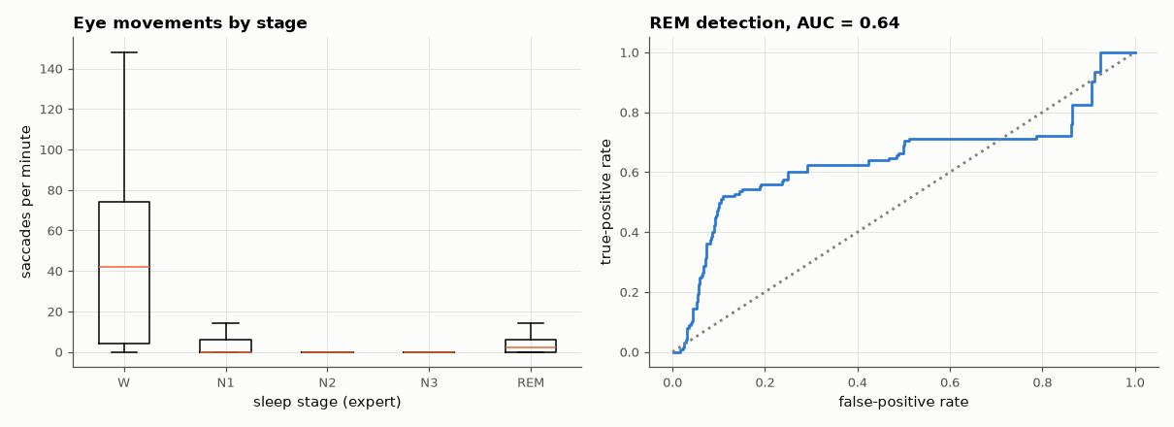
projects/signal-lab/J-biosignals-and-hci/SL186-eog-eye-movement-analysis/figures/eog.png
