nyquist-labs/projects/projects/signal-lab/K-interactive-tools-and-web-apps/SL200-db-dbm-watts-converter/figures/levels.png

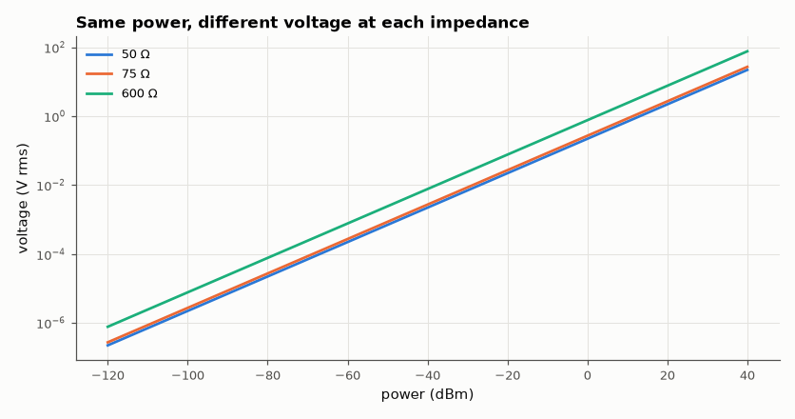
projects/signal-lab/K-interactive-tools-and-web-apps/SL200-db-dbm-watts-converter/figures/levels.png
