nyquist-labs/projects/projects/signal-lab/K-interactive-tools-and-web-apps/SL202-pcb-trace-width-calculator/figures/thermal.png

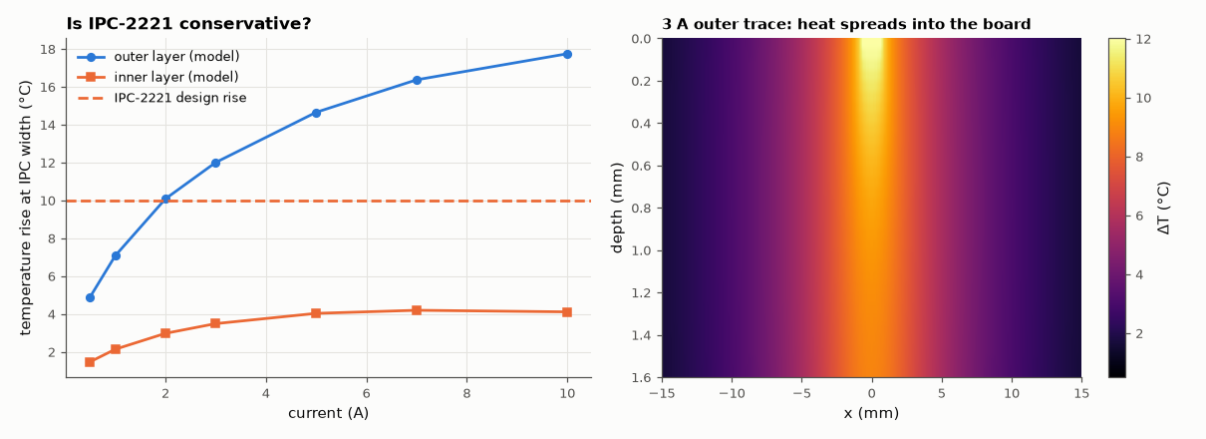
projects/signal-lab/K-interactive-tools-and-web-apps/SL202-pcb-trace-width-calculator/figures/thermal.png
