nyquist-labs/projects/projects/signal-lab/K-interactive-tools-and-web-apps/SL203-unit-converter-for-ee/figures/awg.png

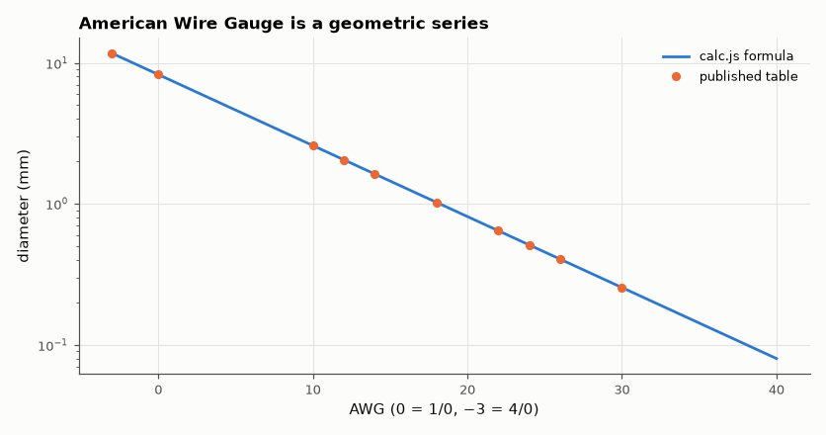
projects/signal-lab/K-interactive-tools-and-web-apps/SL203-unit-converter-for-ee/figures/awg.png
