nyquist-labs/projects/projects/signal-lab/K-interactive-tools-and-web-apps/SL204-bit-manipulation-visualiser/figures/pitfalls.png

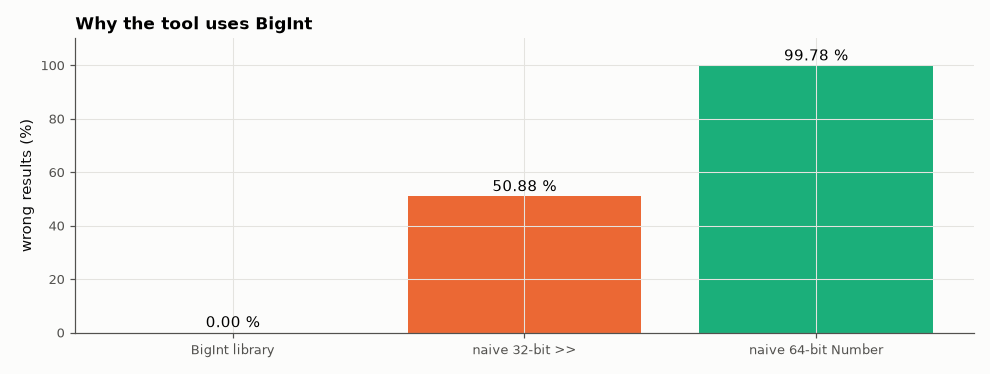
projects/signal-lab/K-interactive-tools-and-web-apps/SL204-bit-manipulation-visualiser/figures/pitfalls.png
