nyquist-labs/projects/projects/applied-math/C-differential-equations/AM047-euler-vs-rk4-for-circuits/figures/orders.png

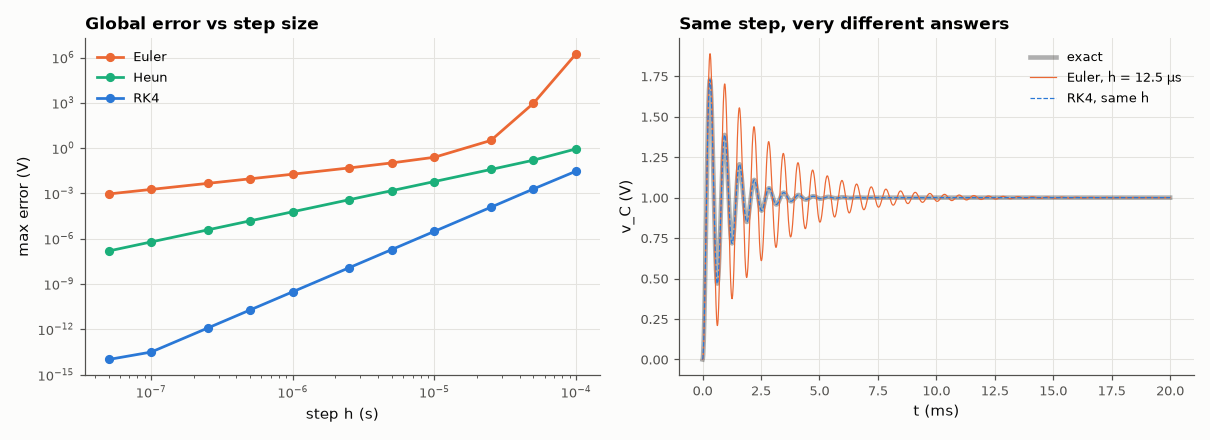
projects/applied-math/C-differential-equations/AM047-euler-vs-rk4-for-circuits/figures/orders.png
