nyquist-labs/projects/projects/signal-lab/G-electromagnetics-and-device-physics/SL136-mosfet-characteristics/data/transfer.csv

vgs | id_lin | id_sat
0 | 2.68224e-16 | 3.59684e-16
0.005 | 3.1125e-16 | 4.17381e-16
0.01 | 3.61177e-16 | 4.84333e-16
0.015 | 4.19113e-16 | 5.62024e-16
0.02 | 4.86343e-16 | 6.52178e-16
0.025 | 5.64357e-16 | 7.56794e-16
0.03 | 6.54884e-16 | 8.7819e-16
0.035 | 7.59933e-16 | 1.01906e-15
0.04 | 8.81832e-16 | 1.18253e-15
0.045 | 1.02328e-15 | 1.37221e-15
0.05 | 1.18743e-15 | 1.59233e-15
0.055 | 1.3779e-15 | 1.84775e-15
0.06 | 1.59892e-15 | 2.14414e-15
0.065 | 1.8554e-15 | 2.48807e-15
0.07 | 2.15301e-15 | 2.88717e-15
0.075 | 2.49837e-15 | 3.35029e-15
0.08 | 2.89911e-15 | 3.88769e-15
0.085 | 3.36414e-15 | 4.51129e-15
0.09 | 3.90376e-15 | 5.23492e-15
0.095 | 4.52992e-15 | 6.07461e-15
0.1 | 5.25653e-15 | 7.04899e-15
0.105 | 6.09967e-15 | 8.17966e-15
0.11 | 7.07805e-15 | 9.49167e-15
0.115 | 8.21336e-15 | 1.10141e-14
0.12 | 9.53075e-15 | 1.27808e-14
0.125 | 1.10594e-14 | 1.48308e-14
0.13 | 1.28333e-14 | 1.72096e-14
0.135 | 1.48917e-14 | 1.99699e-14
0.14 | 1.72801e-14 | 2.31729e-14
0.145 | 2.00517e-14 | 2.68896e-14
0.15 | 2.32677e-14 | 3.12024e-14
0.155 | 2.69995e-14 | 3.62069e-14
0.16 | 3.13298e-14 | 4.2014e-14
0.165 | 3.63545e-14 | 4.87524e-14
0.17 | 4.2185e-14 | 5.65714e-14
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
