nyquist-labs/projects/projects/signal-lab/D-digital-signal-processing/SL060-fft-from-scratch/figures/benchmark.png

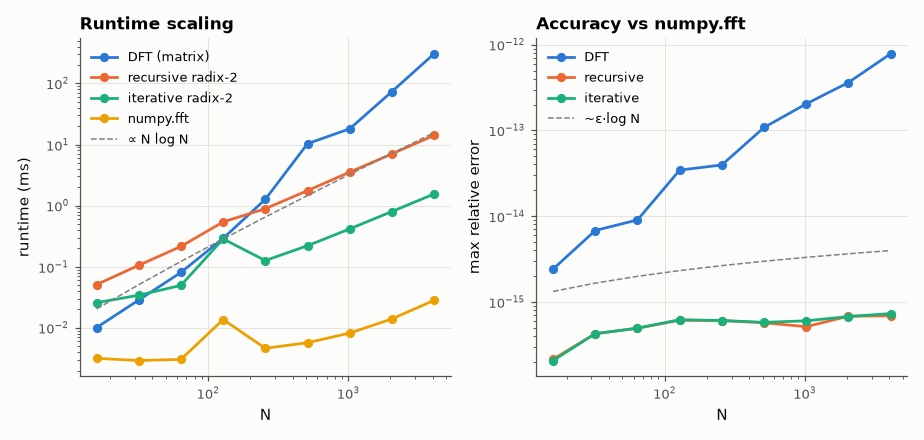
projects/signal-lab/D-digital-signal-processing/SL060-fft-from-scratch/figures/benchmark.png
