nyquist-labs/projects/projects/signal-lab/D-digital-signal-processing/SL083-browser-audio-analyzer/figures/verification.png

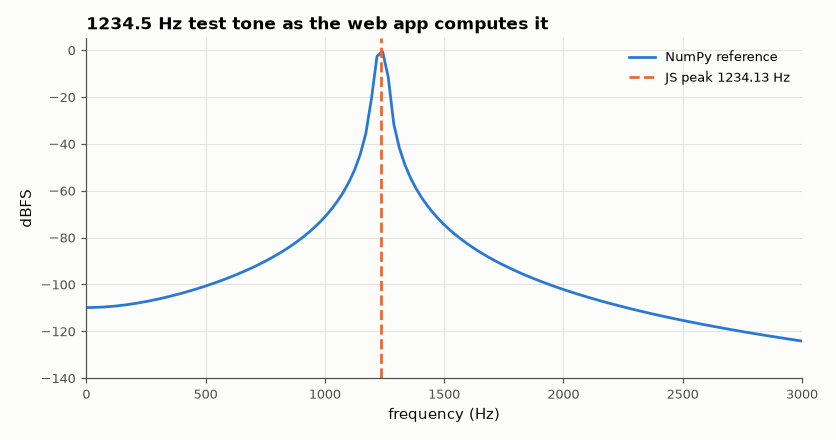
projects/signal-lab/D-digital-signal-processing/SL083-browser-audio-analyzer/figures/verification.png
