nyquist-labs/projects/projects/signal-lab/K-interactive-tools-and-web-apps/SL197-logic-gate-playground/figures/tests.png

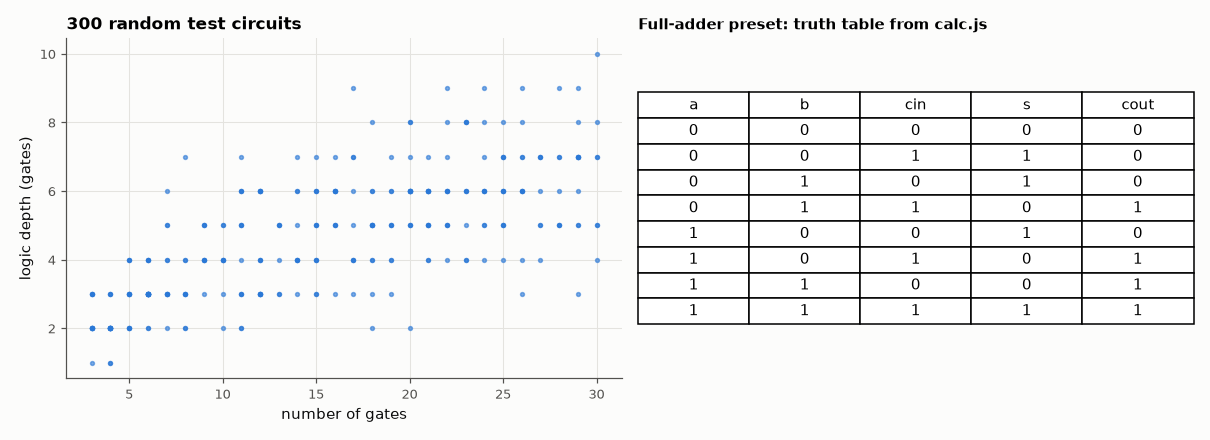
projects/signal-lab/K-interactive-tools-and-web-apps/SL197-logic-gate-playground/figures/tests.png
