nyquist-labs/projects/projects/signal-lab/A-analog-circuit-design/SL001-rc-lowpass-filter/simulation/rc_lowpass.cir

* RC low-pass — exported by eelab.circuit
Vin src 0 DC 0 AC 1  ; time-varying in eelab
Rs src a 50
R1 a out 1600
C1 out 0 1e-07
Rprobe out 0 1e+07
Cprobe out 0 1.2e-11
.end
