nyquist-labs/projects/projects/signal-lab/E-rf-radio-and-satellites/SL103-matching-network-designer/simulation/l_match.cir

* L-match — exported by eelab.circuit
Vs src 0 DC 0.0 AC 1
Rs src in 50
Lx in mid 1.03451e-07
Cb in 0 3.1831e-11
Rl mid lc 25
Cl lc 0 3.97887e-11
.end
